Michi71/PicoVintageSynthCollection/tools/jv_extract/README.md

# jv_extract - JV-880 ROM extraction and parameter analysis

Host-side toolchain for a planned PicoFaceJV. Nothing here is part of a firmware
image, and no ROM data is in this repository.

The goal is **not** a cycle-exact emulation of the JV-880's CPUs. It is a native
engine that plays the converted PCM data and sounds like the original. That
requires two things from the ROMs: the sample data, and the meaning of the patch
parameters. This directory produces both.

## ROM images

You need your own JV-880 ROM set. Point the tools at a directory containing:

| File | Size | Purpose |
|---|---|---|
| `jv880_rom1.bin` | 32 KB | boot ROM, needed only by the reference emulator |
| `jv880_rom2.bin` | 256 KB | firmware; holds the multisample, sample and patch tables |
| `jv880_waverom1.bin` | 2 MB | wave data, scrambled |
| `jv880_waverom2.bin` | 2 MB | wave data, scrambled |
| `jv880_nvram.bin` | 32 KB | needed only by the reference emulator |

The SR-JV80 expansion boards are deliberately out of scope.

## Wave data format

Each 1 MB ROM page is self-contained:

```
  page + 0x00000 .. 0x07FFF   exponent nibbles, one per 16 samples
  page + 0x08000 .. 0xFFFFF   8-bit signed DPCM deltas
```

A sample is reconstructed by accumulating `delta << exponent`; the nibble for
address `a` sits at `(a & 0xFFFFF) >> 5` with bit 4 selecting high or low nibble.
Both wave ROMs are additionally scrambled by a fixed 20-bit address and 8-bit
data permutation (`descramble()` in `jv_rom.py`).

Verification: all 577 samples decode without a single clipped accumulator,
median peak 7.7 % of 20-bit full scale. Sample 0 (lowest split of "Ac Piano 1",
root key 40) has a loop period of 382 samples, implying 31.5 kHz -- the JV-880's
native rate.

## Tables in rom2

| Table | Offset | Layout |
|---|---|---|
| Multisamples | `0x0004` | 129 x 60 B: 12 B name, 15 split keys, 16 x uint16be sample index |
| Samples | `0x1E41` | 577 x 18 B: start/loop/end (24 bit), root key, tune, level |
| Patches | `0x008CE0` / `0x010CE0` / `0x018CE0` | 3 banks x 64 x 362 B |

A patch is 12 B name + 14 B common + 4 x 84 B tone. See `jv_tone_map.h`.

## Tools

| File | What it does |
|---|---|
| `jv_rom.py` | descrambling, table parsing, DPCM decoding, WAV dump. Importable; run directly for a ROM-set summary. |
| `jv_probe.cpp` | differential probe harness. Reads probe specs on stdin, renders each on the reference emulator, writes one CSV feature row per probe. |
| `jv_analyze.py` | `effects` / `curves` / `shape` views over that CSV. |
| `jv_tone_map.h` | the patch/tone layout, with each field marked VERIFIED or UNVERIFIED. |
| `jv_fx_taps.cpp` | address trace of the effect chip's delay memory. Run it through `build_fx_taps.sh`; see "The reverb, and where it stops". |
| `build_fx_taps.sh` | generates a hooked copy of the emulator's `pcm.cpp` into a scratch directory, builds the trace against it, runs it. |

### Building the probe

`jv_probe.cpp` links against the reference emulator, which is **not** vendored
here (see "Credit" below). Point it at your own checkout of
`giulioz/jv880_juce`; it needs only the emulator core, not the JUCE-coupled ROM
loader, because it brings its own:

```bash
JV=/path/to/jv880_juce/Source/emulator
c++ -O2 -std=c++17 -I"$JV" -I"$JV/resample" -o jv_probe tools/jv_extract/jv_probe.cpp \
    "$JV"/mcu.cpp "$JV"/mcu_opcodes.cpp "$JV"/mcu_interrupt.cpp "$JV"/mcu_timer.cpp \
    "$JV"/pcm.cpp "$JV"/submcu.cpp "$JV"/lcd.cpp "$JV"/resample/*.c
```

The emulator chatters on stderr while it boots; redirect it (`2>/dev/null`) or
the noise lands between the CSV rows.

### Running a sweep

Probe specs are `<label> <tone> <offset> <value>`. Lines labelled `#base` are
applied to the patch before every probe. Offset `-1` means "no modification".
A negative tone index addresses the patch bytes directly instead of a tone.

```bash
{ printf '#base 1 0 0\n#base 2 0 0\n#base 3 0 0\n'
  for o in $(seq 52 66); do for v in 0 16 32 48 64 80 96 112 127; do
    echo "P_${o}_${v} 0 $o $v"      # byte set on the live tone
    echo "C_${o}_${v} 3 $o $v"      # same byte on a switched-off tone
  done; done
} | ./jv_probe /path/to/roms 52 48 100 > sweep.csv

python3 tools/jv_extract/jv_analyze.py curves sweep.csv
```

## Two traps

Both of these produced confident, completely wrong results before they were
found. Anyone extending this work needs to know them.

**1. `SC55_Reset()` does not reset the emulator.** PCM, timer and resampler
state survive it, and so does `samplesError`. Results became order-dependent.
The harness therefore constructs a **fresh `MCU` per probe**. With that, four
repetitions of the same probe render bit-identically -- the noise floor is
exactly zero, so any difference at all is real.

**2. The firmware's patch-parse path takes different amounts of time depending
on which byte was touched**, which shifts the whole render by a few samples.
Summary features (level, pitch, release) cannot tell that apart from a genuine
parameter change: 27 unrelated offsets showed one identical phantom signature.
It surfaced only through a control experiment -- setting the same byte on a
*switched-off* tone produced a byte-identical render, and a silent tone cannot
change the sound.

Hence every measurement is **paired**: the byte is set both on the live tone and
on a switched-off one. The parse-timing shift is identical in both, so a
byte-identical render means the parameter is inert, and any difference is a real
effect. This is what `jv_analyze.py` compares -- never a probe against a global
baseline.

A consequence worth planning for: a parameter can only be measured on a base
patch that actually uses its section. A pipe-organ patch leaves 49 of the 84
tone bytes inert. Pick base patches by section usage, not by name.

## Calibration

Knowing *which* byte is the release time is not enough to build an engine; it
has to know that value 80 means 3.2 seconds. `JV_DUMP=<dir>` makes `jv_probe`
write the raw stereo render of every probe (float32 interleaved, note-off at
frame `JV_HOLD * 32000`), and `JV_HOLD` / `JV_REL` set the render length in
seconds. `jv_calibrate.py` turns those dumps into `jv_calibration.h`.

Results are in [`jv_calibration.h`](jv_calibration.h). The headline findings:

| Quantity | Law | Valid range |
|---|---|---|
| Envelope segment, falling | `t = 56.7 ms * 2^(v/13.98)` to −40 dB, R²=0.996 | v=16…112 |
| Envelope segment, rising | `t = 67.6 ms * 2^(v/14.06)` to 98 %, R²=0.997 | v=16…112 |
| TVF cutoff | `fc = 431 Hz * 2^(v/17.93)`, 67 cents/step, R²=0.984 | v=8…84 |
| LFO rate | `f = 0.122 Hz * 2^(v/18.20)` | whole range |
| LFO delay / fade | `32.3 ms * 2^(v/12.0)` / `17.5 ms * 2^(v/10.5)` | v≳40 |
| TVA level, pan | tables (not a clean power law) | full |

**Envelope shape is direction-dependent** and this matters more than the times:
rising segments ramp *linearly in amplitude*, falling segments decay *linearly
in dB*. Both were measured at ten equal time points across several rates; the
rising shape is identical at every rate.

**The time is the segment's DURATION, not a rate.** At T1 = 80 the attack takes
about 3.4 s whether its target level is 64, 96 or 127 — a constant rate would
have given 1.7 / 2.6 / 3.5 s. This matters far beyond the timing: a stage whose
target equals the current level is a *hold*, and reading the time as a rate
collapses it to nothing. Several factory pads (B19 "Beauty Vox", B21 "Pvox
Oooze") have L1 = L2 = 127 and stuttered because of it.

### The measurement setup is the hard part

Two things silently ruined earlier runs, both worth repeating:

* **The base patch's own LFO.** Pipe Organ (A24) carries `lfo1TvaDepth = 255`.
  Its tremolo swamped the amplitude envelope, so attack curves came out
  oscillating instead of rising. Every calibration base must zero the six LFO
  depth bytes (+31…+36).
* **Reverb and chorus sends.** Left at patch defaults they add a tail that gets
  measured as release time. Set +82 and +83 to 0, +81 to 127.

The base used for all of it is a sine wave (multisample 72), single tone, LFOs
off, sends dry, filter open, envelope levels at maximum — so that the one byte
under test is the only thing moving.

### Envelope target levels

The TVA envelope's target levels (+75/+77/+79) do **not** follow the tvaLevel
curve, which the engine assumed at first. Measured by setting every segment time
to 0 and every target to the same value -- the envelope then holds there -- the
two curves differ by up to **9.4 dB** at low levels. Above roughly L=32 the
envelope curve is linear at 0.30 dB per unit.

The TVF envelope's levels are a different quantity again: they scale the cutoff
excursion and are **near-linear in the parameter**, not logarithmic. Normalised
to L=127 they run 0 / 0.09 / 0.20 / 0.28 / 0.46 / 0.56 / 0.72 / 0.83 / 1.0 at
L=0…127, where the dB curve would give 0.09 at L=32 instead of 0.20.

**Four** level-shaped quantities, and no two share a curve:
`JV_TVA_LEVEL_DB` for tone levels, `JV_PATCH_LEVEL_DB` for the patch-common
level, `JV_TVA_ENV_LEVEL_DB` for TVA envelope targets, `JV_TVF_ENV_LEVEL` for
TVF envelope targets. Assuming one curve for all of them was wrong four times
over; each was settled by patching the byte and reading the sustained level.

And a fifth candidate that turned out not to be one: **byte +17 of a sample
record is not a level**. Patched across its whole range, including 0, it moved
the output by 0.00 dB. The engine had been multiplying by it, which wrongly
attenuated the 233 of 577 samples carrying anything other than 127 -- by up to
6.4 dB, and one of them to silence.

### Pan does not stop at 127

`tvaPan` (+68) has three regimes, found by sweeping the whole byte rather than
the 0..127 the field looks like:

| value | behaviour |
|---|---|
| 0…127 | the continuous law: 0 left, 64 centre, 127 right |
| **128** | **alternating** -- the balance jumps between 0.119 and 0.768 from one note to the next |
| 129…255 | centre |

**139 of the 539 active factory tones carry 128.** Clamping it to 127, as the
engine did, threw all of them hard right with the left channel 39 dB down.
"Whistle" has 128 on all four of its tones, which is why it measured 14 dB quiet
-- the mono sum had lost a whole channel.

### Tone summing

Not a factor. Enabling the four tones of "Pipe Organ 1" one at a time, the
machine gains +2.3 / +0.3 / +1.2 dB and the engine +2.8 / +0.5 / +0.4 dB, so
there is no hidden per-tone attenuation; only a constant offset separated them.

### Filter chain, measured against the reference

The low-pass slope is **−10 to −12 dB/octave**, so the two-pole assumption is
right, and the transfer function tracks the reference to 1–4 dB across four
cutoff settings. The filter is not where the remaining timbre error lives.

Worth recording as a method note: an earlier comparison normalised each spectrum
to its own maximum and read single FFT bins, which suggested a 26 dB error at
1 kHz. Measured absolutely and in third-octave bands, the same patch is within
1.8 dB up to 4 kHz and only +3.5/+7.4 dB at 8/12 kHz -- consistent with the
chip's three-coefficient interpolation over the deltas against the engine's
linear interpolation, which is a real but much smaller difference.

### Where it is incomplete

* **Cutoff above v≈84** cannot be measured this way: the corner moves past the
  bandwidth of the white-noise sample used as excitation. A wider excitation
  (or a swept sine) would extend it.
* **Flags bit 5** of either LFO (see "Key sync and offset" above).
* **tvfEnvDepth (+58)** moves the cutoff by 2.4 parameter units per depth unit
  (measured 19.1 / 37.5 / 60.5 at depth 8 / 16 / 24, with the envelope held
  open); above 24 the measurement saturates, not the synth. The field is signed.
* **tvaVelocity (+72) only ATTENUATES.** Measured against sensitivity 0 at the
  *same* velocity -- a comparison the first calibration never made -- every
  setting gives an identical level at velocity 127, and softer notes get quieter
  in proportion: -1.56 / -3.10 / -4.91 dB at velocity 100 for sensitivities
  8 / 16 / 25, and -3.59 / -7.52 / -11.62 dB at velocity 64. The attenuation
  tracks the product `sensitivity * (127 - velocity)`.

  RE-MEASURED on a full grid -- nine sensitivities against eight velocities,
  63 usable points -- after a listening report that middle velocities came out
  too quiet. The product model itself holds: three independent settings near
  product 1500 give 9.82 / 10.33 / 10.51 dB and near 2000 give 13.01 / 13.01 /
  13.51. What was wrong was the curve through them. The old table was built
  from just two velocities, 100 and 64, and ran 1 to 3 dB too steep through the
  middle of the range -- exactly where MIDI files live -- and badly steep at the
  top: 45.25 dB against the machine's 37.78 at product 3969.

  With the new table the engine reproduces the grid to a mean absolute error of
  **0.33 dB** over all 63 points, against roughly 1 dB before.

  Worth being clear about what this did NOT fix. Measured per patch, the drop
  from velocity 127 to 64 is now right on ten patches and slightly too shallow
  on eleven; before it was uniformly a little too steep. The isolated law being
  accurate to 0.33 dB while whole patches still scatter by about a decibel says
  a second mechanism is involved -- most likely the TVF velocity sensitivity,
  which darkens the tone at lower velocity and takes level with it. That is the
  next thing to measure.

  The first model boosted above velocity 64 instead. Because factory patches
  carry sensitivities of 13..42, that spurious boost had been standing in for a
  10.5 dB base offset in the output normalisation, and the two together looked
  acceptable in aggregate while scattering wildly per patch. Fixing the law and
  moving the normalisation cut the spread across 24 patches from 5.1 dB to
  2.7 dB. The lesson is in the comparison that was missing: every velocity
  measurement had been relative to velocity 64 at the same sensitivity, so a
  term that shifts the whole curve was invisible.
* **LFO depths are signed over the whole byte.** 64..127 really is inert, but
  128..255 is -128..-1 and modulates the *other way*: pitch depth -20 gives
  133 cents of swing around a mean above the carrier, +20 gives 136 cents around
  a mean below it. An earlier sweep only covered 0..127 and wrongly concluded
  that everything from 64 up was off. On the TVA the negative side is inaudible
  at full level, because there is no headroom to modulate upward into.
* **Resonance** is calibrated (see the matrix section); the LFO's TVF depth
  is not.

## Pitch: the sample table, resolved

The `tune` word had resisted a structural reading, so it was settled the same
way the patch bytes were — by **patching rom2 itself** and measuring. `jv_probe`
takes `#rom <offset> <value>` lines for exactly this; they are applied before
the MCU starts, so any ROM table can be probed the way patch bytes are.

| Field | Law | Evidence |
|---|---|---|
| root key (+12) | exact semitones | −199.9 / −200.2 cents per +2, five values |
| `tune` (+13/+14, 16-bit BE) | **0.1 cent per unit, neutral at 1024** | low byte 0.098–0.100 cents/unit over six values; high byte 0.1005 |
| `pitchFine` (tone +38) | 1 cent per unit, signed | 0.989–1.001 cents/unit over eight values |
| machine tuning | 9.4 cents flat | constant to 1 cent across 2.5 octaves |

**`end` is inclusive**: a loop spans `end − loop + 1` samples. This was the
thing that made everything else look inconsistent. Treating `end` as exclusive
detunes a sample by 1731/looplen cents — 9 cents on a 193-sample loop but 54 on
a 32-sample one — so the error masqueraded as a per-sample `tune` effect that no
single law could fit.

The two readings are cleanly separable. Solving each sine-multisample zone for
the `tune` reference point gives:

| `end` treated as | reference point per zone | scatter |
|---|---|---|
| exclusive | 1207, 1246, 1303, 1371, 1484, 1671 | 157.7 |
| **inclusive** | 1118, 1119, 1119, 1111, 1120, 1121 | **3.3** |

and 1118 − 1024 = 94 units = 9.4 cents, which is exactly the machine's measured
offset from equal temperament. The neutral value really is 0x400 after all;
what was missing was the off-by-one and the global detune sitting on top of it.

Engine error against the reference afterwards: **0.2 to 0.7 cents** across all
nine zones of the sine multisample, down from +22…+105 cents. On real
multi-tone patches the residual is 5 cents mean / 9 cents worst, which is
dominated by f0 estimation over detuned layers rather than by the model.

### LFO

Waveform comes from bits 0-2 of the flags byte, classified by correlating the
measured dB envelope against ideal shapes: **0/6/7 triangle** (0.990),
**1 sine** (0.990), **2 sawtooth** (0.986), **3 square** (0.984). Values **4 and
5 are not periodic** — only 21 % of their samples sit on a smooth slope against
99-100 % for the rest — so both are treated as sample-and-hold.

Depth is effective for **0..63 only**; every value from 64 up reproduced the
unmodulated signal exactly, so it disables the modulation rather than inverting
it. An earlier note calling these fields "bipolar, split at 64" was wrong.

Both destinations modulate **one-sided downward** from the set value: with
rising TVA depth the peak stayed at −15.0…−15.9 dBFS while the trough fell to
−62.5 dBFS, and the mean pitch dropped from 261 to 194 Hz.

An earlier claim here — that no modulation exists below rate ≈48 — was also
wrong. Re-measured with a 46 dB tremolo over 24 s and counting cycles directly,
the LFO runs at every rate value and matches the fitted law to ~1 % from v=40 up;
below that the cycle count is the limit, not the law. The original measurement
had an autocorrelation locking onto its search bound.

#### Key sync and offset

**Bit 6 is key sync.** Told apart by shifting the note-on in time (`JV_WARM`)
and timing the first square-wave edge. With the bit clear, the edge moves so
that edge+shift stays constant modulo the period — a free-running LFO. With it
set, the edge sits at 227.7–237.7 ms regardless of the shift, scatter 3.4 ms
against ~56 ms for free-running.

Phase 0 is the **unmodulated** end. The 227 ms is a useful cross-check on two
earlier results at once: half a period (194.7 ms at rate 80) plus the 32.3 ms
floor of the delay law.

**Bits 3-4 are an offset that shrinks the swing from the bottom.** The peak does
not move (−15.1…−15.2 dBFS across all four settings) and neither does the phase
(first edge 237.6–239.0 ms, duty 49–50 %); only the trough rises. At TVA depth
63 the swing goes 48.7 / 30.6 / 19.4 / 9.9 dB, and the triangle agrees
(48.1 / 29.5 / 18.5 / 9.0). Stored as a scale factor on the depth.

**Bit 5 is not resolved.** Alone it silences the modulation; combined with
either of bits 3-4 the swing collapses to a fixed 19.4 dB regardless of which,
which no plain offset field explains. The engine ignores it.

#### LFO 2 is the same device

Probed separately rather than assumed. Rate follows the same law (within 1 %
from v=56 up; the 12 % at v=32 is cycle-count quantisation, not a difference),
the four periodic waveforms have the same shapes at the same codes, value 4 is
equally aperiodic, depth follows the same table and is equally disabled from 64
up, key sync behaves the same (scatter 45.4 ms free-running against 3.2 ms
synced), and the four offset settings give **bit-identical** swings to LFO 1
(48.7 / 30.6 / 19.4 / 9.9 dB, difference −0.0 dB throughout).

The two also free-run in lockstep: at equal rates their first square edges land
on the same milliseconds.

### Modulation matrix

Its three sources — mod wheel (CC 1), aftertouch, expression (CC 11) — need
controller traffic, which a bare note-on does not provide, so `jv_probe` gained
`#midi <seconds after note-on> <status> <d1> [d2]`. Messages are queued, sorted
and injected by splitting the hold render at their timestamps.

**Sensitivity is signed with an effective range of ±63, and 64…127 disables it
outright** — the same convention as the LFO depths. This was the whole reason an
early sweep found nothing: it used sensitivity 127. The pitch destination scales
linearly at **19.05 cents per unit**, reaching exactly ±1 octave at ±63
(measured 18.3 / 37.3 / 94.4 / 188.3 / 377.3 / 765.3 / 1200.2 cents for
1 / 2 / 5 / 10 / 20 / 40 / 63).

Destination A is the **low** nibble of the DestAB byte, B the high one — which
is what the factory patches imply too (Dig Rhodes 1 has expression DestAB = 0x20
with SensA = 0 and SensB = 20, so the active destination sits in the high
nibble alongside the active sensitivity).

| Code | Effect | How it was told apart |
|---|---|---|
| 0 | off | — |
| 1 | **pitch** | +376 cents; the ×1.55 brightness is exactly the side effect of the shift on a sine |
| 2 | **cutoff** | corner ×2.50 with the filter enabled |
| 3 | **resonance** | spectral peak +4.4/+8.4/+12.6 dB at sensitivity 20/40/63, against +3.5/+9.0/+12.5 dB for resonance set directly to 30/90/127 |
| 4 | **level** | +4.3 dB, nothing else moves |
| 5, 6 | **LFO 1 / 2 pitch depth** | the pitch wobbles rather than steps; source identified by rate |
| 11-15 | nothing measurable | — |
| 7, 8 | **LFO depth → filter** | oscillation index ×45 / ×34 at the LFO rate |
| 9, 10 | **LFO depth → level** | oscillation index ×73 / ×57 |

The LFO destinations were separated from the static ones by running the LFO at a
known rate with all depths at zero and testing whether the controller introduces
a periodic component at that rate. It is an unambiguous split: the four LFO
codes jump 34–73×, everything else stays at or below 1.1×.

Which LFO each of 7-10 drives was settled by giving the two LFOs different rates
and seeing which one the induced oscillation follows: **7 = LFO 1 filter,
8 = LFO 2 filter, 9 = LFO 1 level, 10 = LFO 2 level**. Adding sensitivity 63 at
full travel reproduces full depth (47.7 dB against the depth table's 46.6), so
the matrix adds straight onto the depth parameter.

Scalings, all with the wheel swept 0 -> 127: pitch **19.05 cents/unit** (exactly
±1 octave at ±63), cutoff **~128 cents/unit**, level non-linear and saturating
near **+6.3 dB** (1.29 / 2.37 / 4.31 / 6.28 dB at sensitivity 5 / 10 / 20 / 40).

Destinations 5 and 6 took two attempts and are worth a warning. Averaged over a
long window their pitch looks like a small static shift, which is what the first
sweep concluded; tracked in 0.12 s windows it plainly wobbles instead of
stepping. At sensitivity 40 the swing reaches 4000 cents, enough to make an
autocorrelation tracker jump octaves and smear the rate across both LFOs — only
at sensitivity 4-8 does the source come out unambiguous. Destination 6 had been
written off as "nothing measurable" for the same reason.

The matrix's pitch-depth contribution is linear **in cents** (55 and 122 cents
at sensitivity 4 and 8), not in depth-parameter units as the level and filter
depths are.

Resonance needed the engine's filter damping calibrated as well: peak gain
against the passband is +1.0 / +3.5 / +6.2 / +9.0 / +12.5 dB at resonance
0 / 30 / 60 / 90 / 127, which fixes k = 1/Q. The first mapping was a guess and
overshot by 7 dB at the top.

Still not established: whether the B/C/D slots behave like A, destinations
11-15, and behaviour on real multi-tone patches — see below.

#### What the engine does and does not reproduce

Against the controlled synthetic base the engine matches: pitch to 0.6-3.8
cents across the whole sensitivity range including the disable above 63, level
exactly, cutoff to 83-173 cents, LFO-depth destinations to 0.1-3.0 dB.

On **real factory patches it is not verified**. The patches that use the matrix
are decaying Rhodes and piano sounds whose own envelope contaminates a
before/after window comparison — the oscillation detector reads a decay ramp as
modulation, so it cannot separate the two. A10 "SA Rhodes" (destination 10,
sensitivity 20, on three tones) is the concrete case: the reference's level
rises 2.4 dB with the wheel, the engine's falls 2.9 dB, and the measurement is
not good enough to say which is right.

### Zone selection, verified

`splits[k]` is the **inclusive upper bound** of zone k: zone 0 covers notes up
to `splits[0]`, zone k covers `splits[k-1]+1 .. splits[k]`, and the last zone
runs to 127. Verified by repointing one zone's entry in the multisample index
table at the white-noise sample (516) and sweeping notes: 34 boundary tests
across all nine zones of the sine multisample, all correct.

Pitch is the wrong observable for this. A first attempt shifted a zone's sample
root by an octave and looked for the jump; it produced a self-contradictory map
(note 87 apparently in a different zone than 86 and 88) because the f0 estimator
was locking onto harmonics. The noise marker has no such ambiguity — the
separation is absolute:

| | measurements | spectral flatness |
|---|---|---|
| note outside the patched zone | 16 | 0.000000, every one |
| note inside it | 18 | 0.000477 … 1.000000 |

The low readings are not weak detections: the noise sample transposed down two
octaves is no longer spectrally flat, but it is still unambiguously not the sine.

### Velocity curves, and a trap worth naming

The seven velocity curves (+55 bits 0-2 for the TVF, +71 bits 0-2 for the TVA)
were first implemented from the icons the manual prints, which put an `x^2` law
on stored curve 0. That quietly took 3 dB off half the factory patches. The
sweep that replaced it -- a tone forced to a flat sustain at velocity
sensitivity 32, read at nine velocities for each of the seven settings -- gives
`JV_VELO_CURVE` in jv_calibration.h and settles three things:

* All seven curves produce **exactly the same level at velocity 127**. That is
  the anchor, the same one the sensitivity law itself uses.
* **Stored curve 0 is the straight line.** Expressing each curve as "the
  velocity curve 0 would need to reach the same level" makes curve 0 an exact
  identity, which is the right footing because `JV_TVA_VELO_ATTEN_DB` was itself
  measured on curve 0.
* The reparameterisation holds across sensitivities. Repeating the sweep at
  sensitivity 16 reproduced curve 1's effective velocities to within 1.5 units
  wherever both are well conditioned, so the curve warps velocity *before* the
  sensitivity law rather than acting on the result.

Checked against the reference on real patches, the drop from velocity 127 to
100 is 8.76 / 8.22 / 13.71 dB on A37, B06 and B50 against 8.98 / 8.18 / 14.14
predicted with the curve and 4.28 / 3.87 / 7.03 without it. A11 lands between
the two, which is right: it is the one of those patches that mixes curve 0 and
curve 1 across its tones.

**The trap.** Fixing this made the aggregate level error look *worse* -- and it
was the third time in this work that a wrong law and the output normalisation
had silently absorbed each other. A velocity-law error is indistinguishable
from a level offset unless the comparison is made at more than one velocity.
Two habits catch it:

* Always compare at both velocity 127 and something well below it. Before the
  curves the engine was flat at one velocity and 4-5 dB out at the other; the
  single-velocity summary showed neither.
* Match the measurement windows. `jv_probe` reports rms over the HELD portion
  only (`N = nHold`), while `jv_engine_test` reports it over hold plus release.
  Comparing the two directly puts a patch-dependent 3 dB bias on every reading,
  which is enough to hide or invent an error of exactly the size being chased.

With the curves in and the normalisation re-trimmed by 1.0 dB (99000 ->
88234), the level error over all 128 factory patches at velocities 127 and 100
is mean +0.15 dB, spread 3.0 dB, mean absolute 2.32 dB -- and the velocity
TRACKING error, which is what the curves actually fix, falls from a mean of
1.22 dB to 0.72 dB with the worst case down from 6.7 to 5.0 dB.

### The machine is at equal temperament, and the 9.4 cents were counted twice

The engine carried a global `kMasterTuneCents = -9.4`, documented here as a
measured property of the machine. It is not one. The reference playing the
ROM's own sine (multisample 72) sits at **+0.11 / +0.18 / +0.08 cents** against
equal temperament at C3, C4 and C5 -- dead in tune. The engine was 9.65 cents
flat, and removing the constant lands it at +0.12 / +0.19 / +0.13.

9.4 cents is real, but it belongs to the tune-word model: it is the residual
left over when the sample tune words are referenced to a neutral of 1024.
Applying it again as a global detune counted it a second time. The whole
instrument played ten cents flat, which is inaudible on its own and obvious
against anything else.

That is the same shape as the two velocity traps below, and the third instance
in this work: a constant belonging to one part of the chain quietly standing in
for an error elsewhere, invisible until something *outside* the chain is
measured. Here the outside reference was equal temperament itself.

### The loop throb: alternating loops, and a test that lied

**Resolved.** Bit 0 of a sample record's flag byte (+11) marks an **alternating
loop**: playback turns around at the end and retraces the loop backwards rather
than jumping to the start. 85 of the 577 samples set it, and they are the long
sustained ones -- median loop length 8998 against 152 for the rest. Playing
those as forward loops makes the sound repeat exactly once per loop, which is
audible as a throb at the loop rate: 2.43 Hz for the sample under B16.

**The return pass is NEGATED.** The chip does not undo the differential steps
on the way back. It keeps integrating in the same direction while the address
walks backwards, so what comes out is `2*v(end) - v(mirrored)`. The loop
endpoints sit on zero crossings -- `v(end)` is exactly 0 for every sample
checked -- so that is the negated mirror of the forward pass.

Retracing the arithmetically "correct" way, `v(a-1) = v(a) - delta(a)`, gives
the un-negated mirror. Against the reference that reads **r = -0.995** through
the whole return pass: perfectly shaped, exactly the wrong sign. It is audible
as a tick at each turn-around, since the waveform jumps to its own negative
there. Adding the delta instead of subtracting it takes the same comparison to
**+0.99**.

With that, the engine tracks the reference sample for sample: aligning on a
window at 200 ms and then measuring 50 ms windows out to 1.8 s gives r = 0.92
to 1.00 throughout, across four turn-arounds, with the alignment drifting only
from +86 to +90 samples (about a cent of rate difference).

The measured signature, engine against reference, envelope correlation at one
loop period across the seven notes of one multisample zone:

| note | reference | forward loop | alternating |
|---|---|---|---|
| 55 | -0.369 | +0.434 | -0.302 |
| 57 | -0.388 | +0.544 | -0.342 |
| 59 | -0.333 | +0.692 | -0.453 |
| 60 | -0.441 | +0.705 | -0.382 |
| 62 | -0.512 | +0.595 | -0.466 |
| 64 | -0.591 | +0.627 | -0.537 |
| 66 | -0.572 | +0.753 | -0.519 |

And directly: comparing one loop pass against the next, the reference matches
its own **reverse** at +0.899 while matching forward at -0.046. The engine gave
+0.871 forward before this and now shows the reference's signature instead.

**The test that lied.** Alternating looping was the second hypothesis tried and
was wrongly discarded, because the first version of the test correlated one
half-period against the reversed next half-period from an *arbitrary* window
start. The turn-around point sits at the loop boundary, so an unaligned window
straddles a reversal and the correlation collapses -- it read +0.076 and sent
the search off for six other explanations. Scanning the window offset instead
of assuming one makes the peak obvious. When a structural hypothesis is
rejected, check whether the test could see it at all before believing the
result.

Bit 1 of the same byte marks a one-shot: all 42 samples carrying it have
`loop == end`, so the forward path already holds on the last value. Bit 2 is
still unidentified, on 15 samples.

### What it was not

B16 was the clean test case: one tone, every LFO depth zero, no random pitch,
no analog feel, no FXM, pan centre -- a single unmodulated sample, so anything
periodic had to come from the playback. These were eliminated on the way, and
each elimination is still worth having:

* **The chorus.** These patches are built around a deep slow chorus that the
  engine does not have, which was the obvious suspect. But switching the chorus
  off on the reference leaves it just as non-periodic (r at the loop period goes
  from -0.34 to -0.30).
* **The DPCM accumulator, and the decode rule.** The loops are authored exactly
  balanced: the drift over one pass is precisely zero for all three samples
  involved, under every plausible variant of the decode step (`s>>1`, `s`,
  truncate-toward-zero, round-half-up). The `refAtLoop` snapshot the engine
  restores on each wrap is therefore a no-op for these samples, and removing it
  would change nothing.
* **A loop-length parity effect.** An odd loop length would flip the alignment
  of the DPCM exponent nibbles every pass, which would explain a two-pass cycle.
  Patching sample 287's `end` in rom2 to make the length even (12779 -> 12778)
  moves the reference's r only from -0.44 to -0.28. Not it.
* **A discontinuity in the engine.** There is none. Replaying the engine's own
  decode and loop logic step by step across the wrap gives
  `... -872, 0, +888, +1768 ...` -- perfectly smooth -- and the rendered
  waveform either side of the boundary is continuous sample for sample. What
  looked like a step in a 10 ms envelope is a fast but continuous swell that
  sits at the boundary because the sample's own amplitude pattern restarts
  there. That is the whole point: it restarts EXACTLY.
* **The loop being twice as long as read.** The reference's best repeat is at
  831 ms, twice the period, which would fit `end` being misread. It is not:
  the next sample record starts 5 bytes after sample 287 ends, so there is no
  data for a longer loop.
* **A fractional-phase effect.** The engine advances only 0.1 to 0.8 output
  samples per pass depending on note, and its correlation shows no relation to
  that fraction; neither does the reference's.

Each of these was a real elimination, and the sample data being provably
periodic while the address returns to exactly the same place is what finally
pointed at the traversal itself rather than the data.

### Still open

* **Cutoff above v≈84** and the **LFO below v≈48** (see Calibration above).
* **tvfEnvDepth (+58)** moves the cutoff by 2.4 parameter units per depth unit
  (measured 19.1 / 37.5 / 60.5 at depth 8 / 16 / 24, with the envelope held
  open); above 24 the measurement saturates, not the synth. The field is signed.
* **tvaVelocity (+72) only ATTENUATES.** Measured against sensitivity 0 at the
  *same* velocity -- a comparison the first calibration never made -- every
  setting gives an identical level at velocity 127, and softer notes get quieter
  in proportion: -1.56 / -3.10 / -4.91 dB at velocity 100 for sensitivities
  8 / 16 / 25, and -3.59 / -7.52 / -11.62 dB at velocity 64. The attenuation
  tracks the product `sensitivity * (127 - velocity)`.

  RE-MEASURED on a full grid -- nine sensitivities against eight velocities,
  63 usable points -- after a listening report that middle velocities came out
  too quiet. The product model itself holds: three independent settings near
  product 1500 give 9.82 / 10.33 / 10.51 dB and near 2000 give 13.01 / 13.01 /
  13.51. What was wrong was the curve through them. The old table was built
  from just two velocities, 100 and 64, and ran 1 to 3 dB too steep through the
  middle of the range -- exactly where MIDI files live -- and badly steep at the
  top: 45.25 dB against the machine's 37.78 at product 3969.

  With the new table the engine reproduces the grid to a mean absolute error of
  **0.33 dB** over all 63 points, against roughly 1 dB before.

  Worth being clear about what this did NOT fix. Measured per patch, the drop
  from velocity 127 to 64 is now right on ten patches and slightly too shallow
  on eleven; before it was uniformly a little too steep. The isolated law being
  accurate to 0.33 dB while whole patches still scatter by about a decibel says
  a second mechanism is involved -- most likely the TVF velocity sensitivity,
  which darkens the tone at lower velocity and takes level with it. That is the
  next thing to measure.

  The first model boosted above velocity 64 instead. Because factory patches
  carry sensitivities of 13..42, that spurious boost had been standing in for a
  10.5 dB base offset in the output normalisation, and the two together looked
  acceptable in aggregate while scattering wildly per patch. Fixing the law and
  moving the normalisation cut the spread across 24 patches from 5.1 dB to
  2.7 dB. The lesson is in the comparison that was missing: every velocity
  measurement had been relative to velocity 64 at the same sensitivity, so a
  term that shifts the whole curve was invisible.
* **LFO depths are signed over the whole byte.** 64..127 really is inert, but
  128..255 is -128..-1 and modulates the *other way*: pitch depth -20 gives
  133 cents of swing around a mean above the carrier, +20 gives 136 cents around
  a mean below it. An earlier sweep only covered 0..127 and wrongly concluded
  that everything from 64 up was off. On the TVA the negative side is inaudible
  at full level, because there is no headroom to modulate upward into.
* **Resonance** is calibrated (see the matrix section); the LFO's TVF depth
  is not.
* **tvfVelocity (+56)** is calibrated. Measured with the TVF envelope held wide
  open over a base cutoff of 8, reading brightness back as an effective depth:

      positive sensitivity   f = 1 - (s/32) * (127 - v)/127
      negative sensitivity   f = 1 - (|s|/32) *  v /127

  clamped to 0..1, fitted over 96 points to a mean error of 0.010. The constant
  is **32, not 63** -- sensitivity 32 already takes the depth to zero at
  velocity 0, so the upper half of the field saturates inside the velocity span.
  Assuming 63 by analogy with the other bipolar fields made the effect half as
  strong as the machine everywhere. Positive sensitivity pivots at velocity 127
  like the TVA law; negative pivots at velocity 0.

  Note the measurement trap: brightness stops resolving above envelope depth 32,
  so the first sweep -- run at depth 40 -- read a flat 0.0187 across the whole
  useful range and looked like no effect at all. Depth 28 keeps every reading on
  the curve.

## What the owner's manual adds

The JV-880 owner's manual (Roland, 244 pages, scanned -- no text layer, so it
has to be read as images) turned out to carry two things the probe could not
produce on its own. Section 10's **parameter address map** (printed 10-38 f.)
lists the SysEx view of a tone: 116 addresses, `0x00`..`0x73`, five of them
nibble pairs, which is the same parameter set as the 84 packed bytes here. That
names every field and gives its range. Section 6 then explains what each one
actually does.

The manual is documentation, not measurement: where the two collide the
measurement wins. Its value here was in saying where to point the probe next,
and most of the list below has since been implemented and checked against the
reference. What that pass achieved, over all 128 factory patches:

| metric (vs reference) | before | after |
|---|---|---|
| level, mean absolute error | 2.45 dB | 2.33 dB |
| velocity tracking error, 127 -> 100 | 1.22 dB | 0.72 dB |
| brightness at velocity 64, mean abs err | 10.19 dB | 4.93 dB |

**Resolved outright.**

* **The modulation matrix destination table is complete at 13 entries**, 0..12:
  OFF, PITCH, CUTOFF, RESONANCE, LEVEL, PITCH LFO1, PITCH LFO2, TVF LFO1,
  TVF LFO2, TVA LFO1, TVA LFO2, LFO1 RATE, LFO2 RATE. Codes 13..15 do not
  exist, so the sweep that found nothing there was right. Dest 6 and 11/12 read
  as dead for a duller reason: the base patch had LFO2 pitch depth at zero and
  no LFO running, so there was nothing for them to scale.
* **LFO offset has five settings, not four** (-100/-50/0/+50/+100), so it needs
  three bits and **bit 5 of the LFO flags byte is its top bit** -- which is
  exactly why sweeping bit 5 on its own looked inert. That also means the
  remaining flag is fade polarity IN/OUT.
* **Offset is a shift, not a scale.** `JV_LFO_OFFSET_SCALE` shrinks the swing;
  the manual shows the waveform being pushed until it sits wholly above (+100)
  or wholly below (-100) the centre, at full amplitude. Applied to pitch with a
  square wave that is a one-sided trill, not a weaker vibrato.
* **Fade OUT** runs the LFO at full depth from note-on and fades it away over
  the fade time -- the engine only implements fade IN.
* **LFO delay and tone delay both have a KEY-OFF setting past 127**, holding the
  LFO (or the whole tone) until the key is released.
* **+54 and +40 are keyfollow pairs.** +54 packs cutoff keyfollow (0..15,
  -100..+200 about C4) with the TVF envelope's time keyfollow; +40 packs pitch
  keyfollow (0..15, +100 = the normal octave per twelve keys) with a TVA time
  keyfollow. Cutoff keyfollow is the consequential one: without it every tone
  filters at the same absolute frequency across the whole keyboard.
* **+71 is tone delay mode plus the TVA velocity curve.** NORMAL delays the tone
  and still lets it sound after release, HOLD drops it if the key goes up first,
  PLAY-MATE uses the gap between the last two note-ons as the delay time.
* **+72's upper half is probably the negative side.** The manual gives TVA
  velocity sensitivity as -63..+63, where negative makes *harder* playing
  quieter. The measurement covered only the positive half and called the rest
  inert -- the same shape the LFO depths had before the signed sweep found
  128..255 modulating the other way. Worth the same sweep.

**Since implemented.** How many of the 539 active factory tones each one
actually reaches is what decided the order:

1. **TVF envelope velocity (+56)** -- 336 tones. Measured; see "Still open"
   above for the law. This is what moved the brightness error.
2. **Velocity curves** (+55 and +71, bits 0-2) -- 204 tones on the TVF, 168 on
   the TVA. Measured; see the section above.
3. **Cutoff keyfollow** (+54 low nibble) -- 185 tones. At +100 % the corner
   tracks the keyboard one for one about C4, which falls straight out of the
   already-measured cutoff law: 17.93 parameter units per octave.
4. **TVF envelope release level (+66)** -- 95 tones. The TVF envelope releases
   to its own fourth level, not to zero; releasing to zero shut the filter on
   note-off while the TVA tail was still sounding.
5. **Level and panning keyfollow** (+70 low, +39 high) -- roughly 95 tones
   each. Per-semitone amounts are NOT measured, only the table indices.
6. **The pitch envelope (+40..+51)** -- 68 tones, 33 of them at full depth.
   Depth is signed semitones clamped to ±12; the four levels are bipolar where
   the TVA and TVF levels are unsigned. Runs at control rate.
7. **Pitch keyfollow** (+40 low) -- 32 tones. 507 sit at +100 %, the normal
   octave per twelve keys.
8. **Output dry level (+81)** -- 31 tones, six at or near zero. Those are heard
   only through the effects on the hardware, so with no effects yet they drop
   out; no patch loses all four tones that way.
9. **Random pitch (+39 low)** -- 18 tones -- and **analog feel** (patch common,
   119 of 192 patches). Both exist to stop tones phase-locking; the analog-feel
   magnitude is a guess, flagged in jv_calibration.h.
10. **Per-patch bend range** -- 24 patches bend down further than they bend up.
11. **LFO offset as a three-bit field** and **fade polarity** -- five tones and
    two tones respectively, but see the offset note in jv_calibration.h: the
    neutral index is 2, not 0, which is why the depth tables and the offset
    scale had been cancelling each other unnoticed.

12. **FXM (+02)** -- 24 tones. Measured; see jv_calibration.h. The engine's
    sidebands now sit within 0.3 dB of the reference across the depth range
    (-30.8 / -16.8 / -11.5 / -5.9 dB at depth 0 / 4 / 8 / 15 against
    -30.8 / -16.8 / -11.5 / -6.2).

**Still not implemented.**

* **POLY/SOLO and portamento** (11 and 6 patches). Needs a note stack and a
  glide; the engine is poly-only.
* **Resonance mode SOFT/HARD** (+53 bit 7, 58 tones).
* **Tone delay** (+69/+71) including the HOLD and PLAY-MATE modes.
* **Envelope time keyfollow and the T1/T4 velocity fields** (+42, +57, +73,
  plus the high nibbles of +40/+54/+70). Almost all neutral in the factory
  banks: +42 is (7,7) on 537 of 539 tones.

**Confirmed, no change needed.** The TVA envelope's shape (T1→L1, T2→L2,
T3→L3, hold, then T4→0 with no L4, while the TVF envelope does carry L4);
velocity range lower/upper as a per-tone window; pan L64..63R with 128 as the
setting the panel calls RND; patch level, tone level and the sends all being
independent 0..127 controls.

## The chorus

Measured by isolating it: the tone's dry level at 0 and its chorus send at 127
makes the output nothing BUT the chorus, and cross-correlating that against a
dry render of the same note recovers the delay as a function of time. The ROM's
own white noise (multisample 74) is the source; the sine (72) is better for
anything to do with pitch.

It is a **stereo modulated delay**, base delay 578 samples (18.06 ms), the two
channels sweeping in **antiphase** with a common minimum -- the modulation only
ever lengthens. Depth sets the delay SLOPE, rate sets the LFO period, and the
excursion follows:

    slope     = 1.738 * (depth + 18) samples/s   (252 at full depth)
    f         = 126 / (183 - 1.344 * rate) Hz    (0.69 Hz at 0, 10.2 at 127)
    excursion = slope / (2f)

That reproduces all sixteen measured rate points and four depth points to about
2 %, and correctly predicts that the period does not depend on depth (760 ms at
rate 64 for every depth, measured). Level is exactly linear in the parameter
with a full scale of 1.30; feedback is a comb with `g = 0.72 * fb/127`; bit 7 of
the level byte routes the chorus into the reverb instead of the mix, which
measured as exact silence with the reverb turned down.

Verified against the reference on a sine carrier: peak-to-peak pitch deviation
13.6 / 20.7 / 32.3 cents at depth 32 / 64 / 127 against 13.5 / 20.9 / 32.5, and
level within 0.07 dB.

Three traps, all of which cost time here:

* **The reference's effects DSP needs about 1.5 s from reset.** With the usual
  1 s warm-up the chorus appears to start 454 ms after note-on; with
  `JV_WARM=4` it starts after 20. Every effect measurement needs the longer
  warm-up.
* **Counting zero crossings is a bad period estimator.** It gave alternating
  values that read as a depth-independent constant slope, which is wrong.
  Autocorrelation with proper peak finding -- first local maximum after the
  correlation goes negative -- gives a clean answer.
* **Correlating white noise needs a lag step of 1 and a NORMALISED score.**
  Stepping the lag by 4 misses the peak entirely, and maximising the
  unnormalised correlation tracks the local energy of the dry signal instead of
  the delay. Both produced "no peak anywhere" against a chorus that was in fact
  correct.

**CHORUS2 is the same delay, deeper and faster.** It was written off earlier as
"not a plain modulated delay" because cross-correlation against the dry signal
found no peak at any lag from 0.3 to 125 ms. That was the measurement, not the
effect: at these slopes the delay moves 24 samples inside a 16 ms analysis
window, which smears the peak away entirely. A sine carrier settles it, because
it does not care how fast the delay sweeps -- only where the pitch ends up.
Measured at depth 127: 195.6 cents of peak-to-peak deviation against CHORUS1's
32.5 at every rate, and a period of 576 / 416 / 224 ms against 1120 / 768 / 448
at rate 32 / 64 / 96 -- half, to within 4 %.

Two notes on getting the engine to match it. The slope multiplier that works is
8, not the 6 the cents ratio implies, judged by energy-weighted spectral spread:
10.14 and 15.80 Hz against the reference's 9.27 and 14.79 at depth 64 and 127.
Spread is the measure to trust here -- it needs no peak tracking and reproduces
CHORUS1 to within 8 %, where the pitch tracker gave answers that changed with
the analysis window. And the delay buffer had to grow from 768 to 1280 samples:
CHORUS2 sweeps three times as far as CHORUS1, so the excursion clamp was biting
silently and costing it a third of its deviation.

And one real bug it exposed: reading the delay line at `pos - delay` truncates
toward zero when that goes negative, which yields a NEGATIVE interpolation
fraction and makes the interpolator extrapolate backwards. With the write
pointer cycling 0..767 and the delay at 578..761 it happened three quarters of
the time. Biasing the read position up by a whole buffer length fixes it.

## The reverb, and the two delays hiding in it

Same isolation as the chorus -- dry level 0, reverb send 127, chorus off -- but
with a 50 ms burst and a five second tail, so the render is essentially an
impulse response. All six reverb algorithms come out with the two channels
DECORRELATED: |L/R correlation| < 0.04 over the tail, every type.

**The two delay types are exact.** Measured, not modelled:

    delay time = 2.0 + 3.843 * time ms    (2 / 63 / 124 / 185 / 250 / 311 /
                                           372 / 433 / 490 at time 0..127)
    feedback   = fb/128 - 1/64            (per-repeat ratios 0.234 / 0.484 /
                                           0.734 / 0.984 at fb 32/64/96/127)

PAN-DLY is **two taps on one line, not one tap that alternates sides**. At
feedback 0 the reference already produces two echoes -- 62 ms left and 124 ms
right at time 32 -- so the half-period tap feeds the left channel and the
full-period tap the right, with the feedback going round the full period. That
is why the levels arrive in equal pairs. The engine now reproduces the whole
train: 64 / 126 / 188 / 250 / 316 / 378 ms alternating sides against the
reference's 62 / 124 / 184 / 246 / 306 / 368, decay ratio 0.484 against 0.485,
and peak level 0.1660 against 0.1659.

**The six reverbs are matched, not reproduced.** RT60 is measured per type at
five time settings (`JV_REVERB_TIME_MS`) and the engine runs a Schroeder
comb/allpass network sized to hit it, landing within 1 % everywhere:

| type | t=0 | t=64 | t=127 |
|---|-----|---|---|
| ROOM1 | 281 [276] | 618 [614] | 1130 [1124] |
| STAGE2 | 322 [318] | 1362 [1354] | 5460 [5420] |
| HALL1 | 527 [524] | 1203 [1196] | 3603 [3583] |
| HALL2 | 407 [404] | 1303 [1296] | 6625 [6572] |

The topology is not the chip's, and it shows in the residual: tail level is
2.4 dB out on average (3.4 dB absolute), worst on the room types at very short
decay, where the reference's level falls away faster than a Schroeder network's
does. Reverb time in the factory banks has a median of 80 and only 12 of 125
patches sit below 32, so the fit is good where it is used.

**The reverb type is bits 0-2, not the low nibble.** The manual gives the range
as 0-7 and bit 3 of patch-common +12 is something else, set on 40 of the 192
factory patches. Masking with `0x0F` handed 67 of them a type of 6 or 7 -- DELAY
or PAN-DLY -- so a third of the bank played a hard echo where it should have had
a room or a hall. It sounded exactly like that, and it survived every level and
decay measurement because those were all made by setting the type byte
explicitly to 0..5.

**The tail level is right in isolation and low on real patches.** With the level
table fitted, the isolated reverb matches the reference to 0.0 dB across every
type and time. On A04, whose piano samples decay through the note, the engine's
tail sits about 13 dB low. The reverb is linear, so this is not a gain error: a
comb bank driven by a decaying input accumulates less than the chip's network
does. Same root cause as the burst measurement being 12-41 dB quiet while a
flat-sustain note was 5.7 dB loud -- the build-up differs, and no single gain
fixes both. Open.

Two things worth carrying forward:

* **The two channels need genuinely different comb sets, not a stereo spread.**
  Nudging the right channel's combs by a dozen samples (809/823, 877/887, ...)
  left the engine at +0.85 correlation, because both sides see the same input
  and nearly the same delays. Separate sets -- 809..1049 against 1123..1381 --
  bring it to +0.01.
* **`jv_engine_test` renders whatever hold you ask for now** (`--hold`,
  `--tail`). It used to be fixed at 2 s + 2 s, and comparing that against a
  50 ms burst on the reference smeared every echo into one blob. It looked
  exactly like PAN-DLY putting both taps on both channels, which sent the
  implementation off after a bug that was not there.

## Playing material that was not written for the JV

The machine's velocity response is steep -- across 25 factory patches the median
drop from velocity 127 to 64 is 11.7 dB, and A43 Syn Strat drops 19.6. That is
faithful, and it is also awkward: a sequencer file whose velocities sit between
60 and 100 comes out thin.

The firmware therefore has a VELO page. It scales the incoming velocity toward
127 before the engine sees anything, so 100 % passes it through untouched, 50 %
halves the distance to 127 and 0 % makes every note full strength:

| setting | v=48 | v=64 | v=80 | v=100 | level at v=64 |
|---|---|---|---|---|---|
| Orig | 48 | 64 | 80 | 100 | -- |
| 75 % | 68 | 80 | 92 | 107 | +3 to +4 dB |
| 50 % | 87 | 95 | 103 | 113 | +6 to +8 dB |
| 25 % | 107 | 111 | 115 | 120 | +11 dB |
| 0 % | 127 | 127 | 127 | 127 | +15 to +17 dB |

The mapping happens before the engine, so the velocity curves, both velocity
sensitivities and the per-tone velocity windows all act on the same value.
That last one is the side effect to know about: compressing upward will also
bring in tone layers a patch reserves for hard playing.

## MIDI: what the machine receives

The manual's MIDI implementation (printed 10-32 f.) lists exactly what the
JV-880 accepts, and the firmware now covers that list rather than the handful
of controllers it started with:

| CC | what it does | note |
|----|---|---|
| 0 | bank select, MSB only | 80 user, 81 preset; latched until a program change |
| 1 | modulation | matrix source |
| 5 | portamento time | overrides the patch |
| 6 / 38 | data entry | for RPN |
| 7 | volume | on the machine's own tone-level curve |
| 10 | pan | constant power, 0 left / 64 centre / 127 right |
| 11 | expression | matrix source |
| 64 | hold-1 | |
| 65 | portamento switch | overrides the patch |
| 91 | Effect1 depth | reverb send, scales the whole bus |
| 93 | Effect3 depth | chorus send |
| 100 / 101 | RPN | 0 bend sensitivity, 1 fine tune, 2 coarse tune |
| 120 / 123 | all sound / notes off | |
| 121 | reset all controllers | returns every override to the patch |
| 124-127 | omni / mono / poly | mono forces SOLO, poly forces it off |

Program change reaches all 192 patches: bank 80 gives the 64 user patches, bank
81 splits into A for programs 0-63 and B for 64-127. Before this it could only
move within whichever bank was already selected.

The overrides are deliberately three-state -- CC5, CC65 and mono/poly hold -1
for "use the patch", so a reset-all-controllers hands the decision back rather
than freezing whatever the last CC said.

## Resonance mode and tone delay

**Resonance mode** is bit 7 of +53: clear SOFT, set HARD. 58 of the 539 active
tones set it, though 44 of those sit at resonance 9 or below where it barely
matters. Measured with white noise through the low-pass at cutoff 48, peak
against the 300-600 Hz passband: HARD sits above SOFT by 0.0 / 2.8 / 5.1 / 8.3 /
12.1 dB at resonance 0 / 30 / 60 / 90 / 127. That is what doubling the exponent
of the damping law gives -- `exp(-0.0104 * res * (R-1))` reproduces all five
points at R = 2.05.

Measuring it also showed the damping law's leading constant was 1.2 to 2.4 dB
loose, engine against reference by the same method. Re-fitting 0.893 to 1.125
brings the mean absolute error over both modes and five resonance settings from
2.4 dB to **0.44 dB**, and the brightness error over 128 factory patches from
4.95 to **4.68 dB**.

**Tone delay** (+69) is exactly linear at 16.0 ms per unit: 0 / 130 / 260 / 380
/ 510 / 770 / 1020 / 1280 / 1540 / 1790 / 2030 ms at value 0 / 8 / 16 / 24 / 32
/ 48 / 64 / 80 / 96 / 112 / 127. The engine reproduces it to within one 10 ms
analysis frame. 34 tones use it.

The mode lives in bits 3-4 of +71 and the factory banks use NORMAL on 535 tones
and PLAY-MATE on 4; HOLD does not occur at all. PLAY-MATE takes the gap between
the last two note-ons instead of the parameter, scaled so that a parameter of 64
reproduces the gap and 127 roughly doubles it. Past 127 the panel shows KEY-OFF,
which starts the tone when the key is released; one tone carries it and the
engine clamps to the longest delay rather than modelling it, since a voice that
starts on note-off has no note-off left to end it.

## Key assign and portamento

Patch common +24 holds the voice-assignment flags -- key assign SOLO in bit 7
(11 of 192 patches), portamento switch in bit 6 (6 patches), solo legato in bit
5 (16 patches), portamento mode in bit 4 -- and +25 the portamento time with its
type in the top bit.

Measured by playing a sine in SOLO and sending a second note-on an octave up one
second in, then tracking the pitch through the glide. **The glide is linear in
cents**: at time 50 it covers 193 / 251 / 248 / 254 / 230 cents in successive
50 ms windows, constant to the resolution of the tracker. Duration for one
octave:

    t = 13.6 ms * 2^(value / 12.3)

**TIME and RATE differ exactly as the names say.** At time 56 a glide of 5, 12
and 19 semitones took 300 / 300 / 290 ms in TIME mode -- the same duration
whatever the interval -- and 120 / 300 / 490 ms in RATE mode, the same 25 ms per
semitone throughout. One law serves both: the fit above is the duration of an
octave, and RATE scales it by the interval.

The engine reproduces both within 4 %: 30 / 110 / 290 / 750 / 1200 ms against
30 / 110 / 300 / 740 / 1150 at time 24 / 40 / 56 / 72 / 80, and the interval
behaviour of each mode exactly.

SOLO keeps a stack of held keys and plays the last of them, falling back to the
one before when a key is released -- which is what makes a trill under one
finger work. Solo legato retunes the sounding voices in place instead of
retriggering; the multisample zone is deliberately not re-selected, since
re-picking it would restart the sample, and not restarting is the whole point.

One harness note: `jv_engine_test` grew `--note2` and `--note2at`, because
nothing about portamento or legato is visible with a single note. The first
version placed the second note-on with `at > ctlAt`, and the obvious test value
of 1.0 s is exactly `ctlAt` -- so the note never sounded and the engine appeared
to have no portamento at all.

## Two more sources, and what they were each good for

**Roland's "JV Master Class" supplemental notes** (SN08, 1996, a Keyboard
Magazine article, 7 pages with a text layer) is a tutorial, not a
specification, but it contains two facts nothing else stated:

* **FXM "uses a square wave to modulate the selected waveform".** That one
  sentence turned FXM from unmeasurable into a targeted experiment -- knowing
  the modulator is a square wave says to go looking for evenly spaced sidebands,
  and they are there at a fixed 125 Hz.
* **Analog feel "produces irregular variations in pitch and level"**, not pitch
  alone.

It also independently confirms the matrix destination count ("level ... and 11
other parameters"), pan RND as a per-note random position, and that release
velocity drives the T4 time of all three envelopes.

**[charlesvestal/schwung-jv880](https://github.com/charlesvestal/schwung-jv880)**
wraps the same Nuked-derived emulator for the Ableton Move, so its DSP is the
reference this harness already drives. Its value is a hand-built table in
`src/dsp/jv880_plugin.cpp` giving a byte offset, bit shift and mask for 89 tone
parameters. As an independent check it confirms exactly the inferences that had
been least certain here:

* `lfo1offset` at +23 **shift 3, mask 0x07** -- the three-bit offset field
* `lfo1fadepolarity` at +23 **bit 7**
* `levelkeyfollow` at +70 **low** nibble, `tvaenvtimekeyfollow` **high**
* `panningkeyfollow` at +39 high, `randompitchdepth` low
* `tvfenvvelocitycurve` at +55 **bits 0-2**, `tvfenvvelocitylevelsense` at +56
* `tvfenvlevel4` at +66, and the pitch envelope's four levels as signed

It disagrees on three nibble assignments, and in all three the factory data or
a measurement decides against it:

| byte | that table | here | what decides it |
|---|---|---|---|
| +40 | pitch keyfollow = high nibble | low nibble | The low nibble is 12 on 507 of 539 tones, and index 12 is +100 %, the normal octave per twelve keys. The high nibble is 7 on 534 tones, which in the same table is +20 % -- nothing would play in tune. |
| +71 | TVA velocity curve = high nibble | bits 0-2 | The high nibble is 12 or 13 on every one of the 539 tones, outside the valid 0-6 range. Sweeping bits 0-2 produces a clean seven-member family of velocity responses. |
| +54 | cutoff KF and TVF-env time KF both listed as the whole byte | low / high nibble | They cannot both be the whole byte. The low nibble reaches 15, which only the 16-entry cutoff table allows, and is 0 % at its mode; the high nibble stops at 14 and is 0 % at its mode in the 15-entry table. |

Neither source changed a measured number. Both were worth reading anyway: one
supplied the missing premise for an experiment, the other independently
corroborated six inferences that had rested on argument alone.

## Fitting a 4 MB board, without touching a sample

The full instrument is 4.33 MB of flash, so it needs a 16 MB board. Most people
who would like to try it own a base Pico 2 with 4 MB. The question was whether
something could be selected away, and the honest answer had to come from the
data rather than from a guess about what "sounds unimportant".

Reachability, measured rather than assumed: a tone names a multisample, a
multisample names up to 16 samples across its zones, and a tone with bit 7 of
its flag byte clear is off. Walking that from all 192 patches reaches **538 of
577 samples** and **93 of 129 multisamples**. So 39 samples are addressed by
nothing at all — the ROM also serves the JV-880's rhythm sets, which this
instrument does not implement. Their bytes are 0.36 MB that no build needs.

That alone does not get there. The banks split as follows, after relocation and
packing:

| kept | samples | wave data | blob | firmware | free on a 4 MB board |
|---|---|---|---|---|---|
| A | 331 | 1.60 MB | 1.67 MB | 2.00 MB | 2040 KB |
| A + B | 516 | 3.29 MB | 3.43 MB | 3.76 MB | 234 KB |
| A + B + User | 538 | 3.52 MB | 3.65 MB | 3.99 MB | 7 KB |

Keeping everything and dropping only the dead bytes misses by a hair — 7 KB is
not a margin, it is a build that breaks on the next commit. Dropping the user
bank costs 64 patches and 22 samples and buys 234 KB, so that is where the line
is.

Three constraints shape the relocation, all of them consequences of how the
chip finds the exponent nibble for a byte at address `a`:

```text
nibble_byte = wave[(a & 0xF00000) | ((a & 0xFFFFF) >> 5)]
nibble      = high half if a & 0x10 else low half
```

A sample must keep its address **modulo 32**, or it reads its neighbours'
exponents. It must stay inside **one 1 MB page**, because that is what supplies
its nibbles. And the first 32 KB of every page *are* nibbles, so a page holds
992 KB of sample data, not 1 MB.

Two things were easy to get wrong here and both were caught by measurement
rather than by reasoning:

* **Samples share bodies.** The 577 samples span 4.34 MB of ranges inside a
  4 MB ROM — several differ only in loop points over the same data. Relocating
  them individually duplicates about half a megabyte, which is more than the
  whole exercise saves. Overlapping ranges have to be merged and moved as one
  block, and those blocks then cannot be split to fill a page, because the
  samples inside them are tied to each other's offsets.
* **Packing order matters more than it looks.** Filling pages in address order
  strands ~130 KB at the page ends — over half the final margin. First-fit
  decreasing gets it back.

The check is the strong one, and it is worth stating in the form it takes: the
claim is not "close enough", it is that banks A and B are **bit-identical** to
the full build. Nothing is resampled, requantised or shortened; only moved.
`tools/host_tests/jv_blob_test` renders all 128 patches out of both blobs and
compares sample by sample. It reports `0/128 patches differ`.

One engine change fell out of this. `Engine::init()` refused any wave blob
under 4 MB, and `selectPatch()` then walked off a null `rom2` — the compacted
blob crashed before it played a note. The size floor was never the right check:
every address is bounds-checked in `sampleFor()` anyway, which is also what
makes a dropped sample safe. Zeroing its table entry fails `start < loop` there,
so a tone naming it falls silent instead of playing whatever now sits at that
address.

## The reverb, and where it stops

The reverb is the one part of the engine that is matched rather than
reproduced: the type, time and level laws are measured, but the network behind
them is a Schroeder bank of my own, and its tails run about 13 dB low on
material that decays. This is what came of trying to settle it.

The effects sit inside the PCM chip, whose delay memory the reference emulator
models as `eram`, 0x4000 words -- 512 ms at 32 kHz. Every effect slot addresses
it as `eram[(base + tv_counter) & 0x3fff]`, with `tv_counter` a free-running
pointer, so logging each access and taking `(addr - tv_counter) & 0x3fff`
recovers the base the firmware programmed. That is the tap position, and it
does not have to be guessed. `jv_fx_taps.cpp` does exactly that.

The same route was the one munt took for the MT-32's reverb, where the buffer
sizes came from tracing the reverb RAM address lines of the real chip. Its
constants are of no use here -- a different chip in an older machine, four modes
against the JV's six plus two delays -- but the method carries over, and in an
emulator the address lines are function arguments.

The chips are named in the same survey that identifies the JV's, cited below:
the MT-32's reverb is a Hitachi HG61H20R36F, the JV's effect section a Toshiba
TC24SC201AF-002 dated 1990. The survey gives no year for the Hitachi part, and
the MT-32 shipped in 1987, so how far apart their designs are is not something
this repository can state -- an earlier draft claimed five years and had no
source for it.

**What came out.** One fixed delay network, shared by all six reverb types:

```
reverb        917 1295 1406 1424 1483 2149 4063 4877 5462 6772
              7217 7960 8438 9510 10097 10879 11441 12700 13128
DELAY/PAN     0 1 2 3 4 5 6 7 | 8192 8193 8194 8195
chorus        4 to 6 taps just below the wrap, 82-189 samples back
```

Three things are settled by that. The six reverb types do **not** each get their
own network -- they share one and differ only in coefficients. The time setting
moves no tap at all, so it too is a coefficient, which means the measured RT60
law is the right level of description. And a handful of taps sit in every
configuration, reverb or delay alike, a short distance behind the write pointer:
that is the chorus, which runs on the same chip. The reverb proper has 19 taps
and the delays 12.

Checked across seven patches of bank A (0, 7, 19, 31, 44, 55, 63) at three time
settings each: the reverb's 19 and the delays' 12 are **identical every time**,
so the geometry belongs to the chip and not to the patch. The chorus taps are
the exception and vary from patch to patch -- four of them for some, six for
others, anywhere from 82 to 189 samples back -- which is what a modulated delay
looks like when it is sampled at one instant. Reading a single patch would have
suggested a fixed 153-188, and that would have been wrong.

**Where it stops.** The coefficients are not reachable this way: the chip walks
32 slots in rotation and reuses `ram2[28..30]` per slot, so a register snapshot
catches one arbitrary moment of the cycle and reports identical values for every
reverb type. It looks like an answer and is not one, and the first version of
this tool was thrown away for it. The address trace above is immune to that
because it records every access rather than one instant.

Neither is the decay, and for a blunter reason: **there is no decay**. The
effect section moves signal through the delay memory -- the addressing is real,
which is why the tap trace works -- but it does not recirculate. What comes out
is a delayed copy of what went in, and it stops when the input stops.

Isolate the effect by rendering a note twice, once with the per-tone reverb send
at 127 and once at 0 (`+82` in `jv_tone_map.h`), and subtract. The difference is
exactly zero, then present, then exactly zero again. Vary how long the key is
held and the window moves with it:

```
key down  60 ms   difference present from 375 ms to  625 ms   (275 ms)
key down 500 ms   difference present from 375 ms to 1150 ms   (800 ms)
```

The onset stays at 375 ms -- the propagation time to the output taps -- while
the length follows the note. A reverb tail would outlast its input and decay;
this ends with it. Nothing changes with the reverb type or the time setting,
because there is no loop for them to act on.

**Consequences for the engine.** `jv_reverb_rt60_ms` and `jv_reverb_level` were
fitted here, and there is no reverb tail here to fit to. The note in
`Engine::Reverb` records the measurement as taken "in context on A04", with the
dry note still sounding, and describes a decay that steepens from 7 to
15.6 dB/100 ms where a comb bank falls at a constant 8.9. That shape is what a
dry release plus a delayed copy looks like when the two are measured together --
first the note dominating, then dropping away. So the ~13 dB deficit is not a
tuning error in the Schroeder bank: the curve it is tuned to does not describe a
reverb.

**This emulator cannot settle it, and the reason is in the silicon.**
[giulioz/roland-dsps](https://github.com/giulioz/roland-dsps), a survey of
Roland's custom effect chips, names the one in this machine:

> **GP** (Toshiba TC24SC201AF-002, 1990). Integrated 28-voices sample player
> with TVF and **ROM-based DSP (chorus/reverb)**. Used in: SC-55, JV-80, many
> many more.

The JV-880 is the rack JV-80, so that is the chip, and the effects are not a
wired-up network but a **program in a ROM inside it**. Of every chip in that
survey the GP is the only one with no emulator of its own; it points at
Nuked-SC55, which is where this project's reference emulator comes from.
Nuked-SC55 models the hardware -- registers, addressing, the delay memory --
but not the program running in it, because that ROM has not been read out.

Which accounts for every observation above. The addressing works, so the taps
are real and their geometry is worth having. There is no recirculation, because
the feedback lives in the program. Type and time do nothing, because they are
parameters to a program that is not running. The measurements were right; what
was missing was the reason.

So this is not "not reachable yet". Nothing done to the emulator will produce
the reverb until that ROM is dumped -- optically, as has been done for some of
the others in that survey, though not for this one. Until then the honest
position is that the reverb is matched to a curve of unknown provenance, and the
geometry above is the only measured thing about it. Recordings from hardware
would be the way round it.

Three lessons, each of which cost a wrong conclusion here. A differential
measurement is only as good as its control: patch common 13, the reverb return,
does nothing in this emulator, so toggling it gives exactly the same silence as
a missing feature -- prove the setup on a control known to work before its
silence means anything. The check meant to validate the harness, the same
measurement aimed at the chorus, used the same wrong kind of byte and so
confirmed the setup instead of testing it. And a difference that is merely
non-zero proves nothing either: seeing one through the send, this section was
briefly rewritten to say the reverb worked after all, when what had been found
was a delay line. Ask what the difference *is*, not whether there is one.

What is left, then, is not a measurement but a decision. The tap geometry above
is real and the gains are not obtainable here, so a rebuild of `Engine::Reverb`
on the measured geometry would still be guessing its gains -- against a decay
law that, as it stands, describes a dry release rather than a reverb. Better
than today, but not by as much as the geometry alone suggests, and worth doing
only alongside a decay from hardware.

Until such a recording exists, leaving the reverb as it is and saying so
plainly, as `README.md` and `Engine::Reverb` both do, beats rebuilding it around
numbers of unknown provenance.

## The velocity window, and the switch that turns it on

Each tone carries a velocity window at +03/+04. The window is real, but it is
*conditional*: it only gates while bit 7 of the patch common byte at +12 — the
patch velocity switch — is set. Miss that condition and the bytes look wrong in
both directions, which is exactly what happened here, twice.

Gating on them unconditionally silenced six bank-A basses below velocity 61.
St Fretless, House Bass, Thumpin Bass, Pick Bass, Wonder Bass and Yowza Bass
all carry +03 = 61 on every tone, so under an unconditional reading they have
nothing at all to play below that velocity, while the reference plays them.
Across bank A that was 70 of 1600 cells sounding on the reference and silent
here. So the gate came out.

Not gating at all sounds tones the machine keeps silent. A20 Marimba SW is the
audible case: its third tone is wave 78 "Anklungs", windowed to 126..127, and
playing it at every velocity lays a rattle under the marimba — about 12 Hz,
26 % of the modulation energy in the 8–16 Hz band against 1.3 % for the
reference. It is loud, too: above 1 kHz the engine carried 50–60 dB more
energy than the machine.

The switch settles it. Measured on the reference at note 60, A20 has no
high-frequency content at velocity 100 (−35.2 dB against its own fundamental)
and +25.9 dB of it at velocity 127 — the windowed layer coming in exactly where
+03 says it should. And bank A splits without a single exception: of the 27
patches carrying a window at all, the 10 whose window must be ignored have the
switch clear, and the 17 whose window must bite have it set. The second group
is precisely the velocity-layered material — the Rhodes family, SwitchOnMute,
Velo Harmnix, Slap Bass, Marimba SW.

With the condition in place, at note 60 and velocities 20/40/100/127 there is
no patch in banks A and B that the machine sounds and this engine does not.
Of the 21 patches whose window can bite, none got further from the reference
and two moved a long way toward it: SwitchOnMute 0.325 → 0.785 and Marimba SW
−0.008 → 0.444 in third-octave band similarity.

One caveat worth keeping: the manual's own wording for bit 7 is that it
*disables* velocity response, which is the opposite of what bank A shows. The
reading here is the measured one.

## The reverse samples, and the roar they were making

Bit 2 of the sample record's flag byte at +11 makes the chip walk the address
DOWN instead of up. Fifteen samples set it -- 562 to 576 -- and they are exactly
the fifteen belonging to the fourteen multisamples named `REV ...`: REV Steel DR,
REV Tin Wave, REV SN 1..4, REV Kick 1, REV Cup, REV Tom, REV Cow Bell, REV TAMB,
REV Conga, REV Maracas, REV Crash 1.

Two waves settle what the bit does between them. Wave 96 `Crash 1` names sample
543 at 163489..227837; wave 128 `REV Crash 1` names sample 576 at
163488..227837. **The same ROM region**, one byte apart, same end address. The
records differ in the flag alone: 0x01 against 0x05. And the stored audio decays
like any cymbal -- decoded, it runs from -2 dB at 0.2 s to -19 dB at 1.8 s -- so
nothing but reading it backwards can produce the swell the machine plays. The
emulator's own address counter has the matching control bit: `if (b7)
address_cnt2 -= ...; else += ...`, from `ram2[7] & 0x80`.

Reading the flag costs one line; not reading it cost rather more than a missing
swell. B63 RevCymBend puts all four of its tones on wave 128, and playing that
sample forward runs off the end of the body into its alternating loop, where the
differential integrator does not come back to where it started. Rendered for
fifteen seconds against the reference, the machine falls to digital silence at
second 3 and this engine went on roaring at -35 to -47 dBFS through second 13 --
a ten-second noise burst on every note of the patch. Played backwards the body
is traversed once and the voice ends at `start`, which is the forward attack,
and the reference does the same: both go silent at second 3.

Third-octave band similarity over six seconds: 0.539 -> 0.867. The four affected
patches are B63 RevCymBend and User64 REVERSE MAD, which use the REV waves, and
B13 Orch Stab 1 and User11 Orch Stab 2, which use the forward Crash 1 and are
unchanged to the sample -- the runaway needed the reverse record's loop, not the
alternating bit as such.

**What is still wrong.** The swell is now the right shape and ends at the right
moment, but its level is not right in the middle: at the peak this engine sits
6.5 dB under the reference and around 0.9 s it is 27 dB under, while the two
ends agree to about 5 dB. The sample side is exonerated -- decoded backwards it
carries no DC (mean 7 of a 3865 RMS), never touches the clamp, and mirrors the
forward envelope exactly (18.4 dB of swell). Windowed band similarity stays
between 0.71 and 0.93 throughout, so the content is right and only its amplitude
over time is not. The patch bends: coarse -8, pitch envelope depth 12 with a
full negative deflection over T2, which changes how fast the reversed body is
traversed and so where its swell lands. That makes the pitch envelope the first
thing to check, and it is not checked yet -- so this is a lead, not a finding.

## The pitch envelope, and a lead that did not survive

B63 RevCymBend was left with a residual: the right swell, ending at the right
moment, but 6.5 dB under the reference at its peak and 27 dB under in the
middle. The patch bends -- coarse -8, depth 12, a full negative deflection over
T2 -- so the pitch envelope was named as the first thing to check, on the
reasoning that a wrong pitch traverses a reversed sample at the wrong speed.
It was checked. It is not the cause.

**The sweep.** Every one of the 84 tone bytes was written into the reference's
temporary patch area at 0 and 127, on a synthetic single-tone patch held
forever, with a pitch envelope armed at maximum depth and a T2 long enough to
glide audibly within the measured second. Four bytes move the sounding pitch:
+37 and +38, the two tunings; +39, whose low nibble is the random pitch and at
15 draws over +-1200 cents; and +01, which is simply a different wave. Nothing
in +40..+51 moves it at all. The harness is sound -- +67 sweeps the level
cleanly from silence to 0.086 RMS across the same range, and +37 tracks the
keyboard in exact semitones (value 8 gives +8, 16 gives +16, 24 gives +24).

A factory patch says the same. B23 GlassVoices gives its third tone depth 250
with a 400 ms segment, and the reference holds a flat 262.5 Hz through the
note -- as does this engine.

**Why it is not acted on.** One measurement pulls the other way. This engine's
pitch envelope puts an octave on B63 at note-on and glides it down, and with
that in place the note ends at 2.8 s, which is exactly when the reference ends;
switched off, the ending moves out to 3.6 s and third-octave band similarity
falls from 0.867 to 0.841. Coarse -8 alone predicts 3.19 s, so the machine is
running that note about two semitones sharp of what the tuning bytes account
for, and where that comes from is unknown. Deleting the block on the strength
of the sweep would trade a modelled sweep for a wrong duration.

**Stakes.** 68 of 539 tones set a depth and 66 of those move their levels, but
only 13 have a segment slow enough to hear as a sweep rather than a blip of a
few milliseconds -- and four of the thirteen are the four tones of B63. The
others are User29 Glasswaves, User49 UTAKATA, User56 Glass Pad, User62 Arctic
Winds, User63 DistanceCall, B23 GlassVoices and B59 JP-8 Pad. Switching the
envelope off changed none of them by more than 0.02 in similarity.

So: the residual on B63 is still unexplained, and the pitch envelope is no
longer a candidate.

## The pitch offset: five cents, and a retraction

The pitch-envelope note above ended by saying the machine "runs that note about
two semitones sharp of what the tuning bytes account for". **That is withdrawn.**
It was inferred from how long B63 RevCymBend takes to traverse its reversed
sample, which depends on when the note ends as much as on how fast it is played,
and it does not survive a direct measurement of the pitch.

Measured properly, both engines are given the SAME synthetic patch -- one tone,
one wave, held at full level with every modulator neutral and both tunings at
zero -- ours through `setPatch`, the reference by writing it into its temporary
patch area at `nvram[0x0d70]` and resetting. The sounding pitch is then read off
a zero-padded spectrum, searched only within a couple of semitones of the
expected fundamental so the measurement cannot jump an octave, which is what
made an earlier autocorrelation pass produce nonsense.

| note | expected | reference | this engine |
|---|---|---|---|
| 48 | 130.81 | -6.0 ct | -1.3 ct |
| 55 | 196.00 | -5.7 ct | -0.9 ct |
| 60 | 261.63 | -6.0 ct | +1.1 ct |
| 67 | 392.00 | -4.9 ct | +0.7 ct |
| 72 | 523.25 | -5.4 ct | -0.1 ct |

**This engine plays equal temperament to about a cent. The reference plays about
five cents flat of it**, and the median difference is +5.0 cents with this
engine on the sharp side. It is a constant frequency ratio, not a per-note or
per-wave effect: waves 0, 12, 30 and 60 give +4.7, +5.3, +3.9 and +5.9 cents
(wave 96 is a cymbal and measures nothing meaningful). It is not the pitch
envelope -- that block moves no pitch at all, see above -- and it is not the
reference's audio path, which runs natively at 64 kHz and divides by exactly two.

**Where it comes from is not established.** The most likely reading is that it
is the dumped unit's own stored master tune: the reference boots from
`jv880_nvram.bin`, a 32 KB image of one real machine's battery-backed RAM with
that machine's system settings in it. Sweeping the plausible bytes at the head
of that image did not isolate it -- a 16-bit word at `nvram[1..2]` looked like a
candidate at 1012 against a neutral 1024 and turned out to change nothing across
976..1072 -- so this is a reading, not a finding.

**Nothing is changed on the strength of it.** Tuning this engine five cents flat
would match one dumped unit's saved setting rather than the instrument, and the
nominal figure -- A = 440, equal temperament -- is what this engine already
produces. Anyone who wants to sit with that unit can dial it: the TUNE page
offers +-50 cents in one-cent steps.

Worth knowing for every A/B measurement in this file: they all carry this five
cents. Third-octave band similarity is insensitive to it, so none of the
conclusions drawn from those numbers turn on it.

## The fall to silence was 40 dB and should be 32.6

A57 Slap Bass sat 1.8 dB over the reference and would not come closer. Tracked
across the keyboard, the error turned out not to be a level at all: the attack
matched to within a decibel at every note, and everything after it drifted. At
note 40 -- the root of the zone, so no pitch shift at all -- the two agreed at
the transient and were 2.5 dB apart by 1.3 s. That is a decay rate.

The samples in that patch loop, so once the body has run out the level is
whatever the envelope says, and the envelope is all this patch has: T1 = 0 to
full, then T2 = 82 down to zero. Measured there, the reference decays at
-11.3 dB/s and this engine at -13.8.

Put on a synthetic patch -- one tone, one looping wave, held at full level with
every modulator neutral -- and timed by a 12 dB drop taken after the body runs
out, the error is a clean constant. Across stage-2 times 70 to 110 the engine
reached that point in **0.81 to 0.85** of the reference's time, and its release
in 0.74 to 0.79. Both stages fall to silence, and both ride on the same figure:
the engine spent one fall time travelling 40 dB.

The shape was never wrong. Both sides are dB-linear -- at stage-2 time 90 the
reference measures -6.6 dB/s early and -7.1 dB/s late, this engine a flat -8.2 --
so only the depth needed moving. Sweeping it crosses unity between 32 and 34
(34 gives 0.96, 32 gives 1.02), and **32.6** lands the decay at 0.99..1.03 and
the release at 0.95..0.97 across the whole range. The remaining release gap is
the 0.1 s the measurement window starts after note-off.

The rise side is untouched and stays exact: at stage-1 time 70 the engine tracks
the reference within 1 % at every point of a 2.4 s ramp, and reaches 90 % at
2.0 s against 2.1 s.

On A57 the mean envelope error over the first 1.4 s falls from 1.37 dB to
**0.52 dB** at note 40, from 3.87 to 2.22 dB at note 48 and from 5.28 to 3.61 dB
at note 43. Bank-wide at note 60 the change is a wash on third-octave band
similarity (median 0.911 to 0.910) -- that measure is level-blind and most
patches carry larger errors elsewhere -- while the mean absolute level error
moves 4.01 to 3.97 dB.

**Still wrong on A57:** notes 43 and 48 keep 2 to 4 dB after the fix, and both
sit in zone 1 of the multisample (sample 160) while note 40 sits in zone 0 and
is now exact. Whatever is left is zone-related, not envelope-related.
## Why a reverse sample starts at `end`, and what still ends B63 early

B63 RevCymBend's reference render falls away at about 2.7 s. Walking the whole
body backwards at that patch's coarse -8 takes 3.19 s, and walking only
`loop`..`start` takes 2.83 s -- so starting the reverse at the loop point rather
than at `end` looked like the answer, and on two metrics it looked like a good
one: the RMS ratio against the reference went from 0.37 to 1.11 and the
per-window level error collapsed from -20..-26 dB to within a few dB.

It is wrong, and the way it is wrong is worth keeping.

The decoder is a differential integrator started at zero. Output from a
backward walk beginning at address A is therefore `v(A) - v(n)`, so it carries a
DC offset of exactly `v(A)`. For this sample `v(end)` is **0** -- not
approximately, exactly -- while `v(loop)` is 1584 against a sample RMS of 3865.
Starting at the loop point injects that as DC, and it shows: measured at the
output, the reference carries 8-11 % DC against its own RMS and the loop-start
build carries **88-99 %**. Most of the apparent level improvement was not signal.

So `end` is the only start point that decodes without a DC step, and the ROM is
authored for it -- the sample's deltas sum to precisely zero over the body,
which is not an accident. The engine keeps `end`.

What ends the reference early is still unknown. It is not the tuning: pitch
measures correct to a few cents. It is not the pitch envelope, which moves no
pitch at all. A centroid fingerprint of the sample was tried as a way to read
the playback position straight out of the reference and does not discriminate --
the crash's brightness barely changes across its length (5600 Hz to 5273 Hz), so
position cannot be recovered that way. The field is narrower than it was, and
the answer is not here yet.

## A57 Slap Bass: what is left is one multisample zone, and it is not any of these

After the fall-to-silence calibration above, A57 is exact where its note sits on
a zone root and wrong where it does not. Swept across the keyboard against the
reference, the level ratio steps at the zone boundaries and nowhere else:

| notes | zone | sample | ratio |
|---|---|---|---|
| 38..42 | 0 | 159 | 0.90 .. 1.15 |
| 43..49 | 1 | 160 | 0.69 .. 0.78 |
| 50..51 | 2 | 161 | 0.91 .. 1.00 |

So the zone *selection* is right -- the step lands exactly at 42/43 and 49/50,
which is where the split points say it should. Zone 1 is simply rendered about
3 dB quiet, and not as a gain: the transient matches within half a decibel and
the deficit appears within 75 ms, long before the loop is reached at 0.63 s.

Spectrally the two engines play the same sample at the same pitch -- the peaks
line up at 58.3, 87.8 and 116.7 Hz to a tenth of a hertz -- but the balance is
redistributed. The reference peaks at 116.7 Hz with everything above 145 Hz
sitting 22 to 26 dB down; this engine peaks at 58.3 Hz, puts 116.7 at -8.3, and
carries 800..1700 Hz content that the reference has 25 dB below its peak. In
octave bands over the first 300 ms: -8.7 dB at 100..200 Hz, -9.8 at 200..400,
+3.7 at 800..1600 and +9.3 at 1600..3200.

**Ruled out, each by measurement:**

* *Zone selection* -- boundaries verified as above.
* *The sample's level byte* -- +17 is 127 on every zone of both waves.
* *The exponent decoder* -- the shift is `(10 - nib) & 15`, which wraps for
  nibbles above 10, but a sweep of the whole ROM finds none: the distribution
  runs 0..10 and stops.
* *The filter* -- probed directly on the reference and genuinely off. Sweeping
  +55 with a low cutoff leaves the output identical at every cutoff when
  bits 3-4 are 0, while 8 closes the sound down to 0.2 % of its RMS at cutoff 0
  and 16 cuts it progressively as the cutoff rises. So 0 = OFF, 8 = LPF,
  16 = HPF is now measured rather than inferred, and A57's +55 = 0 means what
  it says. A57's resonance byte of 128, which is out of the normal range and
  looked like it might enable something, changes nothing either.
* *Loop imbalance* -- the integrator drifts 5.3 % of RMS over zone 0's loop and
  5.9 % over zone 1's, so the two are alike and neither is special.

What remains is that this engine renders sample 160 with too little fundamental
and too much midrange, at the right pitch, with the filter off on both sides.
That is where it stands.

## The sample path: the chip interpolates with a cubic B-spline

Chasing A57 Slap Bass into the sample path turned up the largest single
correction measured here, and it is not what A57 needed.

The reference's PCM core reads **four** consecutive DPCM bytes per output sample,
not two, and it does not join them with a straight line. It carries a
three-entry weight table indexed by the fractional position and applies those
weights to the deltas, adding them to the running reference. Turned back into a
kernel over the decoded samples, the weights at fractional position zero are

    0.174   0.653   0.173   0.000

where a linear interpolator would use 0, 1, 0, 0. The chip is smoothing even
where there is no fraction to interpolate.

Those numbers are a **cubic B-spline**. Fitted across all 128 steps of the
reference's table the largest coefficient error is 0.014 and the mean is 0.008,
so the formula

    a = (1-t)^3 / 6
    b = (3t^3 - 6t^2 + 4) / 6
    c = (-3t^3 + 3t^2 + 3t + 1) / 6
    d = t^3 / 6

stands in for the table exactly, and nothing has to be lifted out of the
reference's source.

The difference is a filter, and that is why it was audible. At fractional
position zero the spline runs -2.3 dB at 6.4 kHz, -5.0 at 9.6 and -9.5 at
16 kHz where linear interpolation is flat. This engine was missing that lowpass
entirely, which showed up as imaging near Nyquist: on A57 at note 40, where the
zone root makes the rate exactly 1.0 and the phase never moves, the octave from
12.8 kHz was **29.3 dB** above the reference. With the spline it is -1.3.

Bank-wide at note 60 and velocity 100, against the reference:

| | third-octave similarity | patches below 0.90 |
|---|---|---|
| linear | median 0.910 | 57 |
| **cubic B-spline** | **median 0.929** | **46** |

87 patches improve, 16 lose more than 0.005. The largest gains are B48 Air Lead
0.824 to 0.977, B47 OverblownPan 0.646 to 0.852, A28 and A29 E.Organ 1 and 2
about +0.12 each, and A61 Yowza Bass 0.823 to 0.922. The largest loss is A84
Beauty Vox 0.972 to 0.948. Levels barely move -- the spline has unity gain at DC
and only takes off top end -- so this is a change of spectral shape, not of
loudness.

The table is built at init with 128 steps, the chip's own resolution, so the
cost per sample is four multiply-adds and an index.

**It is not what A57 needed.** Zone 1 there keeps its 3 dB and its missing
fundamental: -9.8 dB at 200..400 Hz before the change and -9.8 after. The
interpolator was a real fault sitting on top of it.

## The TVF: the chip's filter is a naive SVF, and swapping topology is not enough

`pcm.cpp` spells the filter out. Reading its registers:

    lp_new = lp + f * bp
    hp     = in - lp_new - q * bp
    bp_new = bp + f * hp
    out    = (ram2[6] & 2) ? hp : lp_new

That is a Chamberlin state-variable filter -- the naive one, with a sample of
delay in the loop -- and the mode bit picks the low-pass state or the high-pass
term. The coefficient is two fields of `ram2[11]`, `f = (filter>>8)/64 +
((filter>>1)&127)/8192`, so it spans 0..2 the way `2 sin(pi fc / fs)` does; the
damping is `q = ((ram2[6]>>8)&127)/64`, spanning 0..2. `ram2[11]` is written by
the same envelope generator that makes the volume, so the TVF envelope moves the
*coefficient*, not a frequency.

This engine carries a zero-delay (TPT) filter instead, with `g = tan(pi fc/fs)`.
The two are the same family and agree at low corners, but a zero-delay filter
holds its Q constant as the corner moves while the naive one sharpens. **The
reference sharpens with it**, and the gap is measurable: white noise through the
low-pass, resonant peak taken over the low passband,

| resonance | cutoff 40 | cutoff 60 | cutoff 80 |
|---|---|---|---|
| 60  | -0.6 dB | -2.7 dB | -3.1 dB |
| 100 | -1.0 dB | -3.8 dB | -4.7 dB |
| 127 | -1.2 dB | -3.9 dB | -4.8 dB |

(this engine minus the reference). At cutoff 40 it agrees, and above that it
falls behind -- the shape of a Q that should be climbing and is not. It also
explains why the damping law in `jv_calibration.h`, fitted at a single cutoff of
48, held only near there.

**Swapping the topology was tried and does not work on its own.** Rebuilt as the
naive form with `f = 2 sin(pi fc/fs)`, the isolated peak error halves -- mean
2.22 dB to 1.37, and cutoff 80 goes from -4.8 to -0.9 -- but the bank gets worse,
because the naive form runs away where the zero-delay one cannot and the
coefficients feeding it were fitted for a filter that could not. Holding the
corner under the stability line `f < 2 - q` caps every low-resonance tone at
about 4.5 kHz and darkens the bright half of the bank: median third-octave
similarity 0.929 to 0.919, 46 patches below 0.90 becoming 53. Clamping the
states instead, the way the chip clips at twenty bits, lets the corner stay open
and lets the filter self-oscillate: median 0.929 to **0.671**, with Alto Sax,
Sax Section, Flute mod and both Jazz Organs going to *negative* correlation.

So the topology is right but it cannot be dropped in. What it needs is the
mapping the firmware actually uses -- `f` and `q` as the firmware computes them
from cutoff, resonance and the TVF envelope, read out of the reference the way
the velocity curves were -- rather than this engine's Hz-and-damping fit carried
across. That is the next step, and it is a bigger one than a topology swap.

## The filter registers, read out

The TVF note above ends by saying the topology cannot be swapped in without the
mapping the firmware actually uses. That mapping has now been read, the same way
the velocity curves were: a copy of the reference with a line added after its
three `calc_tv` calls, logging `ram2[5]`, `ram2[6]` and `ram2[11]` for the
sounding slot while a synthetic single-tone patch plays.

**The coefficient, against the cutoff byte** (resonance 0, `f = ram2[11]/16384`):

| cutoff | 0 | 8 | 16 | 24 | 32 | 40 | 48 | 56 | 64 | 72 | 80 | 88+ |
|---|---|---|---|---|---|---|---|---|---|---|---|---|
| f | 0.008 | 0.070 | 0.133 | 0.195 | 0.258 | 0.328 | 0.406 | 0.508 | 0.617 | 0.750 | 0.891 | 1.000 |

`ram2[11]` climbs by exactly 128 per cutoff unit to about cutoff 32 -- it is
`128 * (cutoff + 1)` there, hit exactly at 8, 16, 24 and 32 -- then accelerates,
and **saturates at 16384 from cutoff 88 upward**. Beyond that the byte does
nothing.

**The damping, against the resonance byte** (`q = (ram2[6] >> 8)/64`):

| resonance | 0 | 4 | 8 | 12 | 16 | 24 | 32 | 40 | 48 | 56 | 64 | 72 | 80 | 88 | 96 | 104 | 112 | 120 | 127 |
|---|---|---|---|---|---|---|---|---|---|---|---|---|---|---|---|---|---|---|---|
| `ram2[6]>>8` | 64 | 61 | 58 | 56 | 53 | 49 | 45 | 41 | 38 | 34 | 32 | 29 | 26 | 24 | 22 | 20 | 19 | 17 | 16 |

A clean halving every 63.5 units: `floor(64 * 2^(-res/63.5))` reproduces 18 of
those 19 exactly (resonance 112 comes out 18 against the chip's 19). It is
independent of the cutoff at every resonance except **0**, where the register
also slides from 74 at cutoff 0 down to 64 at cutoff 64 and is flat above.

**What that says about this engine's damping law.** `JV_TVF_DAMPING`, fitted
through audio at a single cutoff, runs 15 to 21 % high: 0.806 against the chip's
0.703 at resonance 32, 0.578 against 0.500 at 64, 0.415 against 0.344 at 96,
0.300 against 0.250 at 127. Too much damping is too little resonance, which is
the direction of the peak deficit measured above.

**And why it was not simply substituted.** Putting the chip's q into this
engine's zero-delay filter is a wash -- median third-octave similarity 0.929 to
0.928, no patch better and seven marginally worse -- because q is a parameter of
the chip's topology, not a property of the sound. Substituting one model's
constant into another model is mixing, not correcting. The tables are recorded
here as the input for doing both together.

**One reading that did NOT hold up.** `f` saturating at 1.0 would put the corner
at `fs/6` = 5.3 kHz if `f = 2 sin(pi fc/fs)` with the filter running at the
output rate. Measured, the reference's -6 dB corner at cutoff 100 is 13.0 kHz,
not 5.3, so it does not run at the output rate and that identity is wrong. Taken
as a straight comparison instead, the corners agree tolerably: reference 1289,
2609, 4898, 10758, 13008 Hz at cutoffs 20, 40, 60, 80, 100 against this engine's
1461, 2586, 4609, 8992, 10797 -- within 17 %. The corner is not what is wrong
with this filter; the resonance is.

## Building the filter stage completely: four attempts, and what blocks it

With `f` and `q` read out of the chip's registers, the filter stage was rebuilt
from them. It does not work yet, and the reason is now precise enough to be
worth writing down.

**What was built.** The chip's topology -- naive state-variable, `lp += f*bp;
hp = in - lp - q*bp; bp += f*hp` -- fed by the measured `f` table indexed
straight off the cutoff parameter (envelope and modulation already in it) and
the measured `q = floor(64 * 2^(-res/63.5))/64`, with the resonance-0 cutoff
slide included. No instability: the chip's `f` saturates at 1.0, so `f + q`
touches 2.0 only at the single corner of resonance 0 with the cutoff wide open,
and never crosses. That was what killed the earlier attempt, which had carried
the old `f = 2 sin(pi fc/fs)` up to 1.98.

**Measured against the reference**, transfer function taken as filtered over
unfiltered so the source's own spectrum divides out:

| cutoff | reference -3 dB | this build |
|---|---|---|
| 20 | 1016 Hz | **1008 Hz** |
| 40 | 2156 Hz | 1492 Hz |
| 60 | 4227 Hz | 2258 Hz |
| 80 | 9984 Hz | 3812 Hz |
| 100 | open past 14 kHz | 2773 Hz |

At low coefficients it is **exact**. At high ones the reference is far more open
than the coefficient can put it: `f = 1.0` in a naive filter running at the
output rate is a corner at `fs/6` = 5.3 kHz, and the reference at that setting
is flat to 14 kHz. Fitted the other way, the implied update rate is about 32 kHz
at cutoff 20 and about 54 kHz at cutoff 80 -- so it is not a fixed-rate naive
filter at the output rate at all.

**Four variants, none better than what is in the engine:**

| | median | below 0.90 |
|---|---|---|
| current: zero-delay filter, fitted Hz law | **0.929** | **46** |
| naive, old coefficient, corner capped for stability | 0.919 | 53 |
| naive, old coefficient, states clamped | 0.671 | 101 |
| naive, measured f and q | 0.930 | 49 |
| naive, measured f and q, saturation treated as open | 0.930 | 48 |

The measured-coefficient builds are a wash: real winners -- RevCymBend 0.807 to
0.858, Log Drum 0.737 to 0.788, Space Ahh 0.808 to 0.849, Rubber Bs 1 0.909 to
0.944 -- against real losers, and the losers are the bright patches, because the
corner sits too low wherever the cutoff is high. Treating saturation as open
recovers some of those and costs others outright (EP+Exp Pad 0.824 to 0.607,
Harp 0.895 to 0.786). Shipping any of them would trade one audible error for
another.

**So the engine keeps its zero-delay filter**, which places the corner correctly
across the range -- within 17 % of the reference at every cutoff from 20 to 100
-- and gets the resonance wrong, rather than the reverse.

**The single blocker, stated precisely.** The chip's filter coefficient does not
map to a corner the way a naive filter at the output rate would. At `f` = 0.16 it
matches to eight hertz; at `f` = 0.89 the reference is 2.6 times more open than
the coefficient allows. Either that filter runs faster than the output rate --
oversampling this engine by four was tried and needs a stability rule the naive
form does not have at those coefficients -- or there is structure in the chip's
filter stage not yet found in `pcm.cpp`. That is the question to answer before
this is worth another attempt.

## The filter stage, finished -- and the harness fault that hid it

The note above named a blocker: the chip's coefficient seemed not to map to a
corner the way a naive filter at the output rate would. **It does. The blocker
was the measuring harness.**

Two measurements settled it. First, the filter's update rate, counted rather
than inferred: instrumented, the reference runs its filter **31938 times in
32000 output samples** -- once per sample, exactly. So it is not running faster.

Second, the filter measured as a black box. Logging its own input and output
sample by sample and taking the transfer function from those two signals, with
no assumption about what the coefficient means, the chip agrees with

    lp += f * bp;   hp = in - lp - q * bp;   bp += f * hp

at `f = ram2[11]/16384` and `q = (ram2[6]>>8)/64` **to 0.0 dB at every frequency**,
at cutoff 20 and cutoff 80 alike. The model was right all along; at cutoff 80 its
-3 dB point is 10156 Hz against the reference's 9984, not the 4.7 kHz that
`f = 2 sin(pi fc/fs)` would have put it at. That identity is simply not how the
naive filter's corner behaves at large coefficients.

**What was wrong** was the engine-side harness: it reused one `jv::Engine` across
the whole cutoff sweep, so the voice from the previous cutoff was still sounding
into the next one's spectrum and darkening it, while the reference side got a
fresh instance every time. Caught by a diagnostic that printed the cutoff
parameter and saw it alternating between 20 and 40 within one run.

With a fresh engine per point, the rebuilt stage tracks:

| cutoff | reference -3 dB | rebuilt |
|---|---|---|
| 20 | 1016 Hz | 1000 Hz |
| 40 | 2156 Hz | 2109 Hz |
| 60 | 4227 Hz | 3930 Hz |
| 80 | 9984 Hz | 10805 Hz |
| 100 | open past 14 kHz | open past 14 kHz |

Two to eight per cent, against the old filter's seventeen -- and with the
resonance now behaving, where the old one ran 2.7 to 4.8 dB short at cutoffs 60
and 80.

**Bank-wide it is a wash**, and that is the honest headline: median third-octave
similarity 0.929 to 0.930, patches below 0.90 46 to 49, 42 better and 24 worse.
Winners RevCymBend 0.807 to 0.858, Log Drum 0.737 to 0.788, Space Ahh 0.808 to
0.849, Nylon+Steel 0.754 to 0.790, Thumpin Bass 0.836 to 0.869, Rubber Bs 1
0.909 to 0.941; losers Soft Lead 0.843 to 0.789, Pop Piano 3 0.910 to 0.863,
NightShade 0.935 to 0.890, Ocarina 0.933 to 0.901. No NaN and no runaway at
velocity 20, 40 or 127.

The losers are all bright patches, and since the *static* cutoff now matches
across the range, what is left points at the envelope's path into the cutoff --
`JV_TVF_ENV_DEPTH_PER_UNIT`, fitted against the old filter and not yet re-fitted
against this one. That is the next thing to look at, and it is bounded.

## The TVF envelope's pull on the cutoff, measured -- and a contradiction

With the filter stage now matching, the remaining error pointed at the envelope's
path into the cutoff. That path was measured the same way as `f` and `q`, off the
chip's register, and the measurement is clean. Putting it into the engine makes
things worse, and that contradiction is the result.

**What the chip does.** Sweeping the depth byte at a fixed envelope level, and
the level at a fixed depth, gives the *same sequence of coefficients* -- depth 32
at level 32 lands exactly where depth 16 at level 64 does, point for point. So
what matters is the product, with the level taken **linearly**, not through a
curve. And the pull is superlinear in that product: for
`P = depth * level / 127` of 1, 2, 4, 6, 8, 12 and 16 the cutoff shifts by 1, 4,
8, 14, 20, 33 and 47.5 parameter units, which `1.50 * P^1.248` reproduces across
the whole range.

Two things the engine already had right: depth bytes 64..127 are inert, and
negative depths mirror the pull downward (depth -16 at full level moves cutoff 60
down to about 16, and further negatives floor the coefficient).

A third thing falls out: `JV_TVF_ENV_LEVEL`, measured separately through audio,
is within a few hundredths of `(level/127)^1.248` -- the same exponent. So the
level curve already carries its share, and the exponent belongs on the depth
alone: `pull = 1.50 * depth^1.248 * tvf.level`. That reproduces the chip at full
level exactly (47.4 against 47) and at half level closely (21.8 against 20.4).

**And it makes the bank worse.** Median third-octave similarity 0.930 to 0.927,
one patch better and 46 worse -- Stiky Rhodes 0.707 to 0.670, French Horn 0.628
to 0.584, Clav 1 0.815 to 0.742. The law pulls harder than the old
`2.4 * depth * level` did (276 parameter units against 151 at depth 63), and
harder is worse.

The contradiction is sharper than that. A version with a units bug, which made
the pull *almost vanish* (0.62 units where the chip gives 276), scored the best
of all three: median 0.934, 44 patches below 0.90 against 49, with French Horn
0.628 to **0.955**, TeaJay Brass 0.613 to 0.910, Stiky Rhodes 0.707 to 0.961 and
Dig Rhodes 2 0.700 to 0.914 -- while wrecking others outright, Vibrobell 0.926 to
-0.046 and Beauty Vox 0.974 to 0.509.

So a set of patches sounds closest to the reference with *almost no* TVF envelope
at all, another set needs a strong one, and the measured law sits between and
suits neither. That is not a calibration problem. Something else on this path is
wrong -- the envelope's timing or its shape rather than its depth is the obvious
suspect, since the depth is now measured and the level curve independently
confirmed. The engine keeps the old constant until that is found.

## The TVF envelope multiplies, it does not add

The note above ended on a contradiction: one set of patches wanted almost no TVF
envelope, another a strong one, and the measured depth law suited neither. The
contradiction was in the model, not the measurement.

**The envelope multiplies the chip's filter coefficient.** Sweeping the depth at
cutoff base 0 instead of 20 gave it away: depth 16 at full level moves the cutoff
47 parameter units at base 20 and only 3 units at base 0 -- but in the
coefficient it is the same factor both times, 4.05 and 4.00. An additive model
cannot do that.

Taken as a factor, the law is clean:

| P = depth * level/127 | 1 | 2 | 4 | 6 | 8 | 12 | 16 |
|---|---|---|---|---|---|---|---|
| measured log2(factor) | 0.067 | 0.251 | 0.466 | 0.736 | 1.000 | 1.514 | 2.034 |
| P/8 | 0.125 | 0.250 | 0.500 | 0.750 | 1.000 | 1.500 | 2.000 |

So `f = f_base * 2^(depth * level / (127 * 8))` -- an octave of coefficient per
eight units of the product, the level entering linearly.

That also explains `JV_TVF_ENV_LEVEL`. Measured through audio it looked like a
convex curve, within a few hundredths of `(level/127)^1.248`; it was this
exponential seen through an additive model. Off the register the level is plainly
linear, and the curve is gone.

**Bank-wide** at note 60 and velocity 100, against the state before any of the
filter work: median third-octave similarity **0.929 to 0.935**, patches below 0.90
**46 to 42**, 53 better and 26 worse. Against the filter stage alone: 0.930 to
0.935, 49 below 0.90 to 42, 35 better and 18 worse.

The brass moves as a family -- TeaJay Brass 0.613 to 0.871, Trumpet 0.781 to
0.918, Trombone 0.805 to 0.928, Harmon Mute2 0.783 to 0.906, French Horn 0.628 to
0.806 -- and so do the Rhodes: Stiky Rhodes 0.707 to 0.939, Dig Rhodes 2 0.700 to
0.903. B47 OverblownPan reaches 0.988. The worst loss is Big n Beefy 0.892 to
0.755; the rest give up three or four hundredths at most. No NaN, nothing driven
past full scale and nothing silenced at velocity 20, 40 or 127.

## The level offset: the chip's gain path is flat across the keyboard

The long-standing ~2.4 dB level offset is a tilt across the keyboard, and the
exclusion list for it is long. One more item can be struck off, this time by
reading the registers rather than measuring the sound.

The chip applies its volume in **two** stages, with the same two-field
coefficient structure as the filter: `ram2[9]` and `ram2[10]`, driven by
`calc_tv` from targets `ram2[3]` and `ram2[4]`, each contributing a gain of
`volmul/16384`. Read out for a fixed tone across the keyboard:

| note | 36 | 48 | 60 | 72 | 84 | 96 |
|---|---|---|---|---|---|---|
| total gain | 11.55 dB | 11.55 | 11.55 | 11.55 | 11.55 | 11.55 |

**Flat, to the last digit.** So whatever tilts the level with the key, it is not
the chip's gain path.

Measured again on the current engine, over eight tonal bank-A patches, the tilt
is now **-2.72 dB at note 36, -2.82 at 48, -0.86 at 60, -0.75 at 72 and +1.97 at
84** -- a 4.7 dB span, wider than the 1.5 dB recorded in August, so the
interpolator and filter work has moved it. It has not moved it the way either of
those would on its own: the B-spline attenuates more at higher playback rates and
would tilt the other way.

**A warning about the probe used above.** The synthetic single-tone patch that
served for pitch, filter and envelope work is NOT usable for level questions at
low notes. Written into the reference's temporary area it produces **no sound at
all** below about note 48 -- for white noise, Ac Piano 1, Alto Sax 1 and Mute GTR
1 alike -- while this engine sounds normally. Neutralising the pitch and TVA
keyfollows at +40 and +70 changes nothing. It is not the machine: unmodified
factory patches play perfectly at note 24 on the reference (A01 at 0.043 RMS,
A52 at 0.046, B13 at 0.022). Some byte the synthetic patch forces is responsible
and it has not been found, so any low-note measurement made with that patch
should be discarded.

## The probe repaired: +39's pan keyfollow is neutral at 7, not 0

The warning in the note above -- that the synthetic single-tone patch produces no
sound on the reference below about note 48 -- has a cause, and it was mine.

Bisecting the patch's overrides one group at a time against an unmodified A01
found it at once. The tone byte `+39` packs the pan keyfollow in its HIGH nibble
and the random pitch in its low one, and the pan keyfollow is a fifteen-step
field running -100 % to +100 % about C4. **Its neutral is step 7. Setting the
byte to zero asks for -100 %**, which walks a tone three octaves below C4 hard to
one side -- and the probe measures the left channel only. Setting `T[39] = 0x70`
instead, the reference sounds at every note: 0.0472, 0.0468, 0.0463 and 0.0454
RMS at notes 24, 36, 48 and 60.

That invalidates every low-note measurement made with that patch, including the
one in the note above. The engine reads `+39` correctly; only the probe did not.

**With it fixed**, the isolated sample path -- one tone, white noise, filter off,
envelope flat -- reads:

| note | 24 | 36 | 48 | 60 | 72 | 84 | 96 |
|---|---|---|---|---|---|---|---|
| reference | 0.04724 | 0.04681 | 0.04629 | 0.04536 | 0.04368 | 0.04140 | 0.04002 |
| this engine | 0.04916 | 0.04927 | 0.04917 | 0.04920 | 0.04933 | 0.04955 | 0.04934 |
| difference | +0.34 dB | +0.45 | +0.53 | +0.71 | +1.06 | +1.56 | +1.82 |

**The reference loses 1.4 dB as the note rises and this engine loses nothing.**
That is the tilt, isolated: not in the chip's gain path, which the register
readout showed is flat, but in what reaches it.

**One caveat, stated rather than buried.** The reference generates at 64 kHz and
resamples to 32, so it carries an anti-alias filter this engine does not. White
noise played faster puts more of its energy where that filter works, which on
this particular test signal could produce the whole fall on its own. The tilt
measured here may therefore belong to the reference's implementation rather than
to the machine, and a real instrument tone would show less of it. Before this is
chased further it should be repeated on a harmonic wave, where the aliasing story
does not apply.

**Repeated, and it splits.** Measured full-band and again with everything above
8 kHz removed, where the anti-alias filter cannot reach:

| wave | tilt, full band | tilt, below 8 kHz |
|---|---|---|
| 74 White Noise | +1.14 dB | **-0.04 dB** |
| 30 Alto Sax 1 | +4.08 dB | +4.10 dB |
| 12 Mute GTR 1 | +1.88 dB | +1.89 dB |

On noise the tilt vanishes under band-limiting and what remains is a flat +0.2 dB
across the keyboard -- so that one was the reference's resampling, exactly as
suspected. On the harmonic waves it survives untouched, so there it is real.

**But it is not a level offset.** Compared band by band rather than as one
number, the harmonic tones do not differ by a gain: on Alto Sax the third-octave
correlation runs 0.745 to 0.945 and the residual scatter about the median is
**7 to 14 dB**, with the median itself swinging from +5.96 dB at note 36 to
-8.29 dB at note 84. Mute GTR 1 is tighter (0.927 to 0.992, scatter 2.3 to
10.8 dB) but the same in kind. The two engines produce different spectra on these
isolated tones, and the broadband RMS difference is only what that summarises to.

So the "~2.4 dB level offset" is probably the wrong framing. There is no single
gain that would close it, and the per-note numbers depend on which wave is used.
What is worth measuring instead is the spectral difference itself, wave by wave,
and whether it tracks transposition -- both waves agree best near their zone
roots (Alto Sax 0.945 at note 60, four semitones from its root) and worst far
from them.

A caution for repeating this: per-harmonic comparison does not work on these
samples. Alto Sax 1's strongest partial is not its fundamental once transposed,
and a detector centred on the expected pitch reads 51, 369 and 234 cents of error
on the REFERENCE at notes 36, 48 and 72 -- it is finding a different partial, not
a detuning.

## Not transposition -- the zone, and the loop inside it

The note above guessed that the spectral difference on isolated tones tracks how
far a note sits from its zone root. **It does not, and that guess is withdrawn** --
it rested on two points. Measured across seventeen notes of Alto Sax 1 and
grouped by distance from the root, the third-octave correlation is flat: 0.827
at 0-2 semitones, 0.864 at 3-5, 0.862 at 6-8, 0.803 at 9-20.

**What it tracks is the zone.** The level offset is constant *within* a zone and
grows with the zone index. Notes 82, 86 and 90 all sit in zone 10 at +2, +6 and
+10 semitones from its root, and all three read **+6.7 dB**; zone 0 reads +1.3,
zone 6 +4.4, zone 8 +5.7.

**Aliasing is not the cause**, and that is now measured rather than assumed:
rendering this engine at 128 kHz and band-limiting it properly back to 32 changes
nothing at all -- correlation 0.744 against 0.745, scatter identical to a tenth of
a decibel, RMS identical to a tenth. Whatever it is, it survives four times the
headroom.

**It correlates with the loop.** Against the logarithm of the loop length across
Alto Sax's zones the offset gives **r = -0.81**: 258 frames of loop at +1.3 dB,
182 at +2.4, 129 at +2.7, 53 at +5.5, 37 at +6.7. Short loops are exactly where
a differential decoder's loop handling shows, since the wrap comes round tens of
times a second and any per-pass difference compounds. That is the next thing to
look at.

**One gap found on the way.** The sample record's level byte at +17 is read into
`Sample::level` and **never used**. It is not constant: across the 577 samples it
runs 0 to 127 with 40 % of them away from the median 127, which read linearly
would be 42 dB of range. It does not explain Alto Sax, whose zones all carry 120,
but it will matter elsewhere. Applied as a straight linear gain it moves the mean
absolute level error over the bank from 4.09 dB to 3.85 -- and silences a patch,
because bytes of 0 exist and this ROM gives every other level byte its own dB
curve. It needs that curve measured before it can be used.

## Not the loop either -- the waveforms simply differ

The loop was the next suspect, since the offset tracks loop length at r = -0.81.
It is not the mechanism.

**Both engines are stable at the shortest loop there is.** On Alto Sax 1's zone
10, whose loop is 37 frames and comes round some 900 times a second, neither side
drifts and neither accumulates DC: across 0.8 seconds the reference holds 0.0637
to 0.0652 RMS and this engine 0.1380 to 0.1457, with DC under 0.008 on both. The
repetition period is 95 samples on both, at a self-correlation of 0.99.

That matters because the ROM's loops are **not** balanced. Over the eleven zone
samples of this wave the per-pass delta sum runs from 0.2 % of RMS on sample 203
to 38 % on sample 211. A pure integrator would reach the clamp in a tenth of a
second on the latter. This engine snapshots the accumulator at the loop point and
restores it; the reference is stable too, so it restores as well or corrects it
some other way. A comment in `jv_engine.cpp` claiming the factory loops are
"authored exactly balanced -- the drift is precisely zero for every sample
checked" was simply wrong, and is corrected.

**What is actually happening is more basic.** Cross-correlated at their best
alignment, the two engines' waveforms agree at only **0.49** on note 82 and
**0.39** on note 62 -- with the same pitch, the same period, and amplitude
ratios of +6.8 and +1.5 dB. They are not the same signal at different levels.
They are different signals synthesised from the same sample.

So the level difference on isolated sustained tones is a symptom, not the fault,
and no gain constant will close it. What is left to find is why two decoders
reading the same DPCM data at the same rate produce waveforms that correlate at
0.4. That is a bigger question than the calibration it was mistaken for, and it
is where this stops for now.

## The waveform difference is two things, and one of them is only tuning

The note above concluded that the two engines "are different signals synthesised
from the same sample". **Half of that is withdrawn.**

The comparison is now made against the chip's own interpolated value -- the
`test` word it hands to its filter, logged sample by sample -- rather than
against its finished output, and with a positive control that passes: the chip's
filter input against its own output, with the filter wide open, correlates
**1.0000** at a lag of one sample.

**On a long loop the waveforms match.** At note 62, zone 3 of Alto Sax 1 with a
152-frame loop, the correlation is **0.988 over 25 ms** and 0.92 over 50 -- and
then it falls away: 0.62 at 100 ms, 0.38 at 300. That shape is not two different
signals. It is one signal at two slightly different rates, drifting apart. Tracked
by the best alignment of successive 20 ms windows, the drift is **+161 samples per
second, which is +8.70 cents**. The earlier long-window correlation of 0.39 was
measuring that and nothing else.

**On the shortest loop they really do differ.** At note 82, zone 10 with a
37-frame loop, the rate difference is only -3.37 cents -- far too little to
decorrelate anything over 25 ms -- and yet the short-window correlation is
**0.573**. There the waveforms are genuinely unlike, and that is the zone whose
level offset is +6.7 dB.

So the two symptoms separate cleanly:

| | note 62, loop 152 | note 82, loop 37 |
|---|---|---|
| correlation over 25 ms | 0.94 – 0.99 | 0.573 |
| rate difference | +8.70 ct | -3.37 ct |
| level offset | +1.5 dB | +6.7 dB |

Long loops: a few cents of tuning, which the zone `tune` words could account for
and which is the same order as the five-cent global difference measured earlier.
Short loops: a real difference in what comes out of the decoder, with the level
offset riding on it. Those want separate investigations, and only the second is
about the sample path.

## Short loops: the wrap is not where the error is

The obvious suspect on the short-loop zone was the loop wrap itself. This engine
snapshots the DPCM accumulator at the loop point and restores it there, which puts
a step in the middle of the four-sample window the B-spline is reading -- and on
a 37-frame loop that boundary is an eighth of the waveform and comes round some
900 times a second. It is a good story and it is wrong.

Aligned against the chip's own interpolated value at note 82 and folded onto the
95-sample period, the residual does not sit at any one phase. It is spread across
the whole cycle and **tracks the signal**: the largest error, 2.49, falls at
phase 9 where the signal itself is largest at 3.05, and the smallest error at
phase 65 where the signal is quiet. A glitch at the wrap would show as a spike at
one phase and does not.

What it looks like instead is distortion rather than displacement. Fitting the
best scale factor between the two gives 0.58 with a residual of **0.82 against a
unity signal** -- so barely a third of the energy is common. The two waveforms
share their gross shape and differ everywhere within it.

That is where this stops. The wrap is excluded, the loop drift is excluded, the
rate difference is excluded (-3.37 cents at this note, far too small), aliasing
is excluded, and the chip's gain path is flat. What remains is the decoder itself
on short loops, and finding it needs a fresh look rather than another lap of the
same probe.

## An observation about zone selection, NOT yet a finding

Tracing the chip's decoder address sample by sample -- the full address, page
included, taken from `ram1[4]` after it is written -- turns up something that
would matter a great deal if it holds up. **It is recorded here as an
observation, not a finding, because the harness that produced it has been wrong
four times in this session already and this claim deserves better evidence than
that.**

On the synthetic single-tone patch with wave 30 Alto Sax 1, the addresses the
chip reads sit inside these samples:

| note | chip's sample | its root | our sample | its root |
|---|---|---|---|---|
| 50 | 203 | 53 | 201 | 47 |
| 62 | 204 | 56 | **204** | **56** |
| 74 | 204 | 56 | 209 | 71 |
| 78 | 205 | 59 | 210 | 74 |
| 82 | 205 | 59 | 211 | 80 |
| 86 | 205 | 59 | 211 | 80 |

At note 82 the chip's addresses span 3923716..3923845, which is exactly sample
205's loop, while this engine is in sample 211's. Same pitch, different sample --
which would account for the whole short-loop divergence at a stroke: correlation
0.57, +6.7 dB, and a spectrum that differs everywhere.

**Three things argue against taking it at face value.** This engine's selection
follows the split table exactly -- zone 9 covers to note 79 and zone 10 to 93, so
note 82 is zone 10 -- and on A57 Slap Bass the level ratio was measured stepping
at the split boundaries and nowhere else, which says the rule is right there. The
chip barely moves across the keyboard here, staying in roots 53 to 59 over three
octaves, which is not what a multisample is for. And at note 86 from root 59 the
rate would be 4.76 while the chip's decoder advances at most four steps per
output sample, so it could not reach that pitch from that sample at all.

Either the trace is reading the wrong slot, or `ram1[4]` is not what it appears
to be at the moment it is sampled, or the zone selection genuinely differs and
the pitch is arrived at some other way. Resolving that needs a second, independent
handle on which sample is sounding -- the obvious one being to zero a candidate
sample's bytes in the wave blob and hear which notes go silent.

## The zone-selection observation was the probe again -- and what fell out of it

The observation in the note above -- that the chip appears to play sample 205
where this engine plays 211 -- is **withdrawn. It was the probe, for the fifth
time this session.** What it left behind is worth more than the false lead.

**How it was settled.** The wave ROM cannot be patched on disk, but it can be
zeroed in the emulator's memory after the SHA1 check, which only guards the
files. Zeroing one sample's bytes and hearing which notes go silent is a handle
on zone selection that owes nothing to the address trace. With the synthetic
patch as it stood, zeroing sample 205 silenced notes 78, 82 and 86 outright while
zeroing 211 changed nothing at all -- so the trace was reporting truly, and the
machine really was playing 205.

**Why.** The synthetic patch set tone byte +40 to 119. That byte packs the pitch
keyfollow, and 119 is nibbles 7 and 7. Measured, a tone with +40 = 119 moves from
208 Hz at note 40 to 360 Hz at note 92 -- **9.5 semitones over 52 keys, about
18 % tracking**. It was never near note 82 in pitch, so the firmware picked a low
zone, correctly. Set to A01's own 124 the map becomes sample 203 at note 57, 204
at 60, 205 at 63 and **211 at notes 81, 84, 88 and 92** -- exactly what the split
table says. **This engine's zone selection is right.**

**What fell out.** The pitch keyfollow is the **low** nibble of +40, and its
"one octave per twelve keys" value is **12**, not the 7 that reads as neutral
everywhere else in this ROM. Nibble 7 is about +18 %; nibble 0 runs the pitch
*down* as the key rises, so it is around -100 %.

**And the engine already had it right.** The claim written here first -- that
this engine reads none of +40 and assumes +100 % for every tone -- was taken from
a stale comment in `jv_tone_map.h` and is wrong: `startVoice` has read
`jv_kf16(t[40] & 15)` all along. Swept across all sixteen values and timed at
notes 57 and 63, the keyfollow measures -98.7, -70.7, -49.6, -30.6, -9.5, 0,
+9.5, +21.2, +30.6, +40.1, +49.6, +70.7, +98.7, +121.8, +151.7 and +198.3 per
cent, against a table already holding -100, -70, -50, -30, -10, 0, 10, 20, 30,
40, 50, 70, 100, 120, 150, 200. **Every entry within about 1.5 %**, with index 12
landing on +98.7 where the standard tone must be.

So the 32 tones that carry something other than 12 are handled correctly, and
there was nothing to fix. What the round bought is that `JV_KF16` is now measured
rather than read off the manual, and that the stale comment which caused the
false alarm is gone. The high nibble is 7 on 534 of 539 tones and is not read.

## The sample record: +17 does nothing, and +15/+16 is not simply a tune

Three questions about the sample record, answered by patching bytes into the
emulator's in-memory `rom2` before the reset -- which reaches the firmware, since
patching `+12` there visibly changes the sound while the SHA1 check only guards
the files on disk.

**+17 does nothing.** Swept across 0, 1, 2, 4, 8, 16, 24, 32, 48, 64, 80, 96,
107, 112, 117, 120 and 127, the reference's output RMS is **0.045467 at every
single value** -- one distinct number over the whole range. It carries 21
different values across the 577 samples and none of them matters. This engine
reads it into `Sample::level` and never uses it, and that is correct. The note
above, which called that a gap worth closing, is withdrawn.

**+09 and +10 are dead** -- zero on all 577 samples.

**+15/+16 is a second sixteen-bit field that acts.** Patched, it moves the pitch
on exactly the same law as the tune word at +13/+14: over the range 800 to 1312
both shift the pitch about 49.5 cents, so roughly 0.097 cents per unit, neutral
at 1024. 554 of the 577 samples sit at neutral; the other 23 run from -9.7 to
+10.6 cents and are concentrated -- eleven of them belong to wave 28 Trombone 1,
three to Harp 1, two to Alto Sax 1.

**And adding it makes the pitch worse.** Measured as the rate drift against the
reference, which is the method that survives these samples where a partial
detector does not, Trombone 1 sits at 1.4 to 4.5 cents from the reference without
the field -- mean 2.89 -- and at 5.3 to 11.6 cents with it, mean **8.25**. The
field moves the pitch by about its nominal amount, in the wrong direction to
help. So the reference does not apply it to these samples as a plain addition,
even though patching it changes the reference's pitch.

Something conditions it, and what that is has not been found. The engine keeps
reading only +13/+14, which is measurably the closer of the two behaviours.

## Credit

The patch and tone field layout comes from
[giulioz/jv880_juce](https://github.com/giulioz/jv880_juce)
(`Source/dataStructures.h`, by Giulio Zausa), which also carries the reference
emulator this harness drives -- itself derived from
[NukeYKT's Nuked-SC55](https://github.com/nukeykt/Nuked-SC55).

The identification of the effect chip, and with it the explanation of why its
reverb cannot be measured here, comes from the same author's
[giulioz/roland-dsps](https://github.com/giulioz/roland-dsps). It carries no
licence file, so nothing is taken from it but the reading; it is cited above as
a source, which is all it is used for.

That emulator is under a licence forbidding sale and commercial use, which is
compatible with neither MIT nor GPL-3.0. It is therefore **not vendored into
this repository**, and no emulator code will enter a PicoFaceJV firmware image.
The reference emulator is a host-side measuring instrument only; the decoder,
the extractor and the eventual engine are written from scratch, with the ROM
formats documented above serving as the specification.
