Michi71/PicoVintageSynthCollection/instruments/PicoFaceD5/doc/PROJEKTSTAND.md

# PicoFaceD5 — Projektstand

> Forschungs- und Arbeitsprotokoll der D-50-Emulation, deutsch, chronologisch
> gewachsen. Bis zum 11.09.2026 lag es als `CLAUDE.md` in der Wurzel des Repos
> und wurde in jede Arbeitssitzung geladen; seitdem steht es hier bei seinem
> Instrument, und `CLAUDE.md` trägt nur noch die Arbeitsregeln der Sammlung.
> **Vor jeder Änderung am D5-Klang hier lesen** — insbesondere §1 (Rangordnung
> Firmware > Plugin/VST > Ohr), §5 (zurückgezogene Annahmen) und §6 (offene
> Punkte). Die Release-Chronik im „Stand“ endet mit v1.20.1; ab dann führt sie
> `CLAUDE.md`.

**Stand:** Release **v1.20.1** (11.09.2026, Tag auf `6c1a452`; kein D5-Inhalt — #161: ein PC ohne offenes MIDI-Programm liest den USB-MIDI-Endpoint nie, das Active Sensing der reface-Ports füllte TinyUSBs FIFO nach 3,2 s, und der Display-Flush wartete auf die leere Sendewarteschlange → DX/YC/CP-Oberfläche stand; Kern erkennt die gestaute Warteschlange jetzt (PR #165); davor v1.20.0 auf `7aa6efe`: PicoFaceCP passt auf einen 4-MB-Flash (PR #164: die fünf gebauten Sample-Sätze loopen 40–100 ms früher, jeder Loop-Zyklus per Referenz-Fingerabdruck innerhalb 1 dB / 10 % des alten, Abbild 4,43 → 3,99 MB, kein anderes Instrument berührt); davor v1.19.2 auf `2ef91ca` mit der Patch-Seite in einer Schriftgröße mit Laufschrift für lange Namen (PR #163) und einem **Teil-Flush** der Anzeige: `picoface_ui_flush_mask` statt des Zählers, `Display::flush(y0,y1)` schiebt nur berührte Kachelzeilen; Hardware-Befund Michael: keine Underruns, D5 max. 60 % bei Legato mit laufender Schrift; davor v1.19.1 auf `6c865a4` mit der lesbaren GUI (#162) und der Entscheidung, dass die Encoder-Belegung aus v1.19.0 bleibt (Platine unter `hardware/` ist die Referenz, keine Bauvariante); davor v1.19.0 auf `4e610cf` mit der gemeinsamen GUI (#160) und der J6-Kalibrierung (#157–#159), v1.18.0 auf `6c12ba9` mit D5 #156: Tick 97,66 Hz aus der Firmware-Timer-Init, LFO-Formen, Lower-Ton 4 ms, Ringprodukt, Low-Shelf, P-ENV-Timing; v1.17.0 auf `df1abae` mit #155, v1.16.0 auf `9f22d9f` mit #153/#154, v1.15.0 mit #150–#152, v1.14.1 mit #149, v1.14.0 mit #146–#148; D5 wie immer nicht in den Binaries, sondern nur aus dem lokalen Baum — **nach einem neuen Tag `cmake -S . -B build` laufen lassen**, sonst trägt das Abbild die Version des vorigen Releases im Splash). Nichts Ungereleastes auf `main`. Weitere Arbeit von `main` aus in einem neuen Branch. · **Letzter Arbeits-Commit:** `867fdb3` (SysEx Stufe 3)

**GUI-Umbau (08.09.2026, #160) — was sich für D5 ändert:** `D5_Display.cpp/.h` **gibt es nicht mehr**. Gezeichnet wird über das gemeinsame Kit `core/include/picoface/ui_kit.h`; `D5_Instrument::draw()` ruft `kit::header` / `kit::panelDuo` / `kit::panelName` / `kit::footer` direkt. Der Controller liefert dafür `valueA()` / `valueB()` (Name, fertig formatierter Wert, Position auf der Skala oder negativ) statt der alten `lineA()` / `lineB()`. **Die Patch-Seite (seit v1.19.2):** `D5_Controller::patchNumber()`/`patchName()` liefern Nummer und Name getrennt; `kit::panelName(d, number, name, sub, b, nowMs)` zeigt die Nummer fest in helvB14 und den Namen in helvB12 — läuft er nicht in die Breite, scrollt er (1,2 s Halten, 48 px/s, Lücke 24 px), das Instrument tickt dafür `kit::marqueeTick()` alle 40 ms, solange `panelName` true liefert. **Die sechs Diagnosefelder (`P… B… U… A…/… N…`) stehen seit v1.19.1 nicht mehr in einer Fußzeile, sondern auf der Seite `Diag`** (`kPageDiag`, letzte Seite, `kit::diagnostics`, vier Zeilen: CPU/Bench, Underruns, Voices, Notes/shed) — die Fußzeile ist im ganzen Kit abgeschafft (#161: sie kostete dem Körper neun Zeilen auf einem Bildschirm, der keine übrig hat). Wer den D5 unter Last beobachtet, blättert auf diese Seite. Panels lassen sich ohne Hardware ansehen: `tools/host_tests/ui/build_ui_kit.sh`, rendert in etwa einer Sekunde nach PNG.

**Scratchpad:** der Pfad der Session, in der die D5-Arbeit lief, **existiert nicht mehr** (`…/6bac39c9-…/scratchpad`, gelöscht). Damit sind alle unten genannten Scratchpad-Werkzeuge weg — `probe_*.py`, `render_bytes.cpp`, `note_st.cpp`, `sweep*.csv`, die `142/`-Analysen und die Verifikations-Suite aus §7. **Sie sind nach den Beschreibungen in diesem Dokument neu zu bauen**, wenn sie wieder gebraucht werden; die Beschreibungen sind genau deshalb so ausführlich. Dauerhaft im Repo liegen nur `tools/d5_vst/`, `tools/host_tests/d5/` und `tools/host_tests/ui/`.
---

**QUELLENLAGE (03.09.2026):** Niemand im Umfeld besitzt ein echtes D-50: Michael nicht, luginf (#142) nicht — die Aufnahmen aus #142 stammen aus Rolands D-50-Plugin (ältere Version), Michaels Kalibriersätze aus Rolands neuem D-50-VST. Alle Aussagen der Form „das Gerät zeigt …“ in diesem Dokument, die auf luginf-Material beruhen, meinen das Plugin. Hardware-Anker bleiben nur Michaels alte Captures (WaveSQU/WaveSAW, Herkunft: Netzfunde) und die Firmware selbst. Rangordnung unverändert: **Firmware > Plugin/VST (für Chip-Gesetze, wo die Firmware schweigt) > Ohr.**

## 1. Grundsatzentscheidung dieser Session

**Die Original-Firmware ist die Master-Schablone.** Michaels explizite Ansage (13.08.2026) nach dem ersten Disassembly-Ergebnis: „deutlich besser als unsere gemessenen Werte." Rangordnung ab sofort: **Firmware > Ohr-/Referenzmessung**. Die alte Regel „Aufnahmen schlagen Analogie" gilt nur noch dort, wo die Firmware schweigt. Bei Konflikt gilt die Annahme, dass die Messung etwas anderes gemessen hat — was sich zweimal bestätigt hat (siehe §5).

---

## 2. Werkzeugkette (neu etabliert)

- **MAME 0.289** ist lokal installiert und kennt den `d50`-Treiber samt 78K/III-Debugger. ROM-Set aus `~/develop/Roland_D50` im Scratchpad zusammengebaut (PCM aus A+B kombiniert, CRC exakt).
- Disassembly headless: `mame d50 -rompath … -video none -sound none -debug -debugscript <scr>` mit `dasm out.asm,0xSTART,0xLEN,0`.
- **Fallstrick:** Das Listing des IC25 zeigt unterhalb `0x07C0` die **EPROM-Kopie**, nicht das echte interne ROM → Hybrid-ROM nötig (liegt im Scratchpad als `roms2/`, Listing `ic25_true_low.asm`).
- **Fallstrick:** MAMEs `BP`/`BN`-Mnemonics sind **invertiert** zu lesen.
- Bank-Fenster: Port-P0-Oberbits; `0xA0` blendet EPROM-Datei `0xC000–0xFFFF` auf CPU `0x8000–0xBFFF` (+0x4000).

---

## 3. Aus der Firmware bewiesen und eingebaut

### Parametertabellen (IC25)
| Tabelle | Bedeutung | Status |
|---|---|---|
| `0x008C` | Zeitgesetz `law[0]=1`, sonst `floor(8·log2(103/d))` | byte-exakt in `kEnvLaw` |
| `0x01F1` | Keyfollow 17×u16, echte D-50-Stretchwerte s1/s2 | eingebaut |
| `0x0213` | LFO-Raten-Inkremente `16·2^(k/10)` (**kein** Tiefengesetz) | Form übernommen |
| `0x02EC` | 0..100 → 0..255-Skalierer (nicht Identität) | Lesung war schon korrekt |
| `0x08EC` | TVF-Bias-Steigung, symmetrisch um 7 | eingebaut |
| `0x0AB2` | TVA-Bias-Kurve 13 Einträge | eingebaut |
| `0x14A2` | P-ENV-Segmentdauern in Ticks (×4-Faltung ab Idx 32) | `kPEnvTicks` |
| `0x14D5` | P-ENV-Level-Kurve (≈x^1,7) | `kPEnvLevel` |
| `0x17F4` | P-Mod-Tiefenkurve für c22/c23/c24 | `kPModCurve` |
| `0x1859` | LFO-Fade-Schrittweite | `kLfoFadeStep` |
| `0x18E3` | Portamento-Slew (101 Werte, T[0]=255 … T[100]=1) | `kPortaRate`, eingebaut |
| ic22 `0xFF00/0xFF80` | PCM-Attribute: Längenklasse+Loop-Flag / Startseite | eingebaut |

### Pitch-Gesetz (IC25 0x0357–0x03E3, byte-exakt bewiesen)
- Partial-Pitchkonstante: `(coarse·256 + scaler(fine)) − 0x2480 + (scaler(TonFine C598/C599) − 128)`, Einheit **1/256 Halbton**; `0x2480 = 36·256 + 128` ⇒ **Neutral Coarse 36, Fine 50**, Fine/Skala über Tabelle 0x02EC. Ergebnis → CD6C..6F/CD70..73, im Komponierer (0x0D99) ×0x5555 (= 4096/12/256, Umrechnung in Chip-Einheiten 341,33/Halbton), dann ± Keyfollow·CB20, P-ENV, LFO, Clamp 0x6800.
- **Der Pitch-Pfad ist wellenform-blind** — kein [DE+06]-Read irgendwo im Pitch. Die Sägezahn-Oktav-Beziehung ist reine Chip-Sache (siehe Sägezahn-Abschnitt unten).

### Hüllkurven (`d5_env.h`)
- Chip-Rampe pro Segment, Rate-Index `idx`, **+8 = doppelte Geschwindigkeit**.
- `T1`: `clamp(Tbyte + law[Ziel] − velOff − keyOff)`, **ohne** ×1,25. **Byte 0 ist die schnellste Rampe (idx klemmt ≥ 1, Vollausschlag ≈ 3 ms), NIE ein Ein-Sample-Sprung** — Korrektur unserer unbewiesenen Modellierung aus `0497b70`, die jede perkussive Attacke zum Stufensprung machte (Michaels „Staubkorn auf der Schallplatte" bei Sequenzen, 14.08.). Nur `l[0]==0` (distanzlos) bleibt bei Dauer 0. Ein-Sample-Sofortsprung ist firmware-bewiesen NUR beim P-ENV (`kPEnvTicks[0]`), andere Struktur.
- **Stimmen-Raub / Retrigger:** `Env5::start` setzt den Pegel NICHT auf 0 — die Rampe läuft vom gehaltenen Wert weiter (munt LA32Ramp: „the starting point of the ramp is whatever internal value the LA-32 had when the registers were set"; Reset nur bei Synth-Reset). Nullen schnitt eine klingende Note beim Stehlen in einem Sample ab.
- `T2..T4`: `clamp(law[|ΔL|] + u125)` mit `u125 = u + (u>>2)` (×1,25) → **zeitkonstant**, Distanz kürzt sich.
- **Release: ohne law → ratenkonstant.** Der Distanz-Lookup wird im ROM berechnet und überschrieben (toter Code, in beiden Hüllkurven).
- TVF-Distanzen in Chip-Einheiten (`·D>>8`), TVA in rohen Panel-Einheiten = **Chip-Log-Einheiten, 16/Oktave = 0,376 dB**.
- TVA-Levels exponentiell `2^((L−100)/16)`; Sustain 0 = absolute Stille (ROM-Sonderfall).
- Velocity wirkt **nur** auf T1; Key-Keyfollow auf alle Phasen (arithmetischer Shift, unter C4 negativ = länger).
- **Kalibrierte Konstante: `kRampClock = 64000` (17.08., korrigiert von 90509.7).** Das ×√2 stammte aus vier Messungen an *gespielten Phrasen mit Hall*, von denen zwei später als Fehlmessung zurückgezogen wurden (Horn = Typ-8-Fahne, Polysynth = schließendes Filter). Eine **trockene Einzelnote** (Rolands eigenes D-50-Plugin, Reverb+Chorus auf 0) entscheidet es: der Release ist bauartbedingt ratenkonstant und damit die einzige Phase, die diesen Takt direkt messbar macht — **Soundtrack C5: −18,25 dB/s, und der Fit bewegt sich um 0,1 %, egal ob 10-, 20- oder 50-ms-Fenster.** Unsere Engine bei 64000: −18,16 (0,6 % daneben), bei 90509.7: −25,65 (**40 % daneben**). Zweite trockene Note Choir C5: gemessen −206 dB/s, bei 64000 −240 (16 %, innerhalb ihrer eigenen ±18-%-Streuung — 0,2 s gestufter Absturz mit Vibrato ist eine 200× unsicherere Messung), bei 90509.7 −337 (64 %). **Der herausgefallene Faktor ist genau der, den wir hineingerechnet hatten**, und 64000 ist munts unabhängige Ableitung für denselben Chip aus dem MT-32. **HERKUNFT DER REFERENZ (17.08., nachgetragen): die fünf trockenen Noten stammen aus einer Kopie des Roland-D-50-Plugins, deren Lizenzlage ungeklärt ist. Zwei Folgen: (1) sie taugt NICHT als Autorität -- das Argument 'Rolands eigenes Modell sagt es' steht nicht zur Verfügung, und die DLL wurde nicht zerlegt, es ist nichts daraus entnommen (die Suche nach den ROM-Daten war ohnehin negativ: 0/5 Proben je Image, die Samples liegen woanders oder komprimiert); (2) das Ergebnis hängt nicht an ihr -- es tragen munts unabhängige Ableitung von 64000 für denselben Chip, die Messung am inneren Segment über einen ANDEREN Codepfad, und der Umstand, dass das ersetzte √2 auf vier hallverseuchten Phrasen ruhte, von denen zwei längst zurückgezogen waren. Belastbar wäre eine Lizenzkopie oder besser drei trockene Noten von echter Hardware -- letzteres ist auch die einzige Instanz, die die 15-17 %% Restabweichung auf Nylon Atmosphere und Intruder FX entscheiden kann.** **Fünf trockene Einzelnoten (Reverb+Chorus 0, alle C5), einheitlich schwellenbasiert gemessen (20 dB Abfall ab Loslassen -- ein FESTES Zeitfenster misst Unsinn, sobald der Release kürzer ist als das Fenster; genau das liess mich einmal einen 4x-Fehler halluzinieren):** Choir Byte 46 -206,4 (+-18 %) gegen unsere -233,8 (13 %, verträglich); **Ethnic Session Byte 49 -122,7 (+-4 %) gegen -121,6 => 0,9 %**; Nylon Atmosphere Byte 56 -60,0 (+-5 %) gegen -50,9 => 15 %; **Soundtrack Byte 67 -18,25 (+-0,1 %) gegen -18,1 => 0,6 %**; Intruder FX Byte 71 -12,70 (+-3,5 %) gegen -10,5 => 17 %. **Zusätzlich der beste Messpunkt überhaupt: Ethnics innerer Abfall im Halten** (-2,283 dB/s, 0,4 % Streuung, 0,03 dB Restfehler) laeuft ueber den **Zeitgesetz-Pfad**, also anderen Code als der Release -- dort 2,1 % bei 60000, 3,5 % bei 64000, **15,6 % bei 90509.7**. Der Takt ist damit auf zwei unabhaengigen Pfaden bestaetigt. **ZURUECKGEZOGEN: der behauptete Trend 'impliziter Takt steigt mit dem Release-Byte'** -- es gibt keine Ordnung nach Byte (49 ok, 56 nicht, 67 ok, 71 nicht) und keine nach Partialtyp (die zwei Treffer sind einmal PCM, einmal Synth). **Ebenfalls zurueckgezogen: zwei Fehldiagnosen** -- die TVF schliesse im Release in einem Sample (nein: `build_tvf_env` setzt die Levels gar nicht, die kommen aus dem Mapping, und Ethnics TVF-Sustain-Byte ist 0), und der `r[4] *= 3.0f` im PCM-Zweig sei schuld (nein: `Voice::note_on` ueberschreibt `pcm_env` bei jedem Anschlag mit der firmware-gebauten Huellkurve; der Faktor gilt nur fuer die acht Fallback-Presets, und **seine Begruendung im Kommentar zitiert den zurueckgezogenen Polysynth-Anker** -- bei Gelegenheit aufraeumen). **OFFEN: 15-17 % Restabweichung auf Nylon Atmosphere und Intruder FX**, ausserhalb ihrer Messunsicherheit, ohne Erklaerung -- keine weitere Vermutung ohne neue Evidenz. **Quelle ist Rolands Software-Modell, nicht das Gerät** — für die Richtung (40 %) belanglos, für die letzte Ziffer nicht. `kRampClock` ist über `-DD5_RAMP_CLOCK` beim Kompilieren überschreibbar, damit solche Sweeps ohne Quelländerung laufen. **Folgen:** jede Hüllkurvenphase 41 % langsamer, Fahnen bis +30 % (Spacious Sweep 5,15 → 6,70 s) ⇒ mehr Stimmendruck und häufigeres Trimmen; tune2 **331/384** (vorher 329), click2 unverändert 2, **seqclick 10 → 16** — die sechs neuen sind Note-On-Sprünge bei ~3× Basislinie auf Sägezahn-Patches, dieselbe Klasse wie die dokumentierten (die Reset-Flanke landet bei mehr Überlappung auf lauterem Untergrund); **kein einziges neues Note-Off-Flag**.

### TVA-Levelbasis (`tva_chip_level`)
```
base = max(0, p35 + 31 − floor(1,5·|p36−50|) − (PCM ? 0 : p14>>1))
velT = d≥0 ? (4·d·vel)>>8 : (4·|d|·(128−vel))>>8      // d = p36−50
bias = (kTvaBiasCurve[p38]·dist)>>5, harte Stummklemme bei prod ≥ 0x1000
chip = max(0, base + velT − bias)   → Normierung 155 = 1,0
```
Velocity läuft **ausschließlich** hierüber (`gain_=1` im Byte-Pfad); das alte multiplikative `velo_sens` ist auf dem Bank-Pfad tot.

### Mischer (aus dem Bank-Code, Richtungen PROVEN)
- Partial-Balance c47: laute Seite **steigt** auf 1,25× (nicht nur leise absenken); `c47=0` = Partial 1 voll.
- Tone-Balance pb33: `min(4b,255)/200` je Seite, `pb33>50` = Upper lauter; Whole-Modus neutral (beide 200, Upper auf allen vier Slots).
- `p.upper.level = p.lower.level = 0.58f` (Ausgleich der −8,4 dB Median-Verschiebung durch die neue Levelbasis).

### PCM
- **PCM-Partials bekommen KEINEN TVF** — vier unabhängige Gates auf dem Typ-Bit. Frühere Notiz „Chip filtert auch PCM" war falsch, ist zurückgezogen.
- **Kombiwellen 77–100 gelöst:** `start = (T80[n]−0x40)·2048` Worte, `len = 2048 << (T00[n]&7)`. Alle 24 in `d5_sample_table.json` eingetragen; 100/100 Samples aufgelöst. Vorher stumme Partials in **DigitalNativeDance, Breathy Chiffer, Tine Wave, Intruder FX** spielen jetzt.
- Loop-RAM nimmt nur noch Längen ≤2048 Worte (`loop_in_ram`), Kombiregionen bleiben im Flash.

### PCM-Tonhöhe (02.09.2026, Issue #142, aus IC25 + munt bewiesen)
- **Es gibt keine per-Sample-Wurzel, weder in der Firmware noch im Chip.** Der PCM-Pfad des Note-On-Setups (IC25 0x04AA–0x04D3) liest die PCM-Nummer `[DE+07H]` genau zweimal: Tabelle 0xBF00 (Längenklasse, `<<4 | 0x08` → Chip-Register CD5D) und 0xBF80 (Startseite → CD64/65). Der Komponierer 0x0D99 endet mit `ADD FE7B,FE7B` (Typ-Byte, Bit 7 = PCM-Flag aus der Struktur-Tabelle 0x02E5) und **`SUBW AX,#4000H` bei gesetztem Carry** (0x0F44–0x0F4E, Zwilling 0x0F9A im Negativ-Keyfollow-Zweig) — **exakt −4 Oktaven** (4096/Oktave) für jedes PCM-Partial, sonst dasselbe Wort wie ein Rechteck.
- **Chip-Gesetz (munt LA32WaveGenerator):** Synth-Schritt `2^(p/4096+4)` über eine 2^20-Periode, PCM-Schritt `2^(p/4096+3)` in 1/256 Wort ⇒ bei gleichem Wort läuft ein PCM mit `f·2048/32000` Worten je Sample (2048-Wort-Periode ≡ Rechteck-Tonhöhe). Mit den −4 Oktaven: **Schritt = f/250 Hz für jedes Sample** (`kPcmPitchRefHz = 32000/128`). Coarse 36 auf C4 ⇒ 1,046 = gespeicherte Geschwindigkeit; die 2^k-Wort-Loops (32000/2^k Hz) landen so per Konstruktion auf C-Oktaven (128 Worte → C4, 512 → C2, 2048 → C0; die Spect-Zyklen tragen ihren Inhalt bei Harmonischen 130–800, also 2–13 kHz bei Schritt 1).
- **Der alte Engine-Fehler:** `rate = f/root_hz` transponierte jedes Sample auf seine *gemessene* Eigentonhöhe. Das stimmte nur zufällig für Periode 128 (root 250). FluteH/Breath/IndFlt/Bells/Harp/Trumpt/Bones/Violns (Periode 32) lagen **2 Oktaven zu tief** (luginfs „2 octaves lower attack" auf Pipe Solo), Periode 64 eine Oktave zu tief, Periode 256 eine Oktave zu hoch, die Bass-/Piano-Loops (512) zwei, Marmba/Contra/Ooh (1024) drei, **Spect1–7 (2048) vier Oktaven zu hoch** (Inhalt weit über Nyquist → Aliasing). Noise folgte gar nicht der Taste.
- **Bank-Beweis unabhängig vom ROM:** unter munts Gesetz *ohne* die −4 Oktaven säßen die 288 Attack-PCM-Partials der 384 Patches 3–5 Oktaven über der Taste (Modus +3/+4), mit ihnen bei −1/0. Die Klavier-Familie ist der Kontrolltest: Hpiano (Periode 64) bei Coarse 12 und Lpiano (512) bei Coarse 48 ergeben unter der neuen Regel **dasselbe Register** (C3 auf C4), unter der alten lagen sie drei Oktaven auseinander.
- **Messung an der Pipe-Solo-Aufnahme aus #142 (NACHTRAG 03.09.: die Aufnahmen stammen aus Rolands D-50-Plugin — also Modell, nicht Hardware):** 80–300-Hz-Band im ersten 100-ms-Fenster relativ zum 700–1100-Hz-Flötenrank: Original −36/−42/−49 dB, Engine vorher **−3 dB**, nachher **−37 dB**. Stationär −54 gegen alt −5.
- **Zweite Folge derselben Analyse (offen):** die Restfrage, warum unsere PCM-Chiffs *lauter* schienen, war die Oktave — bei 220 Hz sticht ein Flöten-Chiff heraus, bei 880 Hz verschmilzt er mit dem Rank. Die Level-Kette (0x040C/0x09C4/0x09E8/0x0A0B) war byte-exakt geprüft und bleibt es.
- Regressionstest im Repo: `tools/host_tests/d5/build_d5.sh` (synthetische 128/2048/32-Wort-Zyklen → C4/C0/C6). Struktur-Tabelle `kStructures` ist gegen das Owner's Manual S. 22 bestätigt (6 = P+P Mischung, 7 = P+P Ring). `root_hz` bleibt als Materialbeschreibung in `d5_sample_table.json`/`d5_pcm_table.h`, die Engine liest es nicht mehr.

### Arco Strings (1-04), Nachtrag zu #142 (02.09.2026, nicht abgeschlossen)
- **Referenz:** `~/Downloads/14 Arco Strings.mp3` (Michael, gespielte Demo-Phrase mit Hall, Akkorde, unbekannte Velocity; dieselbe Serie wie `36_PipeSolo.mp3`). Als Einzelnoten-Referenz **nur bedingt** brauchbar: die erste „Note" ist ein Akkord G2/G3/G4/D5/G5 (Linien 99/198/389/587/783 gleich stark), die zwei isolierten Stellen (12,25–15,1 s, 15,1–16,6 s) ebenfalls mehrstimmig. **WaveSAW.mp3 erneut geprüft: keine 262-Hz-Linie neben 525** — die Sägezahn-Oktave bleibt.
- **Was daraus belastbar ist:** (1) LFO-1-Rate Byte 68 = **3,1 Hz** in der Aufnahme, unser Gesetz gibt 3,05 — Treffer. (2) Vibrato-Seitenbänder an G2-h3 (294 Hz, ungeteilt): Referenz −7/−8 dB (≈ ±15 ct), wir −19/−24 dB (≈ ±4,7 ct = P-Mod-Tiefe 2 durch `kPModCurve`). Die Referenz vibriert also **tiefer**, nicht flacher — vermutlich Aftertouch des Spielers (c24 = 9 → bis +24 ct); luginfs „unsere vibriert mehr" ist damit nicht belegt. Der Gegensinn der beiden Sägezähne (LFO-Modus + und −) ist byte-exakt. (3) **Onset:** Referenz aus digitaler Stille in ~10 ms auf ein Plateau ~10 dB unter dem späteren Maximum (Swell bis ~1,2 s); wir brauchen für dasselbe Plateau (L1 = 64) **30 ms bei Vel 127, 150 ms bei Vel 64** (TVA-Zeit-Velocity 4 = Maximum). Ob das Spieler-Velocity oder unser T1-Gesetz ist, entscheidet nur eine Einzelnote mit bekannter Velocity.
- **Chorus:** Typ 1, Rate 48 → 1,26 Hz, Tiefe 68 → ±0,44 ms ⇒ ≈ 6 ct Spitzen-Tonhöhenhub, gemessen am Einzel-Sägezahn +1 ct Streuung — der Chorus ist **nicht** die Quelle eines „Vibrierens".
- **„Leise" (Michael):** auf dem Host nicht — Rang 49/64 nach RMS in Bank 1 (−28 dB, lauter als String Ensemble/Legato Strings). TVA-Velocity 60 (d = +10) macht ~7 dB zwischen Vel 40 und 127, dazu der 1-s-Swell; mit MidiKeys-Festvelocity wirkt der Patch leise. Der Lower-Ton (Violns/Cello-PCM) liegt bei −46 dB und hat mit #142 nichts zu tun.
- **Klangfarbe/TVF:** aus dieser Aufnahme **nicht** beurteilbar (Akkorde teilen sich alle geraden Teiltöne). Die einzigen ungeteilten Linien (G2-h3/h5) liegen bei uns auf −20/−26 dB gegen −20/<−40 — kein Hinweis auf ein zu geschlossenes Filter. Der TVF-Pfad bleibt der am schwächsten bewiesene (§3 Sägezahn-Oktave, „bewusst unberührt").
- **Plugin-Einzelnoten (Michael, 02.09., `~/Downloads/Arco_C3/C4/C5.wav`, Rolands D-50-Plugin, Chorus+Reverb AN, Velocity unbekannt; Quelle mit dem bekannten Herkunfts-Vorbehalt, kein Beweis):** (1) **eine Linie je Teilton** — das Plugin verstimmt die zwei Sägezähne (Fine 45/55) nicht gegeneinander und hat **kein** Vibrato (< 1 ct); wir haben ±5 ct Verstimmung (Firmware-Tabelle 0x02EC, byte-exakt) ⇒ Schwebung 1,5 Hz bei C4 mit 9-dB-Einbrüchen, plus ±4,7 ct Vibrato aus `kPModCurve[2]·600 ct`. Beides zusammen ist vermutlich luginfs „vibrating"; die Fine-Lesung ist Firmware, die 600-ct-Vollskala der P-Mod-Tiefe ist PLAUSIBLE — dort ansetzen, nicht beim Fine. (2) **Onset:** Plugin in 10–50 ms auf −5 dB des Maximums, wir bei Vel 1,0 auf −12/−14 (= L1 64 → −13,5 dB nach 0,376 dB/Einheit); Plugin-Verhältnis ist aber durch Hall/Chorus verfälscht (Maximum kommt mit dem Hallaufbau). (3) **Helligkeit:** Plugin im Sustain 6–20 dB heller in h2–h10 (C4 am stärksten). **Kein Widerspruch zur PCM-Oktave:** das Cello-PCM des Lower-Tons liegt im Plugin bei 125/250 Hz für C3/C4 — dieselbe Oktave wie unsere f/250-Regel (die alte Regel hätte eine Oktave höher gelegen), nur 79 ct tiefer (Plugin-Referenz offenbar C4 = Schritt 1,0 statt 250 Hz).
- **NUMMERIERUNG (03.09., Falle):** Rolands Patchnummer **I-BN** = Bank B (1–8) × Nummer N (1–8) ⇒ Index (B−1)·8+N−1; unser Display zählt **1-NN** fortlaufend 1..64. Also I-14 Arco Strings = 1-04, I-36 Pipe Solo = 1-22, **I-37 Soundtrack = 1-23**, **I-55 Stereo Polysynth = 1-37**; unser 1-55 ist **O K Chorale**. Die zwei Absätze darunter über „Soundtrack (1-37)" und „Stereo Polysynth (1-55)" hatten die Bytes der falschen Patches (1-37 = Polysynth, 1-55 = O K Chorale) — die PW-15-Rechtecke mit Spect-PCMs gehören zu **O K Chorale**, das VST-Pulsweitengesetz gilt unabhängig davon. **Mit richtiger Paarung (03.09., neue Engine):** Soundtrack 1-23 (Rechtecke PW 82, TVA L1 = 25 → Swell über T2) gegen die alte Plugin-Note: Hüllkurve Plugin −33 → 0 dB in 0,85 s, wir −24 → 0 in 0,6 s (gleiche Form, der „Swell-Widerspruch" war die Verwechslung); Teiltonprofile decken sich inklusive der Nullstellen h3/h6/h9 (Flankenklemme bei Cutoff 49 — also auch im Roland-Plugin vorhanden). Stereo Polysynth 1-37 (Sägezähne PW 0, TVF 56 + Env 94 mit Sustain 64, TVF-Velocity 94): wir im Sustain 5–20 dB heller als das alte Plugin (h8 −24 gegen −40), dessen Velocity unbekannt ist — mit Velocity 94 auf der Hüllkurve entscheidet die; **offen, mit dem neuen VST bei bekannter Velocity nachmessen** (Hüllkurvenanteil mit ×2 läuft dort in den 240er-Deckel).
- **TVF-Hüllkurvenrichtung aus IC25 bestätigt (02.09.):** Note-On 0x0938–0x094F: `CC80 = Tiefe·velTerm` (Clamp 0xFF), Ziel `= L1·Tiefe`; Release 0x0AC2–0x0AE6: Ziel 0 bei End-Level 0, volle Tiefe bei End-Level 1, Distanz `(100−SusL)·Tiefe` bzw. `SusL·Tiefe`. **Level × Tiefe, positiv, keine Komplementierung** — unsere Richtung ist die der Firmware. Das erklärt NICHT, warum Rolands Plugin bei **Soundtrack (1-37)** trocken in 0,85 s von −33 dB anschwillt, wo wir bei Note-On auf Maximum stehen (TVA T1 = 0, L1 = 100; TVF 100 → 41 → 0 → 64, Tiefe 94, **TVF-Velocity 94 und TVA-Velocity 95 auf P2** ⇒ bei leiser Velocity dumpf und leise). Velocity der alten Plugin-Aufnahmen unbekannt — vor weiterer Deutung erfragen. **Stereo Polysynth (1-55)** trocken: bei uns dominiert Inhalt bei ~900 Hz (+50 dB über h1), im Plugin eine saubere Sägezahnreihe — die Spect-PCMs (Upper P1 Spect1 Coarse 9 kf 1/8, P2 Spect3 Coarse 37 kf 1/4) sind der Verdächtige, nicht untersucht.
- **Die eine Linie im Plugin ist Partial 1 allein:** auf allen drei Tasten liegt sie exakt bei −5 ct (= Fine 45); Partial 2 (Fine 55) fehlt > 30 dB. TVA-Bias scheidet aus — ROM-Tabelle 0x0AB2 = {255,187,137,100,74,54,40,29,21,15,10,5,0}, direkt mit p38 indiziert (0x09CE), p38 = 12 ⇒ 0, wie bei uns. Bleibt der **TVF**: P2 hat Cutoff 51 mit Hüllkurve 90 → 75 → 33 → **Sustain 0** (Tiefe 52), P1 Cutoff 50 mit Sustain 44. Im Plugin ist ein Partial bei Panel-Cutoff ~51 ohne Hüllkurve praktisch stumm, bei uns (Chip 129 ≈ Mitte, munt-Offset +78) bleibt es ein dumpfer, voller Grundton — daher bei uns die Schwebung P1/P2 (luginfs „vibrating") und der um bis zu 6 dB gedrücktere h2/h1. **Hypothese, nicht bewiesen:** die D-50-Cutoff-Komposition sitzt tiefer als die MT-32-Lesung (+78). Firmware-Einstieg: Basis 0x083C `([DE+0DH]+27)/2` in RP3 plus Keyfollow 0x0847–0x08B9 (Tabelle 0x01F2, differentiell WG-KF) und Bias 0x080C–0x0830 (Tabelle 0x08EC); Hüllkurve 0x0938 (`CC80 = Tiefe·velTerm <<2`, Ziel L1·Tiefe); Verbraucher CC80/CCA0 bei 0x0D56/0x0D72; Chip-Schreibung E3xx/E5xx. **Das ist das nächste Arbeitspaket** (TVF-Cutoff byte-exakt), es erklärt Arco Strings, die Helligkeitslücke und vermutlich Michaels „leise".
- **Pulsweite < 50 ist offen:** Firmware schreibt `CD54 = T[PW] + Velocity-Term` (0x07E6–0x0805) **ohne Offset direkt ins Chip-Register** (0x072A → [HL+100H]); munts MT-32-Gate sagt „Register ≤ 128 = 50 % Rechteck". Dagegen: **Owner's Manual S. 35** (PW 0 = 50 %, 50 = deutlich asymmetrisch, 100 = 97 %, stetig), Rolands Plugin (Stereo Polysynth PW 15 → h2 bei −8 dB, bei uns nur ungerade Teiltöne), und die Bank (PW 33 ×7, 37 ×4 auf Bank 1). Entscheidet nur eine Hardware-Aufnahme eines PW-15…40-Rechtecks (Stereo Polysynth C3 trocken). Wenn stetig: Chip-Gesetz `2^((128−reg)/64)`-Form mit Beginn bei 0 statt 128 — die 36 Partials mit PW > 50 sind dann etwas anders, die ~80 mit 1..50 erstmals asymmetrisch.
- **Handbuch S. 30/33/35 bestätigt:** Fine ±50 ct; „Sägezahn = am TVF verarbeitetes Rechteck, am WG ist alles Rechteck"; „bei Sägezahn hebt Pulsweite 50 % (= Wert 0) die Tonhöhe um eine Oktave" — die Sägezahn-Oktave ist damit auch dokumentiert, und sie gilt nur bei symmetrischem Puls.
- **Rolands NEUES D-50-VST (Michael, 02.09., `~/Downloads/Arco_strings/C3|C4|C5_v64|v127.mp3`, trocken, L/R-Korrelation 1,000; Legitimkopie):** ACHTUNG Oktave — die DAW zählt C3 = MIDI 60, Roland C4 = 60; VST-„C3" ≙ unsere Note 60, „C4" ≙ 72, „C5" ≙ 84. Befunde: (1) **beide Sägezähne klingen, ±5 ct verstimmt** (Linienpaar 1,4/3/6,4 Hz bei 262/523/1046 Hz) — Fine-Lesung bestätigt, das stumme P2 des alten Plugins war dessen Eigenheit. (2) **Kein Vibrato** (±3-Hz-Seitenbänder < −37 dB; wir −4…−8 dB aus P-Mod-Tiefe 2 → ±4,7 ct). Die 600-ct-Vollskala von `kPModCurve` ist damit sehr wahrscheinlich zu groß (Tiefe 2 im VST < 0,3 ct ⇒ Vollskala eher ≤ 50 ct); die ROM-Tabelle 0x17F4 selbst ist byte-exakt, nur ihre Einheit ist offen. (3) **Hüllkurve trifft weitgehend**: ab 30 ms decken sich die 50-ms-Trajektorien auf 1–3 dB, inklusive Schwebungs-Einbruch bei 0,95 s; wir starten in den ersten 10–20 ms 7 dB (v127) bzw. 10 dB (v64) tiefer — unser T1 ist bei Vel 64 zu langsam (145 ms gegen ~30 ms). Velocity-Pegelsprung 64→127: VST 4,0 dB, wir 4,1 dB. (4) **Helligkeit ist die Lücke:** VST-Sustain h1..h10 ≈ 0/−8/−12/−15/−17/−19/−20/−22/−23/−25 dB auf allen drei Oktaven nahezu gleich (Filter praktisch offen bzw. voll mitlaufend); wir 0/−10/−14/−18/−23/−27/−33/−39/−45/−57 bei Note 60 und mit steigender Taste noch dumpfer (Note 84: h5 −34, h8 −54). Bei Panel-Cutoff 50/51 + Hüllkurve muss der Chip-Cutoff also weit über unserer „Mitte 128" liegen (munt-Offset +78 gilt für die D-50 offenbar nicht) ⇒ **TVF-Cutoff-Komposition aus IC25 (Einstieg 0x083C) gegen diese sechs Noten kalibrieren** — das ist das Arbeitspaket.
- **Wo das VST als Referenz taugt:** dort, wo die Firmware schweigt — Chip-Gesetze (Cutoff → Spektrum, Pulsweite → Tastverhältnis, LFO-Tiefe → Cent). Sinnvolle nächste VST-Aufnahmen (trocken, Vel 127, Note 60 = „C3" der DAW): Arco Strings mit P2 stumm und TVF-Hüllkurventiefe 0 bei Cutoff 30/50/70/90 (Cutoff-Gesetz); dasselbe Partial als SQU mit PW 0/25/50/75/100 (Pulsweite); ein Patch mit P-Mod-Tiefe 50 und 100 bei LFO-1-Rate 68 (Vibrato-Skala).
- **Vibraphone (1-26) gegen das VST (Michael, 03.09., `vibra_c2_c3.mp3`, DAW-C2/C3 = Note 48/60, trocken, Velocity vermutlich 100):** Linien im Sustain auf ±1 Hz und 1–4 dB deckungsgleich (131/261/394/521/656 Hz), Hüllkurvenform gleich, unsere fällt in den ersten 0,7 s etwas schneller (−13 gegen −5 dB bei 0,5 s auf Note 48). Einziger klarer Unterschied: der **Vibes-PCM-Anschlag** (525/1570 Hz bei Note 48, 1052/3145 bei 60) liegt bei uns **6–10 dB leiser** relativ zum Rechteck-Grundton (VST −1/−2 dB, wir −8/−12). **Velocity war 127** (Michael): mit 127 gerendert schrumpft die Anschlagslücke auf 3–6 dB (Vibes 525/1570 Hz: VST −2/−1, wir −5/−7), und die Rechteck-Obertöne 393/785 Hz liegen im Attack bei uns 5–6 dB tiefer (TVF-Hüllkurve, Tiefe 19). Deutlicher: **unsere TVA-T2 (Byte 63, 100 → 48) läuft ~2× schneller** als im VST (bei 0,5 s wir −15 dB, VST −5; VST erreicht −15 erst bei 0,9 s) — fallendes inneres Segment; Ethnics innerer Abfall war am alten Plugin auf 3,5 % kalibriert, hier widerspricht das neue VST. **Entscheidung Michael (03.09.): bleibt so, bis es jemand anzweifelt** — nicht von selbst wieder aufgreifen. Michaels „unsere klingt unten besser" = weicherer Anschlag plus schnellerer Abfall, Geschmack, kein Fehler in unsere Richtung.
- **Nächster Schritt:** aus #142 **trockene Einzelnoten** (Chorus-/Reverb-Balance 0 am Panel, C3 und C4, Velocity bekannt, 3 s gehalten, keine Akkorde). Harness: Scratchpad `142/arco_note.cpp` (Note, Velocity, dry), `arco_cho.cpp` (Chorus-Isolierung), Analysen inline in der Session vom 02.09.

### TVF-Cutoff-Basis (03.09.2026, aus IC25 0x0809–0x08EB byte-exakt, Nachtrag zu #142)
- **Routine:** 16-bit-Akkumulator RP3 := 0; **Bias** (0x080C–0x083A): Punkt `p16 & 0x3F − 27` relativ C4, Bit 6 = Richtung (0: wirkt unterhalb, 1: oberhalb), Distanz × Magnitude aus **0x08EC = {170,120,85,54,34,21,11,0,11,21,34,54,85,120,170}** (Index p17, unter 7 abgezogen, über 7 addiert); **Cutoff**: `+ (p13 + 27)·128` (0x083C–0x0845); **Keyfollow** (0x0847–0x08B9): `± (kfTVF − kfWG)·(key − 60)`, jeder Keyfollow als High-Byte der u16-Tabelle **0x01F1 = ratio·0x5555** (also `85·ratio`: 0, 10, 21, 32, 42, 53, 64, 74, 85, 106, 128, 170; −1/−½/−¼ negativ), Vorzeichen über R5; dann Clamp 0…0x3FC0, **`SHLW 2` und High-Byte ⇒ alles /64**. Ergebnis → **CD55[B] → Chip-Register [HL+101H]** (0x0734), Paar mit der Pulsweite CD54.
- **Formel:** `Chip-Basis = 2·Cutoff + 54 ± mag·dist/64 ± 85·Δratio·(key−60)/64`. Ein Panel-Schritt = **2 Chip-Einheiten**, Panel 50 = **154** (munt/MT-32: Cutoff + 78 = 128). Hüllkurve (0x0938) und Velocity-Term (0x0908, `109 + vel·sens/64 − sens`) waren schon byte-gleich mit `env_units_`; Bias-Steigung war um 2 zu klein (/128 → /64); Keyfollow lief über die Partial-Note statt die Taste (FE79).
- **Pitch-Deckel (0x08CF–0x08DE):** CDAC[B] = High-Byte des komponierten Pitch-Worts (relativ C4, `NOT1 A.7` ⇒ 128 auf C4, +16/Oktave, 0x0674–0x0680). `Basis ≤ 344 − CDAC` = 216 auf C4, 200 auf C5, 184 auf C6 — munts `pitchDeltaThing` in D-50-Form. Eingebaut als `cap = 216 − (16/12)·(note−60)`.
- **Wirkung gegen Rolands VST (trocken, Arco Strings):** Note 60 v127 h1..h10 vorher 0/−10/−14/−18/−23/−27/−33/−39/−45/**−57**, nachher 0/−10/−13/−16/−19/−22/−25/−27/−28/**−29,5**, VST 0/−8/−12/−15/−17/−19/−20/−22/−23/**−25**. Note 72 auf 1–4 dB, Note 84 bleibt 3–10 dB dumpfer (unser differentieller Keyfollow Δr = −¼ zieht mit der Taste stärker zu als das VST — offen). Bank 1: Median +0,3 dB RMS, Shakuhachi/Oriental Bells/Afterthought/Vibraphone +7…9 dB (tiefe Cutoffs öffnen sich), kein Patch auf Vollaussteuerung; Pipe Solo unverändert (h3/h1 −11,6).
- **Sonde (Sägezahn, kein Env, Taste C4):** Panel 25 → Chip 104 → reiner Sinus (h2 −132 dB); Panel 50 → 154 → h2/h4/h10 = −10,6/−31,5/−57; Panel 75 → 204 → −8,0/−14,6/−23,7 (≈ VST-Arco-Sustain); Panel 100 → 254, gedeckelt auf 216 → −8,0/−14,5/−22,9; auf C6 sind Panel 75 und 100 identisch (beide auf 184 gekappt). Arco-Sustain liegt bei uns auf 154 + 22 = 176; das VST klingt wie ~190–204, die Restlücke ist also ≈ eine Cutoff-Oktave (16 Einheiten) — Kandidaten: Hüllkurven-Skala im Chip oder Bezug des Cutoffs auf Rechteck- statt Sägezahn-Grundwelle; nicht entschieden. Regressionstest `tools/host_tests/d5/tvf_cutoff_host_test.cpp` (6 Fälle).
- **Cutoff-Sweep im VST (Michael, 03.09., `co_30/50/70/90.mp3`, nur Upper P1, Hüllkurventiefe 0, trocken):** Fit des Teiltonprofils gegen einen Chip-Sweep unseres Modells: Panel 30 → Sinus (Chip < 128, wie 2·30+54 = 114), **50 → 156 (Firmware 154), 70 → 200 (194), 90 → 232 (234)**, Restfehler 0,3–1,0 dB. Basisformel UND munts Chip-Gesetz Cutoff → Spektrum sind damit vom VST bestätigt. Aus derselben Fit-Methode auf die sechs Arco-Noten: Sustain-Chipwert 198 (v127) / 184 (v64) ⇒ Hüllkurvenanteil **+44/+30**, unser Zielbyte `L·CC80/256` sagt 22/15 — **exakt Faktor 2**. Munt hat keinen (`TARGET_SHIFTS = 18` = Basis-Skala), also D-50 ≠ MT-32-Lesung oder munt-Lücke; eingebaut als `env_units_ ×2` (VST-kalibriert, Firmware-Zielbyte selbst ist bewiesen). Danach Arco Note 60 auf 2–4 dB, 72 auf 3–6 dB am VST; Note 84 bei v64 noch bis 9 dB dumpfer (unsere Sägezahn-h2 schwankt mit der Taste: −10/−6,7/−11,5 dB, VST konstant −8; offen). Bank 1: Median +0,6 dB.
- **Vibrato-Skala im VST (Michael, 03.09., `pd_50/100.mp3`, nur Upper P1, LFO-1 Rate 68):** Ridge-Tracking der Grundwelle: Tiefe 50 → **±139 ct** (wir ±147 aus `kPModCurve[50]=0,252·600`), Tiefe 100 → **±583 ct** (wir ±585), Dreieckform in beiden. **Die 600-ct-Vollskala und die ROM-Kurve 0x17F4 sind damit bestätigt** — die frühere Vermutung „Vollskala zu groß" ist zurückgezogen. LFO-1-Rate Byte 68 im VST **2,65 Hz** (Spektrum der Cent-Spur), bei uns 3,05 (Firmware-Gesetz) — die Arco-Phrase aus #142 (ebenfalls Roland-Plugin, ältere Version) zeigte 3,1 Hz — zwei Plugin-Versionen widersprechen sich, **keine Hardware-Messung vorhanden**; unser Firmware-Gesetz bleibt, bis ein echtes Gerät misst. Rest-Rätsel: bei Tiefe 2 zeigt das VST < 0,3 ct, die Kurve sagt 4,7 ct (Wert 1/127); vermutlich Totzone am unteren Ende, Wirkung ≤ 5 ct, offen, nur mit Tiefe 5/10/20-Aufnahmen entscheidbar.
- **Was der VST-Vergleich sonst noch sagt:** Fine ±5 ct bestätigt (Linienpaar), Hüllkurve ab 30 ms auf 1–3 dB, Velocity-Sprung 4,0/4,1 dB. **Offen:** (a) ~~P-Mod-Vollskala~~ bestätigt (±583 ct bei 100), nur die Totzone bei Tiefe 2 offen, (b) T1 bei Vel 64 zu langsam (145 ms gegen ~30 ms), (c) ~~Pulsweite < 50~~ gelöst (§3 Pulsweite, VST), (d) Keyfollow-Drift auf hohen Tasten.

### LFO (fertig, aus IC25 + EPROM bewiesen)
- Rate: `2^(k/10)`, firmware-reiner Anker (D-05-Tabellen-Top 27,9847 Hz ⇒ Tick 111,94 Hz ≈ `kTickHz=112`). Byte 74 = **4,62 Hz** (nicht mehr 5,6).
- Delay zweiphasig: Stille `1024·2^((d−100)/10)` Ticks, dann Fade per LUT. **Fade wirkt nur auf die stehende Tiefe** — Hebel/Aftertouch sprechen sofort.
- **Die drei LFOs sind ton-global** (IC25 0x1508–0x160D): Der 112-Hz-Tick schiebt genau 6 LFOs (3 je Ton; Basis UP 0xC499 / LP 0xC559, Block-Stride 4, ein Phase-Wort je LFO) — nicht einen pro Stimme. Ein Akkord vibriert kohärent, eine Legato-Note tritt in das laufende Wobble ein. Engine: `Tone` besitzt `lfo_[3]` und schiebt sie pro Sample auch in Stille (Tick läuft unbedingt); Stimmen lesen nur (`bind_lfos`, `value()/gate()`); Standalone-Tests laufen über lokale Fallback-Kopien (`local_lfo_`).
- **Sync-Rollen** (Note-Übergangs-Handler EPROM 0x28FC–0x2991):
  - **Aus der Stille klingend werdend** (FE70==0 & FE72≠0 …): CALL 164C/1641 → Schleife 0x1655 resettet **jeden** LFO mit Sync-Byte ≠ 0 (Phase + Delay).
  - **Mitten in der Phrase:** KEY-Retrigger **nur für LFO-1** und nur wenn dessen Byte == 2 ist (Gates 0x2929/0x294E/0x2981 lesen ausschließlich C49C/C55C → CALL 1610/162C → 0x1729). Ein Byte 2 auf LFO-2/3 wirkt wie ON.
  - **Sync OFF (0):** freier Lauf, nie ein Reset; Delay nur einmal nach Patch-Load.
- Bank-Scan c[25..36] bestätigt: KEY (2) kommt nur auf c[28] vor — c[32]/c[36] tragen nie 2 (KEY-Nutzer: Nr. 5, 29, 31, 32, 37, 40, 44, 48, 51, 57, 59, 61). Sync ≠ 0 verteilt sich auf c[28] (25×), c[32] (5×), c[36] (16×).
- Vorherige Engine-Fehler behoben: Sync-1/Delay lief bei **jedem** note_on neu (auch Legato), Sync-0 startete sogar sein Delay neu.
- Unit-Test `lfo.cpp` (Scratchpad, 13/13, am Zustand via `lfo_phase/lfo_gate` gemessen — nicht am Audio): Sync 0 kein Reset; Sync 1 Reset aus Stille, Legato joined laufenden LFO, neue Phrase resettet wieder; Sync 2 Legato resettet nur LFO-1; Byte 2 auf LFO-2 = ON-Verhalten.

### Sägezahn-Oktave (13./14.08., endgültig geklärt — die D-50 kompensiert NICHT)
- **Der Wavegen verdoppelt den Sägezahn** (Saw = Square ⊗ Cosinus ⇒ Ring-Kamm trägt nur gerade Harmonische der Basis; munt LA32WaveGenerator, Chip-Eigenschaft). **Der MT-32 kompensiert das in seiner Control-ROM** (munt TVP: Saw-Base 4096 unter Square) — **die D-50-Firmware nicht**: Pitchkonstante = f(coarse, fine, Ton-Fine), kein Wellenform-Read im Pitch-Pfad (siehe Pitch-Gesetz oben).
- **Capture-Beweis:** `WaveSQU.mp3` liegt auf **262 Hz**, `WaveSAW.mp3` auf **524 Hz** bei derselben gespielten Taste — der echte D-50-Saw klingt exakt eine Oktave ÜBER dem Square gleicher Einstellung.
- **Die Bank ist darauf geschrieben:** Squares liegen bei Unisono-Schichten systematisch eine Coarse-Oktave ÜBER dem Saw (Metal Harp 36/48, Slap Brass 48/24, Ethnic Session 0/24), und das Saw-Coarse-Histogramm sitzt bankweit eine Oktave unter dem der Squares (Modus 24/12/0 vs. 36/24/48).
- Konsequenz: die Ring-Mod-Konstruktion OHNE Oktav-Korrektur ist das D-50-Verhalten. Die Halbierung aus `a821e53` (MT-32-Lesart) war für die D-50 **falsch** und ließ jede Saw-Schicht eine Oktave unter dem Original liegen → Michaels „zu tief" an 37/44/45/46. **Reverted in `014da1d`.**
- tune2-Caveat bleibt: das Urteil faltet Oktaven — für Oktav-Fragen nur `peaks`/`winscan` mit Absolutfrequenz.
- Konsequenz für die Bank: jeder Saw-Partial sitzt jetzt auf dem belegten Rank statt eine Oktave drüber — das ist der größte Einzelteil hinter „größtenteils nicht original".
- ~~Bewusst unberührt: TVF-Pfade~~ — **seit 03.09.2026 ist die Cutoff-Basis aus IC25 bewiesen** (§3 TVF-Cutoff-Basis); TVA unverändert.

### YouTube-Demo-Referenz (13.08., Vertrauenswürdigkeit entschieden)
- Das funami-Video (`l7RLZpYrVzE`, Raster 8,5 s + 9,25 s/Preset) spielt **nicht die Werksbank** — Spektral-DNA Pos 22: Vollkamm + Terz-Rank 2,52×f0 (Orgel-Mixtur), aus den Factory-Bytes Pipe Solo nicht erzeugbar (zwei additive +12-Squares); Pos 24 zeigt dieselbe Mixtur-Gestalt. Drei Unabhängige Belege für unsere Byte-Lesart: Roland-MIDI-Chart, `36_PipeSolo.mp3` (odd-harmonic 883), Michaels Erinnerung.
- Zusätzlich: die Video-Held-Phasen sind systematisch **heller, als ein offener LA32-Sägezahn überhaupt klingen kann** (Rich Brass h2 −1,2 dB; Chip-Gesetz-Decke −8 dB) → das Material ist bearbeitet (Mastering-Kompression/EQ?) oder nicht werksseitig. **Als per-Patch-Wahrheit verworfen**; brauchbar bleiben Raster/Reihenfolge und grobe Timings. (Vgl. §5.)
- `bare_wave.cpp` (Scratchpad) rendert das Roh-Teiltonprofil eines einzelnen Synth-Partials — der schnelle Richter für Oszillator-Fragen ohne Filter-/Effekt-Konfund.

### DC-Abbau am Mischpunkt (aus dem Pipe-Solo-Vergleich, 13.08.)
- Asymmetrische Pulse tragen DC in Höhe des Duty-Ungleichgewichts: `dc = 2·pulse_frac − 1` (Kanten mitteln 0; bei `h_frac_=0`-Klemme `2·edge − 1`). Gemessen an Patch 36 (Duty ~5 %): **DC −0,07..−0,10**, Peaks asymmetrisch (−0,163/+0,064) → schob die Saturator-Kurve schief und fraß Headroom; Originalaufnahme zeigt nichts davon (analoge Koppelstufe).
- **Platzierung bewusst NICHT im Oszillator:** der Chip-Ring-Mod multipliziert die rohen Partials inklusive DC (munt-Lesart) → Abzug am Mischpunkt der Voice (`d5_voice.h`): direkte Partials werden DC-befreit, im Ring-Produkt fällt nur der reine `dc_a·dc_b`-Term raus — die Leck-Terme `dc_a·b` bleiben (niveaumodulierte Kopie des anderen Partials, die Koppelung lässt sie durch). Beim Sägezahn kein Abzug: die Form-Mitte reitet auf dem Cosinus-Träger (Mittelwert 0, trägt die Grundwelle).
- Bank-Befund: 122 Synth-Squares, 102 mit PW < 35 % oder > 75 % in **41/64 Patches** → das war Michaels „größtenteils nicht original". (Duty-Zahlen dort galten unter der alten Duty-Prozent-Lesart; unter dem korrigierten Pulsweiten-Gesetz tragen genau die 36 Partials mit PW > 50 DC — der Abzug bleibt richtig, nur Pulse über Byte 50 melden einen `dc_shape_` ≠ 0.)
- Nach dem Fix: DC ±0,000, Peaks symmetrisch; Suite komplett grün.

### Key Shift
Wandert in den **Keyfollow-Multiplikanden** (vor der Multiplikation), Faltung bei ±48 oktavweise — nicht mehr auf `coarse`.

### Pulsweite — Chip-Gesetz aus Rolands D-50-VST (03.09.2026, ersetzt die munt-Lesung darunter)
- **Messung (Michael, `sqr_pw0/25/50/75/100.mp3`, nur Upper P1 als SQU, trocken):** Nullstellen bei h4 (PW 25), h8 (PW 50), h16 (PW 75), PW 100 ≈ PW 75 ⇒ **Duty = 0,5·2^(−PW/25), Boden 1/16**; PW 0 = 50 % (h2 −68 dB). In Registereinheiten (T[k] = 2,55·k, Firmware schreibt sie ohne Offset ins Chip-Register, 0x07E6–0x0805/0x072A): `duty = max(1/16, 0,5·2^(−reg/64))` — munts Exponent (Halbierung je 64), aber **ab Register 0, nicht ab 128**. Munts Tor „≤ 128 symmetrisch" gilt für die D-50 nicht (Handbuch S. 35 zeichnet Wert 50 asymmetrisch). Eingebaut in `d5_synth_voice.h` (`pulse_frac_`), Test `tools/host_tests/d5/pulse_width_host_test.cpp`.
- **Folgen:** die 56 Bank-1-Partials mit PW 1..50 sind erstmals asymmetrisch (PW 33 → 20 %, 37 → 18 %, Stereo Polysynth PW 15 → 33 %); die 77 mit PW 0 (Pipe Solo!) und alles über 50 unverändert bis auf den 1/16-Boden. Der DC-Abbau am Mischpunkt greift jetzt auf allen asymmetrischen Pulsen. **Modellgrenze:** bei tiefem Cutoff klemmt unser Puls an der Flankenbreite (Cutoff 50 ⇒ 16 %), das VST zeigt bei den Aufnahmen (Cutoff 90) keine Klemme — ob der Chip bei tiefem Cutoff auch klemmt, ist offen.

### Pulsweite (ÜBERHOLT durch den Abschnitt darüber; Lesung vom 13.08.)
- **Die ROM-Lesung ist linear:** Scaler 0x02EC bildet das Panel-Byte per `T[k]=round(2,55·k)` auf 0..255 (T[0]=0, T[50]=128, T[100]=255, byte-gedumpt). Die Chip-Lesart (munt LA32FloatWaveGenerator): `pulseLen = 0,5` für werte ≤ 128 (ein **ehrliches Quadrat**), exponentielle Verengung darüber (`2^((64−pw)/64)`, Byte 100 → Duty ≈ 0,126).
- **Die alte Engine-Lesart (Duty = Byte %) war invertiert:** Byte 0 wurde zum 5-%-Nadelpuls — Grundton ~22 dB unter dem eines Squares gleichen Pegels. Das war Michaels „Flötenton liegt weiter hinten" (Pipe Solo trägt PW 0 auf drei Squares); der Flöten-Rank (Odd-Harmonic-Hohlklang) kollabierte unter den Underton.
- **Referenzbelege:** Pipe-Solo-Referenz (Byte 0) hält bei 883 Hz einen **odd-harmonic**-Rank ohne h2, h3 bei −16,4 dB — mit Nadelpuls läge h2 **über** h1 (asymptotisch +6 dB); WaveSQU.mp3 zeigt duty 50 % exakt (h2/h4 abwesend, h3 −12…−16 dB).
- **Bank-Verteilung:** 77 Squares mit PW 0, 56 mit PW 1..50 (alles dieselbe Fläche), **36 mit PW > 50** in 14 Patches — darunter Soundtrack (4× PW 82, pw_velo +7), Rock Organ, Tine Wave, Intruder FX, Future Pad. Die Kontraktionszone ist also real belegt, und der DC-Befund oben lebte aus ihr (alte Lesart: DC +0,64 bei 82 %).
- **PW-Velocity** addiert `(vel−64)·(p9−7)` auf den 0..255-Wert (munt Partial.cpp) — Pizzagogo trägt p9=7 (neutral).

### Portamento (fertig, aus IC25 bewiesen)
- **Slew-Routine** IC25 `0x1866`, gerufen vom 112-Hz-Timer (Vektor 0x2018 → 0x27F0). Pro Partial-Slot (32 Slots, B step 2): Schritt = **4·T[rate]/256 Halbtöne je Tick** (`MOV A,18E3H[A]; SHLW RP0,2; ADDW/SUBW RP3,RP0`), Snap bei Überschwingen.
- **Tabelle 0x18E3 byte-exakt** als `kPortaRate[101]`; Steigung = 1,75·T[time] Halbtöne/s, umgelegt auf den Mod-Block: `T·0,056/64` st/Block. Unit-Test `glide.cpp` bestätigt das Gesetz auf drei Dezimalen (time 1→53 Blöcke, time 100→13716 Blöcke).
- **Glide ist „immer an"**, wenn Switch+Time>0: das Pitch-Word CB20 überlebt Note-off und konvergiert weiter; die nächste Note gleitet aus der letzten Ruheposition — kein reines Legato. Entsprechung in der Engine: `glide_pos_`/`glide_tgt_` überleben `note_on`.
- **Snap-Regeln:** Rate-Byte 0 → Note-On-Pfad (0x05B4–05D1) snappt direkt. Switch FE33 Bit 0 aus → Snap aller Slots je Tick. Engine-Variante: CC65 mitten im Glide snappt aufs Ziel.
- **Per-Tone-Modus:** pb[20] (0=Upper, 1=Lower, 2=beide) aus der MIDI-Chart, Firmware-Spiegel C5C6/C5C8.0; Zeit ist patch-common (FE01/FE09, beide Tones gleich). CC5=Time, CC65=Switch; Patchwechsel beendet den CC-Override (Spec ist wieder Maßstab).
- **Bewusste Abweichung:** eine noch nie benutzte Voice würde in der Firmware aus CB20=0 gleiten; unsere Engine snappt bei kalter Voice (`glide_warm_`) — zur Disposition dokumentiert.
- Bank-Scan: alle 64 Patches haben Switch=0 → kein Regressionsrisiko.

### Aftertouch (fertig, aus dem Bank-Code + IC25 bewiesen)
- **Weg:** Channel Pressure 0xD0 → Dispatcher eprom_hi 0x4CAE → Handler 0x4D02 → Rohbyte D332, Spiegel D313 / FE03 (Upper) / FE0B (Lower); Change-Flags FE4A.0/.2, Two-Phase-Commit. Verdrahtung: Core `channelPressure()`-Virtual → `midi_serial` (case 0xD0) + `midi_input_usb` (CIN 0xD) → `pf_at` → `D5_Midi::onChannelPressure` (accepts-Gate) → `Bridge::setAftertouch` → `Patch/Tone/Voice::set_aftertouch`. AT überlebt den Patchwechsel (Performance-Controller wie das Rad, FE03/FE0B sind Spiegel).
- **P-Mod-AT (c24):** zweiter Hebel neben CC1 — `kPModCurve[c24]·AT` additiv in die Vibrato-Tiefe (Merge 0x1552–0x158E, Clamp 0x0FFF), **umgeht den LFO-Fade** genau wie der Hebel. Gate je Partial = Lever-Gate (A&L-Modus lebt davon: Living Calliope).
- **Per-Partial-AT-Ranges ±7** (p12=PW, p34=TVF, p53=TVA), Chip-Transforms 0x10CE/0x113B/0x11A9 vom 112-Hz-Tick in die Chip-Regs E500..E520. Engine les-t: PW/TVF offsetten ihre Lanes um ±(byte−7)/7·AT·0,65 Vollausschlag; TVA dämpft: s>0 ruht ~3 dB leise und steigt unter Druck, s<0 duckt (2|s| Chip-Einheiten à 0,376 dB ≈ 5,3 dB — **die Engine-Skalen 0,65/3 dB sind PLAUSIBLE, Hörtest ausstehend; Richtungen bewiesen**).
- **AT-Bend (pb27) exakt:** Halbtöne = `(pb27−12)·AT/128` auf jeder klingenden Voice (EPROM 0x5C34–0x5D1C: ±2·AT·|range| Einheiten à 1/256 st, Clamp ±0xC00 = ±12 st). Patch-common, neutral bei Byte 12.
- Unit-Test `press.cpp` (Scratchpad): Bend-Gesetz auf 3 Dezimalen gegen die Formel, TVA-Richtung ±3 dB, AT = Hebel per Differenztest, Gate-Probe.

### Bend-Mode (fertig, aus IC25 + Bank-Code bewiesen)
- **Per-Partial-Gate** p[5] (IC25 `0x0E4D: A&3, BZ` skippt): **0 = OFF** (Rad stumm), **1 = KF** — Skalierung mit dem **vorzeichenbehafteten** Pitch-Keyfollow (Tabelle `0x01F1`, Pfad `0x0E92`; `CMP A,#03` invertiert die Richtung für die negativen Keyfollows idx<3 — ein Partial, das die Tastatur abwärts läuft, biegt beim Rad-hoch auch abwärts), **2 = NORM** — konstant ×0x5555 = Vollausschlag (`0x0E57`). KF ist Fabrik-Default: 39/64 Patches tragen (1,1,1,1); OFF sitzt auf Drum-/Festton-Partialen (Nr. 10/42/56 ganz, 18 teils: (0,1,0,1)).
- **Engine:** `bend_scale[2]` pro Partial (0 / signetes `keyfollow` / 1); Bend wandert auf **Halbton-Basis** (`set_bend_semis`, Kette Voice←Tone←Patch←Bridge). Rad und AT-Bend teilen sich **eine** ±12-st-Klemme pro Voice (EPROM `0x5D1C`, ±0xC00 à 1/256 st) **vor** der per-Partial-Skalierung — KF-2 liest dieselbe gekappte Quelle wie OFF.
- **Bender Range pb[26]** (0–12 st, patch-common): Patch-Lader `0x5D60` kopiert C59A → FE04/FE0C; Merge `0x5CC1` MULU mit der Range; RPN0+CC6-Override (`0x4E72–0x4EA4`, Clamp 12) existiert und ist verdrahtet (CC100/101 + CC6, Patchwechsel beendet den Override — Porta-Muster). Bank-Scan pb[26]: {2:55, 12:7, 7:1, 6:1} → die alte harte 2,0 traf 55 von 64 nur zufällig; Patches mit 12: u.a. Nr. 1, 24, 35, 41, 45, 49.
- **Interessant fürs Ohr:** KF auf kf≠1-Partialen verdoppelt/halbiert das Bend (Nr. 20: (11,15) → P2 bendet doppelt; Nr. 22 LP1 kf=5 → 37,5 %); negative Keyfollow-Patches benden invertiert pro Partial.
- Unit-Test `bend.cpp` (Scratchpad, 11/11): NORM ±2/−12 st, OFF-Gate, KF ×2/×½/invertiert, Index-Verdrahtung auf Partial 2, gemeinsame ±12-Klemme Rad+AT und danach ×2, Neutralpunkt bei KF −1.

### Stereo-Bild & Effekte (13.08. spät, Antwort auf „Parts verschmelzen nicht")

- **Befund:** Die Engine war komplett mono — `Patch::next()` gab einen Float, Bridge schrieb L=R identisch. Michaels Pipe-Solo-Beobachtung („im MP3 verschmelzen die Parts, bei uns bleiben Einzelparts erkennbar") ist genau das: Der D-50 bekommt seine Breite aus dem Effekt-Chip, und ohne die verschmilzt nichts.
- **Chorus — Roland-Stereoschema:** links `dry + wet`, rechts `dry − wet`, **dasselbe** modulierte Wet, phaseninvertiert (Schema der Roland-Outboards der Ära, SDD-320/Dimension-D-Linie). Erste Variante (gegenläufige Sweeps links/rechts, Wet in-phase) ergab bei Werks-Bytes praktisch Mono: `kDepthCurve` macht die Depth winzig (Byte 48 → ±0,13 ms), die Differenz zweier kaum bewegter Reads ist ~nichts. Bei Anti-Phase ist das Seitensignal `wet·balance` in voller Höhe — auch statisches Delay trägt Breite.
- **Reverb — pro Seite ein Netzwerk:** zwei koprime Comb/Allpass-Bänke (`kComb[2][4]`, `kAll[2][2]`), jede vom eigenen Stereo-Eingang gespeist. Lag der eigentliche Breiten-Killer des ersten Entwurfs: die Töne mischten in **einen** Mono-Bus vor dem Reverb — die Chorus-Anti-Phase faltete dort weg, bevor der Raum sie je sah. Jetzt: `reverb_.process(ul·uw + ll·lw, ur·uw + lr·lw, l, r)`.
- **Mono-Fold = L/MONO-Buchse:** alle `next()`/`process(float)` geben die **linke** Seite (dry+wet) — `(l+r)/2` würde das anti-phasige Wet auslöschen. So verhält sich auch das Orginal, wenn nur die L/MONO-Klinke gesteckt ist; Suite bleibt am alten Verhalten (der alte Mono-Chorus == neues L).
- **Status PLAUSIBLE nur:** Chorus/Reverb/EQ sitzen im Effekt-Chip (M8B7126), dessen Koeffizienten im Silizium liegen — die Firmware schweigt dazu, also greift hier die alte Regel „Hörtest ist Richter". Richtung und Schema stehen fest (Roland-Schema, Werks-Bytes als Tiefe), die absoluten Breiten-Gefühle muss Michael beurteilen.
- **Messung** (`render_stereo`, 32 kHz f32): Pipe Solo SS side **−37,5 dB** bei mid −24,6 (corr 0,97), Fantasia corr **0,28**, String Ensemble corr **0,10**, Tails voll dekorreliert (corr ≈ 0). Vor Umbau: corr 1,00 bankweit.
- Suite nach Umbau unverändert grün (tune2 62/64, stress 0 NaN, click2 bekannter Grenzfall, alle Unit-Tests OK), Commit `7ec4fb1`, UF2 Build 13.08. 23:05.

### EPROM-Seite 2 (Datei 0x8000–0xBFFF) — NEU GEFUNDEN 03.09.2026, nie disassembliert
- **Falle:** das Bank-Fenster CPU 0x8000–0xBFFF zeigt je nach P0-Oberbits eine von vier 16-KB-Seiten der EPROM-Datei. Bisher waren nur der feste Teil (Datei 0x2000–0x7FFF) und Seite 3 (0xC000–0xFFFF, UI-Text + PCM-Tabellen) gelesen. **Seite 2 = Effektchip und Mischer**, Seite 0 = UI/Edit-Code. Werkzeug: Hybrid-ROM `roms_pg2/` (Datei 0x8000–0xBFFF nach Image 0x2000 kopiert), Listing `rom/mame/pg2_cpu.asm` (CPU-Adressen = Datei-Offsets, Seite 2 liegt ohne Versatz).
- **Output Mode (Patch-Byte 29, 0 = Modus 1):** Lader 0x66BB kopiert C59D → CD99 und ruft 0xB4DD (Seite 2). Bank 1: Modus 2 auf **Jazz Guitar Duo, Stereo Polysynth, Picked Guitar Duo, Slap Bass n Brass, Pianissimo**; alle 384: 345×1, 37×2, 2×3. **Unsere Engine liest das Byte nicht.** Im VST hat Stereo Polysynth (kein Chorus, Small Hall 23) Seite = Mitte (Korrelation +0,06) — das ist der Output Mode 2, nicht der Hall.
- **Mischer 0xB4DD–0xB6A0:** Tests 0xB48F (Key-Mode Whole?) und 0xB49A (`CD99 == 0`); Pfad 0xB55A (Modus 1, nicht Whole): Slot-Reihenfolge 0xB4B3 `42 C2 3E BE 40 C0`, Zeilen 0xB4B9 `A4 A4 80 80 80 80` mit Tone-Balance-Gewichten aus 0xB5AF; Pfad 0xB4FC (Modus ≠ 1 oder Whole): je Ton drei Slots (Upper 0xC2/0xC0/0xBE, Lower 0x42/0x40/0x3E) mit Zeilen 0xB4A7 `FF 80 80` (Upper) / 0xB4AD `FF 00 FF` (Lower), Gewichte aus der **Chorus-Balance des Tons** (CD7D Upper / CD8D Lower, Routine 0xB5AF = Dry/Wet-Paar mit 50er-Knick). Hall-Sends 0xB627 (Slots 0xFC/0xFE, R6 = 100) und 0xB64C (Slots 0xEA/0x68/0x6A/0xE8, R6 aus Reverb-Balance CD9B: unter 50 Wet = 2·bal, darüber Dry = 100 − 2·(bal−50)) mit **Modus-Zeilen 0xB4C5 + 6·Modus**: M1 `80 80 | FF FF 00 00`, M2 identisch, M3 `00 FF | 00 80 80 00`, M4 `FF 00 | 80 00 00 80`. Gain-Kurven 0xA2E4 (u16, 0x1000 + ~20,5·i) und 0xA642, Slot-Wert = Kurve[(Zeilenbyte·R6)>>8].
- **DSP-Host-Interface:** Slots DD00+2n (und DC00+2n) werden bei 0xAE90 über 0xF800 (Adresse n) / 0xF801–0xF803 (Daten) in den Effektchip geschrieben. Slot n = Koeffizientenadresse: Lower 0x1F/0x20/0x21, Upper 0x5F/0x60/0x61, Hall 0x34/0x35/0x74/0x75/0x7E/0x7F. **Was die Koeffizienten im Chip bedeuten, steht nicht in der Firmware** (DSP-Programm im Masken-ROM) — Zuordnung nur per Konsistenz (M3/M4 sind Spiegelbilder) oder per VST-Messung.
- **Chorus-Typen: 8 Zeilen × 32 Bytes bei 0xA548** (Setup 0xB8D9 Upper / 0xB941 Lower über CD7A/CD8A = c42; Sonderfall Typ 6 (`CMP #5`) = Tremolo). Inhalt vermutlich Koeffizienten + LFO-Parameter (letzte 6 Bytes je Zeile: `00 1B 12 00 0B 03`, `00 06 04 00 05 15`, …) — noch nicht gedeutet. Reverb-Typ CD9A: Leser auf Seite 2 nur über CD9B gefunden; die Typ-Tabelle (188 Koeffizienten je Typ) wahrscheinlich auf Seite 2 oder 0 — suchen.
- **Messung an Michaels Polysynth-Aufnahme (Modus 2, kein Chorus, Hall 23), Partial-Linien einzeln (0,03-Hz-FFT):** Upper P1 (+6 ct) und P2 (−3 ct) liegen **rechts** (L−R −12…−20 dB), Lower P2 (−15 ct) liegt **links** (+15…+19 dB), Lower P1 (−6 ct) überwiegend rechts (−4/−12/−28 dB an h1/h2/h3). Also keine saubere Ton-Aufteilung, eher je Partial — passt zu den Drei-Slot-Zeilen je Ton (Lower `FF 00 FF` = ein Slot aus), aber die Slot-Semantik (was ist L, R, Chorus-Send) ist damit noch nicht eindeutig. **Vor der Implementierung VST-Aufnahmen mit isolierten Tönen je Modus** (siehe Anfrage 03.09.).
- **Output Mode EINGEBAUT (03.09., PR #146 gemerged, Hörtest bestanden):** VST-Messung mit isolierten Tönen (`~/Downloads/poly/op{1..4}_r{0,50}_{upper,lower}.mp3`): Modus 2/3/4 trocken identisch — **Upper nur rechts, Lower nur links** (anderer Kanal digital still); Modus 1 beide mittig. Unterschied nur im Hall (Firmware-Zeilen + VST `op3_r50_upper/lower`): Modus 2 sendet beide Töne, Rücklauf beidseitig (Upper-Hall links −48 / rechts −41 dB); **Modus 3 hallt nur der Upper, Rücklauf nur rechts (links digital still), Lower trocken**; Modus 4 spiegelbildlich (Lower hallt links) — 3 = Upper bewiesen, 4 als Spiegel gefolgert. Engine: `PatchSpec::output_mode`, Routing in `Patch::next_stereo`, Mono-Ausgang in 2–4 = Summe. Die frühere Deutung „je Partial verteilt" war Leckage zweier 0,45 Hz benachbarter Linien (U2/L1) im Fenster. Stereo Polysynth Korrelation 0,98 → 0,08 (VST 0,06).
- **Nächste Arbeitspakete daraus:** (1) ~~Output Mode~~ erledigt, (2) Chorus-Zeilen deuten und gegen VST-Aufnahmen (Balance 100, je Typ) legen, (3) Reverb-Tabelle finden. Michaels Polysynth-Aufnahme (`Polysynth_C4.mp3`) ist die Referenz für Modus 2.

### Chorus — kalibriert am VST (03.09.2026, PR #147, Hörtest bestanden nach der Hub-Korrektur)
- **Aufnahmen (Michael):** `arco_chorus_dry_typ1_typ6.mp3` (Typ 1 und Typ 6, Rate 50/Tiefe 50, Balance 100), `typ1_tiefe_0_100.mp3`, `typ1_tiefe100_rate0_100.mp3`; Arco Upper P1 allein, Cutoff 90, Env 0, Reverb 0; trockene Referenz = `co_90`. **Messmethode, die funktioniert:** Bandpass 200–330 Hz um h1, Hilbert-Momentanfrequenz, Median 5 ms, Rate per Autokorrelation, Hub = (pk-pk/2)/(2π·Rate) — Kreuzkorrelation mit der trockenen Note ist an einer periodischen Note mehrdeutig, Ridge-Tracker springen zwischen den Wet-Stimmen, Spektral-Autokorrelation greift Bessel-Linien.
- **Befunde:** Tiefe 0 ⇒ **L = −R exakt** (Korrelation −1,00, statische Verzögerung, keine Modulation). Rate 50 ⇒ **1,3–1,6 Hz**, Rate 100 ⇒ **7,4 Hz**, Rate 0 ⇒ ~0,5 Hz (wenige Zyklen im Fenster). Hub: Tiefe 50 ⇒ **±1,1–2,1 ms**, Tiefe 100 ⇒ **±2,4 ms**. **KORREKTUR:** die erste Lesung (±4–6 / ±10,5 ms) kam aus Perzentilen der Momentanfrequenz, die die Spitzen an den Auslöschungsmomenten des Sweeps mitzählen — vierfach zu groß, Michaels Bienenschwarm auf Arco Strings. Verlässlich ist der Effektivwert der Spur ohne die leisesten 30 % (am eigenen Render geprüft: 10,25 gemessen für 10,5 gebaut). Mit Tiefe laufen L und R **verschieden moduliert** (FM-Korrelation −0,16 … −0,64, L/R-Korrelation +0,20 … −0,02). **Typ 6 = Tremolo** (Handbuch S. 29: 6 Tremolo, 7 Chorus Tremolo, 8 Dimension — unsere alte Typentabelle hatte die Namen falsch): AM ≈ 15 dB bei Tiefe 50, **2,65 Hz** bei Rate 50 (≈ 2× LFO), gegenphasig L/R, kein Pitch.
- **Alt vs neu:** Rate 0,098–20 Hz → **0,28·26^(k/100)** (0,28/1,43/7,3 Hz); Hub `kDepthCurve·4 ms` (0,125 ms bei 50!) → **linear 2,4 ms·k/100**; ein Wet ±0,7 → **zwei Reads, rechter Sweep 0,3 Umdrehung versetzt, rechte Seite exakt invertiert**; Typ 6/7 mit Tremolo (m = 1,6·Tiefe, 2× LFO); Typentabelle nach Handbuchnamen (1 und 6 gemessen, Rest PLAUSIBLE). **Reverb bekommt einen eigenen Mono-Send** (`process(send, xl, xr, l, r)`, Send = Summe der L/MONO-Signale der Töne mit Balance-Gewichten; in den Output-Modi entsprechend) — die L+R-Faltung entfällt, damit ist die exakte Inversion ohne den 18-Patches-Hall-Ausfall möglich. UI-Brücke und `patch_map` lesen die Chorus-Tiefe jetzt linear.
- **Kontrolle am eigenen Render (gleiche Methode):** Rate 1,45/0,40/7,3 Hz, Hub ±1,22 (Tiefe 50) / ±2,41 ms (Tiefe 100), Tiefe 0 Korrelation −1,00, L/R-Korrelation +0,06 … +0,11, Typ 6 AM 12,8 dB @ 2,5 Hz. Bank: 384 endlich, keiner auf Vollaussteuerung. **Hörbarkeit:** Chorus-Patches werden breiter und stärker moduliert als vorher (String Ensemble 53–58 ⇒ ±1,3 ms statt ±0,15 ms) — Hörtest entscheidet; der 10,5-ms-Zwischenstand war der Bienenschwarm.

### Reverb — kalibriert am VST (03.09.2026, PR #148 gemerged, Hörtest bestanden)
- **Aufnahmen (Michael):** je eine Note durch 14 Reverb-Typen bei Balance 100 (`rev/*.f32` im Scratchpad `142/`: smallhall, mediumhall, largehall, chapel, box, smallmetalroom, smallroom, mediumroom, mediumlargeroom, largeroom, crossdelay (180), shortgate, delay248, crossdelay252) plus `reference.mp3` = die trockene Quelle. **Die Quelle ist kein Klick:** ~1 s gehalten, dann **55 dB/s Release**. Alles, was langsamer fällt, ist Hall; Box, Small Metal Room, Small Room, Medium Room und Short Gate liegen **unter** dem Quellenabfall ⇒ nur Obergrenze ≈ 1 s. Hüllkurven-Lesung (100-ms-Fenster, relativ zum Peak) ist der ehrliche Richter — Schroeder-Fits ab Onset messen die Quelle mit, Kreuzkorrelation an der periodischen Note ist mehrdeutig (Aliasing im 23-ms-Raster).
- **Befunde:** Small Hall 1,5 s · Medium Hall 2,9 · Large Hall 3,3 · Chapel 6,5 · ML Room 2,0 · **Large Room 2,1 mit L = −R (Korrelation −0,95)** · Hallen sonst Korrelation ≈ 0. **Delays:** rechts die Direktkopie, links der Tap (rms-Verhältnis R/L 3,2 / 2,0 / 2,2 für 180 / 248 / 252 ms), **Delay 248 links invertiert**, Cross 252 und 180 gleichphasig; Fahnen 2,7 s (248) und 2,4 s (252), Cross 180 unter der Quelle.
- **Engine:** `set_feedback()` (Kalibrier-Setter) + Kennlinie Feedback → T60 je Boss-Modus (Hall: 0,38→1,35, 0,50→2,87, 0,52→3,47, 0,56→5,8, 0,58→8,5; Room: 0,46→1,72, 0,48→1,99; Plate: 0,50→0,95). **Stabilitätsgrenze fb 0,625** (Comb: `y = filt·y₋₁ − x − fb·y₋N`, Gleichstromverstärkung fb/(1−0,375)). Neue Felder `echo` (Verstärkung + Vorzeichen des linken Taps) und `pol_r` (Polarität der rechten Nass-Seite; bei Boss-Modi bekommt dann R dasselbe Wet wie L, sonst bliebe die Korrelation 0). Delay-`wet` 2,5 → 1,2 (die Direktkopie rechts sitzt damit auf Hallpegel, −3 dB re Send bei Balance 1). Ergebnis über alle 32 Typen (`142/rev_verify.cpp`): 1,41 / 2,87 / 3,30 / 6,92 / 0,91 / 1,98 / 1,99 (corr −1,00) / Delays 2,74 / 2,43, R/L 2,0–2,9.
- **Zwei Defekte dabei gefunden:** (1) `configure()` verglich den **nullbasierten** Typ mit den Panel-Nummern 17/18 — **Bright Hall (Zeile 16) bekam die Höhlendämpfung ×1,25 und klingelte mit fb 0,5312 ewig bei 140 Hz** (−49 dB, Dauerton in der Stille); Large Cave (Zeile 17) hat mit ×1,25 seine Grenze bei fb 0,53 und steht jetzt auf 0,46 = 4,4 s. (2) Ein 0-ms-Tap las `at(0)` = nach `next()` das **älteste** Wort der Leitung (0,5 s) — beide Taps +1.
- **Zählfalle, zweimal getappt:** `ReverbSpec::type` ist **nullbasiert** (pb30 direkt, Display +1; sieben Werkspatches tragen 0 = Small Hall). Sonden mit Panel-Nummern messen die Nachbarzeile — die erste Kennlinie dieser Session lief mit dem Plate als „Room“ und war Unsinn. Stereo Polysynth pb30 = 0 = Small Hall, Arco Strings pb30 = 1 = Medium Hall, Living Calliope 22 = Cross Delay 252, Legato Strings 19 = Delay 248, Griitttarr 12 = Cross Delay 224 (die ältere Notiz „Griitttarr → 12 Cross 180“ zählte einsbasiert).
- **Offen:** Balance-50-Aufnahme (Mischgesetz) fehlt weiterhin; Box/Small Metal/Small Room/Medium Room/Gates nur nach oben begrenzt; Bright Hall, Cave, Steel Pan, Twisted Space, Space, Reverse Gates ohne VST-Messung (Werte PLAUSIBLE). Hörtest-Kandidaten: Cathedral Organ 1-24 / Pizzagogo 1-28 / Staccato Heaven 1-41 (Chapel, doppelt so lang), Fantasia 1-01 / Arco Strings 1-04 (Medium Hall, deutlich kürzer), Legato Strings 1-44 / Living Calliope 1-06 (Echo beginnt rechts), Panel-Typ 17 (kein Dauerton mehr).

### Restpatches: Aftertouch, LFO-Formen, Attack, Velocity-Decke, Pulspegel, Chip-Null (03./04.09.2026, PR #155 gemerged, Hörtest bestanden)
- **Verfahren (`probe_rest.py`):** die 20 Patches > 6 dB nach #154 je Partial isoliert, abweichende Partials per Byte-Gruppen-Bisektion; dominanter Term war die Gruppe 51–53 (TVA-LFO-Select/-Tiefe/**Aftertouch-Bereich**), zweiter die TVA-Hüllkurve perkussiver Patches. Danach Einzelgesetze mit `probe_at.py`/`probe_at2.py` (VST-Parameter `after_touch`, `render_bytes` mit AT-Argument), `probe_lfo3.py`/`probe_trem*.py`, `probe_att*.py`, `probe_seg.py`, `probe_level.py`.
- **TVA-Aftertouch quadratisch:** Dämpfung 0,755 dB·u² (u = Bereich − 7, = 2·u² Chip-Einheiten); positiver Bereich ruht voll gedämpft (10: −6,8 dB, 14: −37 dB!), Druck hebt linear (64 halbiert); negativer ruht neutral, Druck senkt. Unsere „~3 dB“-Lesung der ROM-Transformation 0x11A9 war eine Größenordnung daneben (Taj Mahal, Harmonic E-Piano, Tines). TVF-AT-Skala 0,65 → 0,85 (Bereich 14, Druck 127: Zentroid 583 → 1018 Hz; bei uns 961, die Decke 218 klemmt; Bereich 10 exakt 801). PW-AT stimmte (Tastverhältnis 0,340/0,229/0,198/0,101 auf 0,02).
- **LFO-Formen (Pitch-Route, Rate 40, Sync 1):** Dreieck startet am **Gipfel** und fällt (unseres startete im Tal), Sägezahn fällt, Rechteck ±0,5, Zufall ±0,5 mit Neuziehung je **Halbperiode**. Freilaufende LFOs starten bei uns jetzt bei Phase 0,5 (Tal): das Rate-0-Tremolo der VST steht direkt nach Patch-Load offen — Ham and Organ, Good and Old Days, Slap Bass n Brass laufen auf **LFO 3 mit Rate 0** (Sync 0) als statisches Tremolo, unsere Zufallsphase ließ sie 15 dB zu leise. TVA-Route: Select-Byte 1 ist unsere negative Route; mit einkopiertem Vorzeichen bleibt (1−l)/2. **LFO-Rate der VST ist konsistent ~16 % langsamer als unser Firmware-Gesetz** (Rate 40: 0,77 gegen 0,9 Hz; Rate 68: 2,65 gegen 3,05) — bleibt Firmware (D-05-Anker), notiert.
- **Attack ist eine Log-Rampe** (−20 dB bei ⅔ der Zeit, −6 dB bei 0,9; T1 60: 0,235/0,34/0,38 s), Dauer 0,53× unserer Firmware-Index-Lesung, Zielabhängigkeit halb so stark wie `law[Ziel]` (L1 50 ×1,2, L1 25 ×1,6 statt ×2/×4). Jetzt T1 40/50/60/70 → −1 dB bei 0,070/0,160/0,380/0,905 s (VST 0,070/0,160/0,380/0,885). Damit ist „T1 bei Velocity 64 zu langsam“ (§3 Arco) erledigt: die VST-Attacke klingt kürzer, weil sie unten lange leise bleibt. Velocity 64 = 127 bei Env-Velo 0 auf beiden Seiten.
- **PCM-Partials haben keine TVA-Modulation** (`probe_pcmmod.py`, `probe_pcmat.py`): TVA-LFO Tiefe 100 auf beiden Routen und Aftertouch-Bereich 14 mit und ohne Druck bewegen ein PCM-Partial in der VST um keine 0,1 dB; Pitch-LFO und Bias wirken. Wie beim TVF gehört der Modulationsblock zum Synth-Pfad. Ham and Organ und Good and Old Days (PCM-Orgeln mit Rate-0-Tremolo auf LFO 3) lagen darauf 15 dB unter der VST; die Sonden zu Startphase und Routen-Vorzeichen (`probe_sel.py`: Select 0/1/4/5, Sync 0/1) stimmen jetzt in allen sechs Fällen.
- **Wirkung (`sweep7_dry.csv`):** Streuung je Patch Std 4,2 (vor #154) → 3,2 (#154) → 2,95 (Runde 2) → **2,0 dB** (Runde 3); Patches > 6 dB 44 → 20 → 18 → **8**, > 3 dB 131 → 91 → 83 → **35**. Größte Reste: Tines 4-13 (+11, Ring-Struktur, isoliert nicht messbar), F-1 Grand Prix 6-59 (−9), PCM E-Piano 1-64 (+8), Breeze Pipe 5-36 (−7), Harmonic E-Piano 4-11 (−6), Slap Bass n Brass 1-51 (−6).
- **Dritte Runde (`probe_rest2.txt`, Bisektion der 18 mit neuer Engine; `probe_pwvel.py`, `probe_sawpw.py`, `probe_velo.py`, `probe_vcap.py`, `probe_fall*.py`, `probe_seg2.py`, `probe_ohit.py`):** (1) **Chip-Level deckelt bei 142**: Level 100 und 90 mit Velocity-Sens 100 landen bei Anschlag 127 beide auf +4,2 dB über Level-100-neutral, Level 80 bleibt 3,8 dB darunter; Bias wird vor der Decke abgezogen (Sonde: Decke-nach-Bias 118 Einheiten, VST 115); wir liefen bis 155 (+9 dB) — die konstanten −4,9 dB der Velocity-100-Partials. Velocity-Steigung nach unten stimmt schon auf 1–2 dB (VST: 0,30 dB je Anschlagsstufe bei Sens 100, neutral bei Anschlag 100). (2) **Rechteck behält beim Verengen seinen Pegel**: VST −15,9 → −16,4 dB von Tastverhältnis 0,5 bis zum 1/16-Boden, wir verloren 6,4 dB; Verstärkung (0,25/(d(1−d)))^0,47 auf dem Rechteckpfad mit dem effektiven Tastverhältnis max(Puls, Flanke); der Sägezahn ist beidseitig flach gegen die PW. PW-Velocity-Tastverhältnisse stimmten schon (0,206/0,218, 0,058/0,094). (3) **TVA-Segment auf Ziel 0 rampt zur Chip-Null (−37,6 dB) in seiner Dauer und läuft dann mit derselben Rate bis −90 dB weiter** (`Env5Spec::zero`, `coast_`): VST 48 → 0 bei T4 68 mit 25 dB/s, 100 → 0 mit 52 dB/s, 30 → 0 mit 15,5, alle geradlinig bis unter −80 dB; wir tauchten in derselben Zeit auf −60 und sprangen auf Stille. Orchestra-Hit- und Tines-Abfälle jetzt auf 2 dB über 3 s. **Die „T2-Rampenbegrenzung“ der vorigen Runde war ein Artefakt des linearen Attacks** — mit dem Log-Attack stimmt die ganze Tabelle (T2 0…40 × Ziele 80…10) auf 1–2 dB.
- **Entlastet:** TVA-Level p35, Sustain, Velocity p36 (exakt 0,376 dB/Einheit auf 0,1 dB), Abfälle auf 0 (T2 30/50/70), LFO-Delay, LFO-2/3-Auswahl. **Offen (klein):** Zufalls-Tremolo VST 1,0 dB gegen unsere 2,7; TVF-Aftertouch bei Bereich 14 und vollem Druck durch die Cutoff-Decke 218 auf 961 statt 1018 Hz; LFO-Rate der VST 16 % langsamer.
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
