Michi71/PicoVintageSynthCollection/instruments/PicoFaceCP/doc/PRESETS.md

# Factory presets

## Overview

The firmware provides **8 static factory presets**, which replaced the earlier
mdaEPiano programs (Default, Bright, Mellow, Autopan, Tremolo). Each preset
consists of:

- an **instrument** (Rd I, Rd II, Wr, Clv, Pno, CP),
- **12 engine parameters**, and
- the complete **FX chain setting** (drive -> trem/wah -> cho/pha -> delay ->
  reverb).

Tonal orientation: the _velvetkeys_ preset collection
(github.com/Michi71/velvetkeys). A deliberate deviation from the original Yamaha
reface CP, which has no presets at all.

---

## Selecting a preset

### (a) From the menu

1. **Long-press the selector** to open the menu.
2. Choose the **Presets** entry.
3. The encoder scrolls through P0…P7.
4. The preset is **applied immediately**.

### (b) MIDI program change

A **program change 0-7** selects the corresponding preset P0…P7; values >= 8 are
ignored. When a preset is picked from the menu, the firmware sends the matching
program change on the TX channel.

> **Note:** the original reface CP does not implement program change at all -
> this is the only preset-related MIDI deviation. **CC80 (TYPE) keeps its
> original meaning** and selects the instrument (6 zones) exactly as on the
> Yamaha device; picking an instrument on the VOICE screen still sends CC80.
> Program change is not gated by the MIDI control setting, only by the receive
> channel filter.

---
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
