Michi71/PicoVintageSynthCollection/instruments/PicoFaceDX/include/dx_engine/RDX_Constants.h

// SPDX-License-Identifier: GPL-3.0-or-later
// Ported from the RDX reface DX emulation for the ESP32; copyright is shared with
// its authors. See instruments/PicoFaceDX/README.md.

// RDX_Constants.h
#pragma once
#include <cstdint>
#include <array>
#include <cmath>
#include "ram_hot.h"
#include "misc.h"

constexpr float DIV_SAMPLE_RATE = 1.0f / (float)SAMPLE_RATE;
constexpr float DIV_DMA_BUFFER_LEN = 1.0f / (float)DMA_BUFFER_LEN;
constexpr float MIDI_NORM = 1.0f / 127.0f;

#define ONE_DIV_SQRT2 0.707106781f
#define ONE_DIV_SQRT3 0.577350269f

// ================== CONFIG ==================
#ifndef SINLUT_SIZE
#define SINLUT_SIZE 1024   // must be power of two
#endif
// ============================================


constexpr float AEG_LEVEL[192] = {
0.0000, 14.3579, 19.6135, 23.5395, 26.7929, 29.6230, 32.1559, 34.4656,
36.6001, 38.5923, 40.4662, 42.2395, 43.9262, 45.5372, 47.0814, 48.5661,
49.9972, 51.3800, 52.7187, 54.0171, 55.2784, 56.5055, 57.7009, 58.8667,
60.0050, 61.1174, 62.2057, 63.2712, 64.3151, 65.3388, 66.3432, 67.3294,
68.2982, 69.2506, 70.1871, 71.1087, 72.0159, 72.9093, 73.7895, 74.6571,
75.5125, 76.3563, 77.1888, 78.0105, 78.8217, 79.6228, 80.4143, 81.1963,
81.9692, 82.7333, 83.4889, 84.2362, 84.9755, 85.7070, 86.4309, 87.1476,
87.8571, 88.5596, 89.2554, 89.9447, 90.6275, 91.3041, 91.9747, 92.6393,
93.2982, 93.9514, 94.5991, 95.2414, 95.8785, 96.5104, 97.1373, 97.7593,
98.3766, 98.9891, 99.5970, 100.2004, 100.7995, 101.3941, 101.9846, 102.5709,
103.1532, 103.7314, 104.3058, 104.8763, 105.4430, 106.0060, 106.5654, 107.1213,
107.6736, 108.2225, 108.7680, 109.3102, 109.8491, 110.3848, 110.9174, 111.4468,
111.9732, 112.4966, 113.0170, 113.5345, 114.0491, 114.5610, 115.0700, 115.5763,
116.0799, 116.5809, 117.0792, 117.5749, 118.0681, 118.5588, 119.0471, 119.5329,
120.0163, 120.4973, 120.9760, 121.4524, 121.9265, 122.3984, 122.8680, 123.3355,
123.8008, 124.2640, 124.7251, 125.1842, 125.6411, 126.0961, 126.5490, 127.0000,
127.4490, 127.8961, 128.3413, 128.7847, 129.2261, 129.6658, 130.1036, 130.5396,
130.9738, 131.4063, 131.8371, 132.2661, 132.6935, 133.1192, 133.5432, 133.9656,
134.3864, 134.8055, 135.2231, 135.6391, 136.0535, 136.4664, 136.8778, 137.2877,
137.6961, 138.1030, 138.5085, 138.9125, 139.3151, 139.7162, 140.1160, 140.5144,
140.9114, 141.3070, 141.7013, 142.0942, 142.4859, 142.8762, 143.2652, 143.6529,
144.0394, 144.4246, 144.8085, 145.1912, 145.5727, 145.9529, 146.3320, 146.7098,
147.0865, 147.4620, 147.8363, 148.2095, 148.5815, 148.9524, 149.3221, 149.6908,
150.0583, 150.4248, 150.7901, 151.1544, 151.5176, 151.8797, 152.2408, 152.6009
};

//------------------------- GAIN --------------------------------------------


constexpr inline float mapLevel(float level) {
    // 48 dB range
    return powf(10.0f, -((127 - level) * 48.0f) / (20.0f * 127.0f)) - 0.003981071705533f; 

    // polynomial approximation
    float level2 = level * level;
    return (3.49752e-07f * level2 * level + 2.61634e-06f * level2 + 1.90001e-03f * level);
}

constexpr int LEVEL_LUT_SIZE = 192; // 0..191 inclusive

struct LevelLUT {
    std::array<float, LEVEL_LUT_SIZE> forward{};
    std::array<float, LEVEL_LUT_SIZE> inverse{};
    float maxValue{};
};

constexpr LevelLUT buildLevelLUT() {
    LevelLUT lut{};
    // forward
    for (int i = 0; i < LEVEL_LUT_SIZE; ++i) {
        lut.forward[i] = mapLevel((float)i);
    }
    lut.forward[0] = 0.0f; // not to deal with tiny floats like 1.21352465e-43
    lut.maxValue = lut.forward[LEVEL_LUT_SIZE - 1];

    // inverse
    for (int i = 0; i < LEVEL_LUT_SIZE; ++i) {
        float target = (lut.maxValue * i) / (LEVEL_LUT_SIZE - 1);

        int lo = 0, hi = LEVEL_LUT_SIZE - 1;
        while (hi - lo > 1) {
            int mid = (lo + hi) >> 1;
            if (lut.forward[mid] < target)
                lo = mid;
            else
                hi = mid;
        }
        float frac = (target - lut.forward[lo]) /
                     (lut.forward[hi] - lut.forward[lo] + 1e-12f);
        lut.inverse[i] = lo + frac * (hi - lo);
    }
    return lut;
}

// placed in RAM (.time_critical) — read every sample in audio IRQ, avoids XIP flash-cache jitter
inline const LevelLUT levelLUT __attribute__((section(".time_critical.levelLUT"))) = buildLevelLUT();
constexpr float LEVEL_LUT_MAX = buildLevelLUT().maxValue;

// ---- Accessors ----
inline __attribute__((always_inline)) float RAM_HOT(rdxGain)(float level) {
    int i = (int)level;
    float frac = level - i;
    return levelLUT.forward[i] +
           frac * (levelLUT.forward[i + 1] - levelLUT.forward[i]);
}

inline __attribute__((always_inline)) float RAM_HOT(rdxGainInv)(float value) {
    float scaled = value / LEVEL_LUT_MAX * (LEVEL_LUT_SIZE - 1);
    int i = (int)scaled;
    float frac = scaled - i;
    return levelLUT.inverse[i] +
           frac * (levelLUT.inverse[i + 1] - levelLUT.inverse[i]);
}



/*
constexpr float refaceGainFormula(int L) {
    return std::pow(10.0f, -((127 - L) * 48.0f) / (20.0f * 127.0f)) - 0.003981071705533f;
}

constexpr std::array<float, 192> makeRefaceGainTable() {
    std::array<float, 192> arr{};
    arr[0] = 0.0f;
    for (int i = 1; i < 192; ++i) {
        arr[i] = mapLevel(i);
    }
    return arr;
}

constexpr auto RDX_GAIN = makeRefaceGainTable();

inline __attribute__((always_inline)) constexpr float rdxGain(float L) {
   // return RDX_GAIN[(L >= 0 ? L : 0) & 127];
    int idx    = (int)L ;
    float frac = L - (float)idx;
    float s0   = RDX_GAIN[idx];
    return s0 + frac * (RDX_GAIN[(idx + 1) ] - s0);
}
*/


//----------------------- LFO SPEED ------------------------------

inline constexpr float LFO_SPEED[128] = {
    0.0263f, 0.0421f, 0.0841f, 0.1262f, 0.1682f, 0.2103f, 0.2524f, 0.2944f, 
    0.3364f, 0.3723f, 0.4120f, 0.4560f, 0.5047f, 0.5423f, 0.5827f, 0.6261f, 
    0.6728f, 0.7114f, 0.7523f, 0.7954f, 0.8411f, 0.8803f, 0.9213f, 0.9642f, 
    1.0091f, 1.0488f, 1.0901f, 1.1330f, 1.1776f, 1.2175f, 1.2588f, 1.3014f, 
    1.3455f, 1.3858f, 1.4273f, 1.4700f, 1.5140f, 1.5543f, 1.5956f, 1.6380f, 
    1.6815f, 1.7223f, 1.7640f, 1.8067f, 1.8505f, 1.8910f, 1.9323f, 1.9746f, 
    2.0178f, 2.0587f, 2.1006f, 2.1432f, 2.1867f, 2.2274f, 2.2689f, 2.3111f, 
    2.3540f, 2.3953f, 2.4372f, 2.4799f, 2.5233f, 2.5643f, 2.6060f, 2.6483f, 
    2.6914f, 2.7717f, 2.8545f, 2.9398f, 3.0276f, 3.1080f, 3.1906f, 3.2754f, 
    3.3625f, 3.4441f, 3.5277f, 3.6133f, 3.7010f, 3.8585f, 4.0228f, 4.1940f, 
    4.3725f, 4.5324f, 4.6981f, 4.8699f, 5.0480f, 5.2061f, 5.3693f, 5.5375f, 
    5.7110f, 6.0235f, 6.3530f, 6.7006f, 7.0671f, 7.3811f, 7.7089f, 8.0514f, 
    8.4090f, 8.7273f, 9.0575f, 9.4003f, 9.7561f, 10.2908f, 10.8548f, 11.4498f, 
    12.0773f, 12.7102f, 13.3762f, 14.0771f, 14.8148f, 15.4396f, 16.2486f, 17.1001f, 
    17.4764f, 18.5376f, 19.6633f, 20.8574f, 22.1239f, 23.3385f, 24.6198f, 25.9714f, 
    27.3973f, 28.9017f, 30.3030f, 31.6456f, 33.0033f, 34.3643f, 37.0370f, 39.6825f
};

//----------------------------- AM_DEPTH ------------------------------------
inline constexpr float AM_DEPTH[128] = { // 1/127 is closer )
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
    0.952707895, 0.958395414, 0.963759493, 0.968791661, 0.97348349, 0.977826568, 0.981812457, 0.985432627, 
    0.988678368, 0.991540653, 0.99400993, 0.99607578, 0.997726321, 0.998947018, 0.999717752, 1.0 
};
