Michi71/PicoVintageSynthCollection/instruments/PicoFaceJ6/src/juno/juno_presets.cpp

// SPDX-License-Identifier: GPL-3.0-or-later
// SPDX-FileCopyrightText: 2026 Michi71

/*
  juno_presets.cpp -- factory patch settings

  All 56 factory patches, transcribed from the chart on pages 25 to 28 of the
  Juno-60 owner's manual. That chart prints the complete front panel of every
  patch on the instrument's own 0..10 scale, and it settles what was previously
  imported from junox and believed to be unpublished.

  The transcription was checked against the imported set cell by cell. Of 720
  numeric cells across the 48 patches the two sets share, 590 agree exactly and
  the remaining 130 fall into four groups:

    125  junox truncated the half-steps. Wherever the chart says 6.5 it had 6.
         That is the bulk of what changes here.
      3  junox misread a digit: patch 33 pulse width 8 not 9, and both
         Pizzicato patches resonance 3 not 4. Re-read at high magnification.
      2  deliberate, and kept -- see below.

  Two further columns junox dropped altogether:

    The octave transpose. Every imported patch sat at 8'; the chart puts
    roughly twenty of them at 16' or 4', and it reads like an instrument list
    when it does -- both basses and both clavichords down, xylophone,
    glockenspiel, flute and the reeds up, tuba down.

    Bank 7, eight patches. The owner's manual explains why nobody reproduces
    them: "Bank 7 includes the patches whose sound sources are VCF self-
    oscillation." Their chart rows carry no waveform at all and resonance 10
    throughout, so they sound only if the filter really sings.

  The VCA level column is transcribed now, and it was the last one missing.
  It is printed as a signed value -- E or G for the ENV/GATE selector, then a
  number from -3 to +5 -- which is why earlier readings gave up on it: it is
  not a slider position but an offset from the middle of one. The slider is
  5 + LEVEL, so 0 is 0.5 and +5 is 1.0.

  junox has had it all along, and this note used to say the opposite. Against a
  higher-resolution scan of the chart, 32 of the 32 rows on the two pages that
  could be read match junox cell for cell under that mapping, over a range from
  -3 to +4 -- so junox's column is the chart's, and it is taken here wholesale.
  Hera (jpcima) carries the same column from junox.

  What it does: the bank's loudness spread narrows from 11.1 to 10.5 dB and its
  span from 51 to 48, the organs lose 3.7 dB and Glockenspiel gains 5.3. The
  headroom constant in juno.cpp carries the rest, since the column centres on
  0.5 where the placeholder sat at 0.7.

  Two values depart from the chart, both kept from a hardware listening test:

    Piano 1       DCO LFO 4.5 -> 0
    Clavichord 1  DCO LFO 4.0 -> 0
        The chart really does put vibrato on both. Neither instrument has any,
        and with the trigger mode on manual the LFO runs free rather than
        waiting for the button, so it is heard on every note. At the corrected
        modulation depth -- 3.9 semitones reached as the square of the
        setting -- it is 79 cents on the piano and 62 on the clavichord,
        which is still most of a semitone. Worth a listen before it is
        trusted either way.

  Two values that used to depart and no longer do. Brass was raised from 0.7
  to 1.0 by ear and Organ 3 likewise; the chart gives Brass +2 and all three
  organs 0, which is 0.7 and 0.5. Both are back on the chart's figures. The
  reasoning behind the Brass one still holds -- its level does rank above the
  strings, which sit at -2 -- it simply did not need the extra.

  One value is corrected rather than deviated from: Celesta's chorus is OFF.
  The chorus column sits at the page edge and the first scan could not resolve
  it, so it was taken from the Patch Book's LED graphics and came out as I.
  The better scan reads it directly, and it agrees with junox: off. That was
  the single cell where the two transcriptions disagreed, out of 1344.

  Each entry is a complete front panel, in the order of the enum in
  juno_params.h and grouped by the sections of the instrument. The macros make
  the grouping visible and, more usefully, make a miscounted row a compile
  error rather than a patch with a silently zeroed tail: LFO takes two
  arguments, DCO nine, HPF_ one, VCF six, VCA two, ENV four, CHOR one and SYS
  four, and together they expand to exactly JUNO_PARAM_COUNT values.

  Positions of rotary switches are written as R3(1) and so on -- the middle of
  the slot, so a value surviving a round trip through the per mille IPC or the
  settings record cannot land one position over.
*/

#include "juno/juno_presets.h"

/* Middle of slot i of an n-position switch. */
#define R2(i)  (((float) (i) + 0.5f) /  2.0f)
#define R3(i)  (((float) (i) + 0.5f) /  3.0f)
#define R4(i)  (((float) (i) + 0.5f) /  4.0f)
#define R5(i)  (((float) (i) + 0.5f) /  5.0f)
#define R8(i)  (((float) (i) + 0.5f) /  8.0f)

#define OFF 0.0f
#define ON  1.0f

/* Range switch. Every patch in the source set is at 8'. */
#define F16 R3(0)
#define F8  R3(1)
#define F4  R3(2)

/* Pulse width mode selector */
#define PWM_LFO R3(0)
#define PWM_MAN R3(1)
#define PWM_ENV R3(2)

#define VCA_ENV  R2(0)
#define VCA_GATE R2(1)

#define POL_NEG R2(0)
#define POL_POS R2(1)

#define CH_OFF R4(0)
#define CH_I   R4(1)
#define CH_II  R4(2)
#define CH_III R4(3)

#define TRIG_AUTO R2(0)
#define TRIG_MAN  R2(1)

#define OCT0  R5(2)
#define BEND2 R8(2)

#define LFO(rate, delay)  rate, delay

#define DCO(range, lfo, pwm, pwmMode, saw, pulse, sub, subLevel, noise) \
    range, lfo, pwm, pwmMode, saw, pulse, sub, subLevel, noise

#define HPF_(pos) pos

#define VCF(freq, res, env, pol, lfo, kybd) freq, res, env, pol, lfo, kybd

#define VCA(level, mode) level, mode

#define ENV(a, d, s, r) a, d, s, r

#define CHOR(mode) mode

/* Tune always at the detent: a patch that arrives out of tune is a fault. */
#define SYS(trig, oct) 0.5f, BEND2, trig, oct

const JunoProgram junoPrograms[JUNO_NPROGRAMS] = {

{ "Strings 1", {
    LFO(0.600f, 0.000f),
    DCO(F8 , 0.000f, 0.000f, PWM_LFO,
        ON , OFF, OFF, 0.000f, 0.000f),
    HPF_(R4(0)),
    VCF(0.700f, 0.000f, 0.000f, POL_POS, 0.000f, 1.000f),
    VCA(0.500f, VCA_ENV),
    ENV(0.400f, 0.000f, 1.000f, 0.450f),
    CHOR(CH_I),
    SYS(TRIG_AUTO, OCT0) }},

{ "Strings 2", {
    LFO(0.400f, 0.000f),
    DCO(F8 , 0.000f, 0.600f, PWM_LFO,
        ON , ON , OFF, 0.000f, 0.000f),
    HPF_(R4(0)),
    VCF(0.700f, 0.000f, 0.000f, POL_POS, 0.000f, 1.000f),
    VCA(0.300f, VCA_ENV),
    ENV(0.400f, 0.000f, 1.000f, 0.450f),
    CHOR(CH_II),
    SYS(TRIG_AUTO, OCT0) }},

{ "Strings 3", {
    LFO(0.300f, 0.800f),
    DCO(F8 , 0.000f, 0.700f, PWM_LFO,
        ON , ON , ON , 1.000f, 0.000f),
    HPF_(R4(0)),
    VCF(0.500f, 0.000f, 0.000f, POL_POS, 0.000f, 1.000f),
    VCA(0.300f, VCA_ENV),
    ENV(0.300f, 0.000f, 1.000f, 0.600f),
    CHOR(CH_II),
    SYS(TRIG_MAN , OCT0) }},

{ "Organ 1", {
    LFO(0.200f, 0.800f),
    DCO(F8 , 0.000f, 0.500f, PWM_MAN,
        OFF, ON , ON , 1.000f, 0.000f),
    HPF_(R4(0)),
    VCF(0.400f, 0.600f, 0.450f, POL_POS, 0.000f, 1.000f),
    VCA(0.500f, VCA_GATE),
    ENV(0.000f, 0.000f, 0.000f, 0.000f),
    CHOR(CH_I),
    SYS(TRIG_AUTO, OCT0) }},

{ "Organ 2", {
    LFO(0.500f, 0.400f),
    DCO(F8 , 0.000f, 0.550f, PWM_LFO,
        OFF, ON , ON , 0.800f, 0.000f),
    HPF_(R4(0)),
    VCF(0.350f, 0.550f, 0.400f, POL_POS, 0.000f, 1.000f),
    VCA(0.500f, VCA_GATE),
    ENV(0.000f, 0.100f, 0.000f, 0.100f),
    CHOR(CH_I),
    SYS(TRIG_AUTO, OCT0) }},

{ "Organ 3", {
    LFO(0.500f, 0.400f),
    DCO(F4 , 0.000f, 0.550f, PWM_LFO,
        OFF, ON , ON , 0.800f, 0.000f),
    HPF_(R4(0)),
    VCF(0.350f, 0.550f, 0.350f, POL_POS, 0.000f, 1.000f),
    VCA(0.500f, VCA_GATE),
    ENV(0.000f, 0.100f, 0.000f, 0.100f),
    CHOR(CH_II),
    SYS(TRIG_AUTO, OCT0) }},

{ "Brass", {
    LFO(0.500f, 0.650f),
    DCO(F8 , 0.150f, 0.000f, PWM_MAN,
        ON , OFF, OFF, 0.000f, 0.000f),
    HPF_(R4(0)),
    VCF(0.000f, 0.000f, 0.850f, POL_POS, 0.000f, 0.400f),
    VCA(0.700f, VCA_ENV),
    ENV(0.250f, 0.400f, 0.600f, 0.200f),
    CHOR(CH_I),
    SYS(TRIG_AUTO, OCT0) }},

{ "Phase Brass", {
    LFO(0.600f, 0.000f),
    DCO(F8 , 0.000f, 1.000f, PWM_ENV,
        ON , ON , OFF, 1.000f, 0.000f),
    HPF_(R4(0)),
    VCF(0.300f, 0.100f, 0.550f, POL_POS, 0.000f, 1.000f),
    VCA(0.400f, VCA_GATE),
    ENV(0.200f, 0.400f, 0.400f, 0.300f),
    CHOR(CH_I),
    SYS(TRIG_AUTO, OCT0) }},

{ "Piano 1", {
    LFO(0.600f, 0.300f),
    DCO(F8 , 0.000f, 0.600f, PWM_MAN,
        OFF, ON , OFF, 0.000f, 0.000f),
    HPF_(R4(0)),
    VCF(0.100f, 0.000f, 0.700f, POL_POS, 0.000f, 0.400f),
    VCA(0.700f, VCA_ENV),
    ENV(0.000f, 0.800f, 0.150f, 0.300f),
    CHOR(CH_OFF),
    SYS(TRIG_MAN , OCT0) }},

{ "Piano 2", {
    LFO(0.400f, 0.000f),
    DCO(F4 , 0.000f, 0.400f, PWM_MAN,
        OFF, ON , ON , 0.450f, 0.000f),
    HPF_(R4(0)),
    VCF(0.350f, 0.000f, 0.250f, POL_POS, 0.200f, 0.800f),
    VCA(0.800f, VCA_ENV),
    ENV(0.000f, 0.750f, 0.000f, 0.350f),
    CHOR(CH_OFF),
    SYS(TRIG_AUTO, OCT0) }},

{ "Celesta", {
    LFO(0.350f, 0.600f),
    DCO(F8 , 0.000f, 0.500f, PWM_ENV,
        ON , ON , OFF, 1.000f, 0.000f),
    HPF_(R4(1)),
    VCF(0.350f, 0.800f, 0.000f, POL_POS, 0.000f, 1.000f),
    VCA(0.600f, VCA_ENV),
    ENV(0.000f, 0.650f, 0.200f, 0.550f),
    CHOR(CH_OFF),
    SYS(TRIG_AUTO, OCT0) }},

{ "Mellow Piano", {
    LFO(0.500f, 0.000f),
    DCO(F8 , 0.000f, 0.500f, PWM_MAN,
        OFF, ON , OFF, 1.000f, 0.000f),
    HPF_(R4(0)),
    VCF(0.300f, 0.000f, 0.250f, POL_POS, 0.100f, 0.900f),
    VCA(0.700f, VCA_ENV),
    ENV(0.100f, 0.750f, 0.200f, 0.850f),
    CHOR(CH_I),
    SYS(TRIG_MAN , OCT0) }},

{ "Harpsichord 1", {
    LFO(0.500f, 0.400f),
    DCO(F4 , 0.000f, 0.300f, PWM_MAN,
        OFF, ON , ON , 0.700f, 0.000f),
    HPF_(R4(1)),
    VCF(0.300f, 0.000f, 0.500f, POL_POS, 0.000f, 0.700f),
    VCA(0.400f, VCA_ENV),
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
    LFO(0.600f, 0.200f),
    DCO(F8 , 0.000f, 0.800f, PWM_MAN,
        ON , ON , OFF, 0.000f, 0.000f),
    HPF_(R4(0)),
    VCF(0.600f, 0.200f, 0.300f, POL_POS, 0.000f, 0.200f),
    VCA(0.300f, VCA_ENV),
    ENV(0.000f, 0.700f, 0.200f, 0.200f),
    CHOR(CH_I),
    SYS(TRIG_MAN , OCT0) }},

{ "Reed 1", {
    LFO(0.600f, 0.200f),
    DCO(F8 , 0.400f, 0.000f, PWM_MAN,
        OFF, ON , OFF, 0.000f, 0.000f),
    HPF_(R4(0)),
    VCF(0.100f, 0.600f, 0.700f, POL_POS, 0.000f, 0.500f),
    VCA(0.600f, VCA_GATE),
    ENV(0.000f, 0.850f, 0.500f, 0.100f),
    CHOR(CH_I),
    SYS(TRIG_MAN , OCT0) }},

{ "Popcorn", {
    LFO(0.000f, 0.000f),
    DCO(F4 , 0.000f, 0.000f, PWM_MAN,
        OFF, OFF, ON , 1.000f, 0.000f),
    HPF_(R4(1)),
    VCF(0.250f, 0.200f, 0.550f, POL_POS, 0.000f, 1.000f),
    VCA(0.800f, VCA_ENV),
    ENV(0.000f, 0.300f, 0.200f, 0.000f),
    CHOR(CH_OFF),
    SYS(TRIG_AUTO, OCT0) }},

{ "Reed 2", {
    LFO(0.300f, 0.800f),
    DCO(F4 , 0.000f, 0.000f, PWM_MAN,
        OFF, OFF, ON , 1.000f, 0.000f),
    HPF_(R4(0)),
    VCF(0.200f, 0.000f, 0.600f, POL_POS, 0.000f, 0.800f),
    VCA(0.500f, VCA_ENV),
    ENV(0.000f, 0.550f, 0.300f, 0.600f),
    CHOR(CH_I),
    SYS(TRIG_MAN , OCT0) }},

{ "Reed 3", {
    LFO(0.600f, 0.200f),
    DCO(F4 , 0.200f, 0.500f, PWM_MAN,
        OFF, OFF, ON , 1.000f, 0.000f),
    HPF_(R4(0)),
    VCF(0.300f, 0.200f, 0.300f, POL_POS, 0.000f, 1.000f),
    VCA(0.600f, VCA_ENV),
    ENV(0.250f, 0.000f, 1.000f, 0.200f),
    CHOR(CH_OFF),
    SYS(TRIG_MAN , OCT0) }},

{ "PWM Chorus", {
    LFO(0.300f, 0.000f),
    DCO(F8 , 0.000f, 0.500f, PWM_LFO,
        OFF, ON , ON , 1.000f, 0.000f),
    HPF_(R4(0)),
    VCF(0.800f, 0.000f, 0.000f, POL_POS, 0.000f, 1.000f),
    VCA(0.200f, VCA_ENV),
    ENV(0.300f, 0.000f, 1.000f, 0.400f),
    CHOR(CH_II),
    SYS(TRIG_MAN , OCT0) }},

{ "Synth Organ", {
    LFO(0.450f, 0.600f),
    DCO(F8 , 0.000f, 0.650f, PWM_MAN,
        OFF, ON , ON , 0.750f, 0.000f),
    HPF_(R4(0)),
    VCF(0.250f, 0.000f, 0.500f, POL_POS, 0.200f, 0.700f),
    VCA(0.500f, VCA_GATE),
    ENV(0.000f, 0.200f, 0.500f, 0.250f),
    CHOR(CH_II),
    SYS(TRIG_AUTO, OCT0) }},

{ "Effect Sound 1", {
    LFO(0.450f, 0.600f),
    DCO(F4 , 0.150f, 1.000f, PWM_MAN,
        ON , ON , ON , 0.700f, 0.000f),
    HPF_(R4(0)),
    VCF(0.650f, 0.000f, 0.450f, POL_NEG, 0.000f, 0.700f),
    VCA(0.700f, VCA_ENV),
    ENV(0.000f, 0.500f, 0.000f, 0.550f),
    CHOR(CH_I),
    SYS(TRIG_AUTO, OCT0) }},

{ "Effect Sound 2", {
    LFO(0.550f, 0.900f),
    DCO(F8 , 0.000f, 0.300f, PWM_LFO,
        ON , OFF, ON , 0.650f, 0.000f),
    HPF_(R4(0)),
    VCF(0.650f, 0.300f, 0.400f, POL_NEG, 0.000f, 0.100f),
    VCA(0.400f, VCA_GATE),
    ENV(0.650f, 0.550f, 0.200f, 0.650f),
    CHOR(CH_I),
    SYS(TRIG_AUTO, OCT0) }},

{ "Space Harp", {
    LFO(0.550f, 0.000f),
    DCO(F8 , 0.200f, 0.000f, PWM_ENV,
        ON , OFF, OFF, 0.000f, 0.000f),
    HPF_(R4(0)),
    VCF(0.650f, 0.500f, 0.550f, POL_POS, 0.000f, 1.000f),
    VCA(0.600f, VCA_ENV),
    ENV(0.000f, 0.800f, 0.800f, 0.900f),
    CHOR(CH_I),
    SYS(TRIG_AUTO, OCT0) }},

{ "Funk", {
    LFO(0.300f, 0.250f),
    DCO(F8 , 0.000f, 0.600f, PWM_MAN,
        ON , ON , ON , 1.000f, 0.000f),
    HPF_(R4(0)),
    VCF(0.750f, 0.600f, 0.500f, POL_NEG, 0.000f, 0.450f),
    VCA(0.200f, VCA_GATE),
    ENV(0.600f, 0.500f, 0.000f, 0.000f),
    CHOR(CH_I),
    SYS(TRIG_AUTO, OCT0) }},

{ "Space Sound 1", {
    LFO(0.600f, 0.700f),
    DCO(F8 , 0.200f, 0.450f, PWM_MAN,
        OFF, ON , ON , 1.000f, 0.000f),
    HPF_(R4(0)),
    VCF(0.650f, 0.700f, 0.550f, POL_NEG, 0.000f, 1.000f),
    VCA(0.300f, VCA_GATE),
    ENV(0.000f, 0.800f, 0.000f, 0.300f),
    CHOR(CH_I),
    SYS(TRIG_AUTO, OCT0) }},

{ "Mysterious Inv", {
    LFO(0.600f, 0.800f),
    DCO(F8 , 0.200f, 0.800f, PWM_ENV,
        ON , ON , OFF, 1.000f, 0.000f),
    HPF_(R4(0)),
    VCF(0.800f, 0.700f, 0.600f, POL_NEG, 0.250f, 0.000f),
    VCA(0.500f, VCA_ENV),
    ENV(0.000f, 1.000f, 0.000f, 1.000f),
    CHOR(CH_OFF),
    SYS(TRIG_AUTO, OCT0) }},

{ "Space Sound 2", {
    LFO(0.300f, 0.300f),
    DCO(F8 , 0.000f, 0.600f, PWM_MAN,
        ON , ON , OFF, 0.800f, 0.000f),
    HPF_(R4(0)),
    VCF(0.200f, 0.850f, 0.600f, POL_POS, 0.000f, 1.000f),
    VCA(0.200f, VCA_ENV),
    ENV(1.000f, 1.000f, 1.000f, 1.000f),
    CHOR(CH_I),
    SYS(TRIG_AUTO, OCT0) }},

{ "Percussive Sd1", {
    LFO(0.000f, 0.000f),
    DCO(F4 , 0.000f, 0.000f, PWM_ENV,
        OFF, OFF, OFF, 0.000f, 1.000f),
    HPF_(R4(1)),
    VCF(0.400f, 1.000f, 0.150f, POL_POS, 0.000f, 1.000f),
    VCA(1.000f, VCA_ENV),
    ENV(0.000f, 0.300f, 0.000f, 0.400f),
    CHOR(CH_OFF),
    SYS(TRIG_AUTO, OCT0) }},

{ "Percussive Sd2", {
    LFO(0.000f, 0.000f),
    DCO(F8 , 0.000f, 0.000f, PWM_ENV,
        OFF, OFF, OFF, 0.000f, 0.000f),
    HPF_(R4(1)),
    VCF(0.500f, 1.000f, 0.350f, POL_NEG, 0.000f, 1.000f),
    VCA(1.000f, VCA_ENV),
    ENV(0.000f, 0.300f, 0.000f, 0.400f),
    CHOR(CH_OFF),
    SYS(TRIG_AUTO, OCT0) }},

{ "Whistle", {
    LFO(0.550f, 0.500f),
    DCO(F4 , 0.000f, 0.000f, PWM_MAN,
        OFF, OFF, OFF, 0.000f, 0.200f),
    HPF_(R4(1)),
    VCF(0.350f, 1.000f, 0.150f, POL_POS, 0.200f, 1.000f),
    VCA(0.800f, VCA_ENV),
    ENV(0.300f, 0.000f, 1.000f, 0.100f),
    CHOR(CH_OFF),
    SYS(TRIG_AUTO, OCT0) }},

{ "Effect Sound 3", {
    LFO(0.550f, 0.400f),
    DCO(F8 , 0.000f, 0.000f, PWM_ENV,
        OFF, OFF, OFF, 0.000f, 0.000f),
    HPF_(R4(1)),
    VCF(0.350f, 1.000f, 0.000f, POL_POS, 0.200f, 1.000f),
    VCA(1.000f, VCA_ENV),
    ENV(0.000f, 0.400f, 0.550f, 0.700f),
    CHOR(CH_OFF),
    SYS(TRIG_AUTO, OCT0) }},

{ "UFO", {
    LFO(0.600f, 0.000f),
    DCO(F4 , 0.000f, 0.000f, PWM_MAN,
        OFF, OFF, OFF, 0.000f, 0.200f),
    HPF_(R4(0)),
    VCF(0.000f, 1.000f, 0.700f, POL_POS, 0.400f, 1.000f),
    VCA(0.400f, VCA_ENV),
    ENV(0.000f, 0.600f, 1.000f, 0.800f),
    CHOR(CH_I),
    SYS(TRIG_AUTO, OCT0) }},

{ "Space Sound 3", {
    LFO(0.600f, 0.000f),
    DCO(F4 , 0.000f, 0.000f, PWM_MAN,
        OFF, OFF, OFF, 0.000f, 0.200f),
    HPF_(R4(0)),
    VCF(0.500f, 1.000f, 0.400f, POL_NEG, 0.000f, 1.000f),
    VCA(0.500f, VCA_ENV),
    ENV(0.000f, 1.000f, 0.000f, 0.800f),
    CHOR(CH_I),
    SYS(TRIG_AUTO, OCT0) }},

{ "Surf", {
    LFO(0.000f, 0.000f),
    DCO(F8 , 0.000f, 0.000f, PWM_ENV,
        OFF, OFF, OFF, 1.000f, 1.000f),
    HPF_(R4(0)),
    VCF(0.600f, 0.000f, 0.000f, POL_POS, 0.600f, 1.000f),
    VCA(0.900f, VCA_ENV),
    ENV(0.000f, 0.400f, 1.000f, 0.800f),
    CHOR(CH_OFF),
    SYS(TRIG_AUTO, OCT0) }},

{ "Synth Drum", {
    LFO(0.000f, 0.000f),
    DCO(F8 , 0.000f, 0.000f, PWM_ENV,
        OFF, OFF, OFF, 0.000f, 0.000f),
    HPF_(R4(0)),
    VCF(0.200f, 1.000f, 0.400f, POL_POS, 0.000f, 1.000f),
    VCA(0.600f, VCA_ENV),
    ENV(0.000f, 0.500f, 0.000f, 0.600f),
    CHOR(CH_OFF),
    SYS(TRIG_MAN , OCT0) }},

};

static_assert(sizeof(junoPrograms) / sizeof(junoPrograms[0]) == JUNO_NPROGRAMS,
              "patch table and JUNO_NPROGRAMS have drifted apart");
