Michi71/PicoVintageSynthCollection/instruments/PicoFaceJV/include/jv_engine/jv_engine.h

// PicoFaceJV sound engine -- a native re-implementation of the JV-880 voice
// architecture. It is NOT an emulation of the original hardware: it reads the
// same ROM data (multisample table, sample table, patch parameters) and runs
// its own pitch / TVF / TVA chain, calibrated against the reference emulator.
//
// Layout constants come from jv_tone_map.h, physical units from
// jv_calibration.h -- both in tools/jv_extract/, which also documents how they
// were measured.
//
// The engine never owns ROM data. On the RP2350 the wave ROM lives in flash and
// is read through XIP; on the host it is read into a buffer. Sample decoding is
// strictly sequential per voice (DPCM cannot be addressed at random), which is
// what keeps the flash access pattern cache-friendly.
#ifndef JV_ENGINE_H
#define JV_ENGINE_H

#include <stddef.h>
#include <stdint.h>

#include "jv_calibration.h"   // JV_CHORUS_MAX_DELAY sizes the effect buffers

namespace jv {

// Descrambled 4 MiB wave ROM plus the 256 KiB firmware ROM holding the tables.
struct RomView {
    const uint8_t* wave;   // waverom1 followed by waverom2, descrambled
    size_t         waveLen;
    const uint8_t* rom2;
    size_t         rom2Len;
};

struct Sample {
    uint32_t start, loop, end;   // 24-bit ROM addresses
    uint8_t  rootKey;
    uint16_t tune;               // 0x400 = neutral
    uint8_t  level;
    // Bit 0 of the record's flag byte: the loop ALTERNATES direction rather
    // than jumping back to the start. 85 of the 577 samples set it and they are
    // the long sustained ones -- median loop length 8998 against 152 for the
    // rest. Playing those as forward loops makes the sound repeat exactly once
    // per loop, which is audible as a throb at the loop rate.
    bool     bidir;
    // Bit 2: the chip walks the address DOWN instead of up. Fifteen samples set
    // it, 562..576, and they are exactly the fifteen belonging to the fourteen
    // multisamples named "REV ..." -- REV Crash 1, REV SN 1..4, REV TAMB and the
    // rest. Wave 96 "Crash 1" and wave 128 "REV Crash 1" settle what the bit
    // does between them: they name the SAME ROM region (163489..227837 against
    // 163488..227837) and differ only in this flag. The stored audio decays like
    // any cymbal, from -2 dB at 0.2 s to -19 dB at 1.8 s, so nothing but reading
    // it backwards can produce the swell the machine plays.
    bool     reverse;
};

enum : int {
    kMaxVoices  = 24,   // the original is 28; this is the Pico budget
    kControlDiv = 32,   // filter coefficients update at this rate, like the chip
    kRenderBlock = 64,  // render() chunks to this internally, so the effect
                        // buses can live in fixed-size scratch
};

class Engine {
public:
    bool init(const RomView& rom, uint32_t sampleRate);

    // A patch is 362 bytes in the layout of JvPatch. Either point at one inside
    // rom2 (selectPatch) or supply an edited copy (setPatch, which copies).
    bool selectPatch(int bank, int index);   // bank 0=User, 1=A, 2=B
    void setPatch(const uint8_t* patch362);

    // Modulation-matrix sources. Values are 0..127 and persist across notes.
    void modWheel(uint8_t v)     { srcMod_ = v; }
    void aftertouch(uint8_t v)   { srcAft_ = v; }
    void expression(uint8_t v)   { srcExp_ = v; }

    void noteOn(uint8_t note, uint8_t velocity);
    void noteOff(uint8_t note);
    void allNotesOff();

    // Overwrites the buffers; does not accumulate.
    void render(float* left, float* right, int frames);

    int  activeVoices() const;

    // Runtime polyphony cap, 1..kMaxVoices. Lowering it does not cut sounding
    // voices; the allocator steals the oldest once the cap is reached.
    void setVoiceLimit(int n);
    int  voiceLimit() const { return voiceLimit_; }
    const char* patchName() const { return reinterpret_cast<const char*>(patch_); }

    // Bend range of the selected patch, in semitones. Up is 0..+12 and lives in
    // the low nibble of the patch-common flags; down is a signed byte reaching
    // -48. The two are independent, and 24 of the 192 factory patches bend down
    // further than they bend up -- the guitar and lead patches, mostly.
    int bendUpSemis() const { return patch_ ? (patch_[24] & 15) : 2; }
    int bendDownSemis() const { return patch_ ? (int)(int8_t)patch_[23] : -2; }

    // Pitch trim, applied to every voice. Used by the host A/B harness to
    // calibrate against the reference emulator; 1.0 = no correction.
    void setPitchTrim(float ratio) { pitchTrim_ = ratio; }

    // Channel-wide scaling of the two effect sends, for CC91 and CC93 -- the
    // manual calls them Effect1 and Effect3 depth. 1.0 leaves the patch alone.
    void setSendScale(float rev, float cho) { revScale_ = rev; choScale_ = cho; }
    // CC5 and CC65 override the patch's own portamento time and switch. Pass
    // -1 to hand control back to the patch.
    void setPortaTimeOverride(int t)   { portaTimeOv_ = t; }
    void setPortaSwitchOverride(int s) { portaSwOv_ = s; }
    // MIDI mono / poly mode forces SOLO on or off whatever the patch says;
    // -1 hands the decision back to the patch.
    void setMonoOverride(int m) { monoOv_ = m; }

private:
    // Segment shape is direction-dependent, as measured: rising segments ramp
    // linearly in amplitude, falling ones decay linearly in dB. The time is the
    // segment's DURATION, not a rate -- at T1=80 the attack takes ~3.4 s whether
    // the target is level 64, 96 or 127. Treating it as a rate made every
    // segment whose target equals the current level collapse to nothing, which
    // is what made held pads stutter.
    struct Env {
        float level, target, slope, decay;
        float remaining;    // samples left in the current segment
        int   stage;        // 0..2 attack chain, 3 sustain, 4 release, 5 idle
        bool  rising;
        bool  segmentValid;
        const uint8_t* times;    // 4 bytes: T1 T2 T3 T4
        const uint8_t* levels;   // 3 bytes: L1 L2 L3
        uint32_t sr;
        bool  logLevels;   // TVA maps levels in dB, TVF near-linearly
        // Where the release segment lands. Zero for the TVA -- the manual is
        // explicit that its level after note-off becomes 0 -- but the TVF
        // envelope has a fourth LEVEL as well as a fourth time, and 95 of the
        // 539 factory tones set it non-zero. Releasing those to 0 slammed the
        // filter shut on note-off instead of letting it settle where the patch
        // asks.
        float releaseLevel;
        void  begin(const uint8_t* t, const uint8_t* l, uint32_t sampleRate,
                    bool logLevels, float releaseTo);
        void  release();
        float tick();
        bool  idle() const { return stage >= 5; }
    };

    // The pitch envelope. Separate from Env because it is bipolar (levels run
    // -63..+63 about zero, where the TVA and TVF levels are unsigned), because
    // it ramps linearly in cents in both directions rather than switching to a
    // dB decay when falling, and because it has a fourth level to release to
    // rather than returning to zero. It runs at control rate: nothing reads it
    // per sample.
    struct PEnv {
        float level, target, slope, remaining;
        int   stage;
        bool  segmentValid, used;
        const uint8_t* times;    // 4 bytes: T1 T2 T3 T4
        const int8_t*  levels;   // 4 bytes: L1 L2 L3 L4, signed
        float ctlRate;           // control ticks per second
        void  begin(const uint8_t* t, const int8_t* l, float controlRate);
        void  release();
        float tick();            // -1 .. +1
    };

    // Topology-preserving 2-pole state-variable filter. The obvious Chamberlin
    // form was tried first and is only accurate to about sr/6: at 32 kHz it
    // already erred by a third of an octave at cutoff parameter 56 and stopped
    // filtering altogether by 64, which is squarely inside the range the
    // modulation matrix reaches.
    struct Filter {
        float bp, lp;
        void  reset() { bp = lp = 0.0f; }
        float run(float in, float f, float q, int mode);
    };

    // One LFO. Runs at control rate, not per sample. `out` is UNIPOLAR: 1.0 is
    // the unmodulated value and 0.0 is full modulation, because both measured
    // destinations move one-sided downward from the set value.
    struct Lfo {
        float    phase;       // 0..1
        float    inc;         // phase per control tick
        int      wave;
        uint32_t rng;
        float    held;        // sample-and-hold value
        float    ramp;        // delay/fade envelope, 0..1
        float    delayTicks;  // remaining delay, in control ticks
        float    fadeInc;     // ramp increment per control tick
        bool     fadeOut;     // ramp away from full depth instead of towards it
        float    out;
        void begin(const uint8_t* p, uint32_t sr, int ctlDiv, uint32_t seed, float freePhase);
        void tick();
    };

    struct Voice {
        bool     active;
        uint8_t  note, velocity, tone;
        uint32_t addr;        // current integer ROM address
        uint32_t phase;       // Q16 fractional position
        uint32_t inc;         // Q16 increment, refreshed at control rate
        uint32_t baseInc;     // before pitch modulation
        int32_t  ref;         // DPCM accumulator (20 bit)
        int32_t  refAtLoop;   // accumulator when the loop point was first passed
        bool     loopSeen;    // ... and whether that has happened yet
        int8_t   dir;         // +1 forward, -1 retracing an alternating loop
        int32_t  sm1, s0, s1, s2;  // four consecutive decoded samples; the
                                   // output sits between s0 and s1 and the
                                   // other two are the B-spline's outer taps
        Sample   smp;
        Env      tva, tvf;
        PEnv     penv;
        Filter   filt;
        uint8_t  tvaT[4], tvaL[3], tvfT[4], tvfL[3];
        uint8_t  penvT[4];
        int8_t   penvL[4];
        float    penvDepthSemis;   // bipolar, +-12 semitones at full depth
        float    gainL, gainR;   // level and pan, BEFORE the output section
        float    dryGain;        // output dry level
        float    choGain;        // output chorus send
        float    revGain;        // output reverb send
        float    cutoffBase;  // parameter units, 0..127
        float    envDepth;    // bipolar TVF envelope depth, parameter units
        float    resonance;   // 0..127
        float    resMod;      // matrix contribution to it
        int      filtMode;
        float    coefF, coefQ; // filter coefficients, refreshed at control rate
        int      ctlPhase;
        Lfo      lfo[2];
        // Modulation matrix, flattened: three sources of four slots each, in
        // source order mod / aftertouch / expression.
        int8_t   matSens[12];
        uint8_t  matDest[12];
        float    lfoPitchDepth[2], lfoTvfDepth[2], lfoTvaDepth[2];  // cents / params / dB
        float    lfoGain;      // TVA modulation, linear, refreshed at control rate
        float    cutoffMod;    // TVF modulation, parameter units
        float    fxmK;         // FXM depth as a fraction of the playback rate, 0 = off
        // Portamento: an offset in cents that starts at the interval from the
        // previous note and ramps to zero. The glide is linear in cents, as
        // measured.
        float    portaCents;
        float    portaStep;    // cents per control tick, always toward zero
        int      delayRemaining;  // tone delay, samples still to wait
        bool     resoHard;        // resonance mode from +53 bit 7
        uint32_t age;
    };

    // Patch-common chorus: a stereo modulated delay whose two channels sweep in
    // antiphase. Depth sets how fast the delay slides (a constant pitch offset),
    // rate sets how often it turns around; see jv_calibration.h. 170 of the 192
    // factory patches use it.
    struct Chorus {
        float bufL[JV_CHORUS_MAX_DELAY]{}, bufR[JV_CHORUS_MAX_DELAY]{};
        int   pos = 0;
        float phase = 0.0f;      // 0..1 triangle
        float inc = 0.0f;        // phase per sample
        float excursion = 0.0f;  // samples
        float feedback = 0.0f;
        float level = 0.0f;      // 0 when the chorus is off
        bool  toReverb = false;
        void configure(const uint8_t* patchCommon, uint32_t sr);
        void reset();
        // Reads the send bus and adds its output to left/right.
        void process(const float* inL, const float* inR,
                     float* left, float* right, int n);
    };

    // Patch-common reverb. Two quite different things share the slot: six
    // algorithmic reverbs and two delays.
    //
    // The delays are exact -- time and feedback are both measured laws, and
    // PAN-DLY is the same line tapped at half the interval with the taps
    // alternating channels. The reverbs are not: what is measured is the decay
    // time, that the two channels come out decorrelated, and the level. The
    // network below is a Schroeder comb/allpass bank tuned to hit the measured
    // RT60. It is not the chip's topology and its early reflections will differ.
    struct Reverb {
        static constexpr int kCombs = 4;
        static constexpr int kCombMax = 1408;
        static constexpr int kApMax = 384;
        static constexpr int kDelayMax = 15872;   // 496 ms at 32 kHz

        float comb[2][kCombs][kCombMax]{};
        float ap[2][2][kApMax]{};
        float line[kDelayMax]{};           // for DELAY / PAN-DLY
        int   combPos[2][kCombs]{};
        int   apPos[2][2]{};
        int   linePos = 0;
        float combG[2][kCombs]{};
        int   combLen[2][kCombs]{};
        int   apLen[2][2]{};
        int   type = 0;
        int   delaySamples = 0;
        float feedback = 0.0f;
        float level = 0.0f;
        int   panTap = 0;                  // which side the next PAN-DLY tap hits
        int   panCount = 0;
        void configure(const uint8_t* patch, uint32_t sr);
        void reset();
        void process(const float* inL, const float* inR,
                     float* left, float* right, int n);
    };

    void renderBlock(float* left, float* right, int frames);
    int  allocVoice();
    void startVoice(Voice& v, int toneIndex, uint8_t note, uint8_t vel,
                    int fromNote);
    // Retunes the sounding voices to a new note without retriggering, which is
    // what SOLO legato does. Returns false if nothing was sounding.
    bool retuneVoices(uint8_t note, int fromNote);
    void beginGlide(Voice& v, int fromNote, uint8_t toNote);

    bool soloMode() const {
        if (monoOv_ >= 0) return monoOv_ != 0;
        return patch_ && (patch_[24] & JV_KEY_ASSIGN_SOLO_BIT);
    }
    bool portaOn() const {
        if (portaSwOv_ >= 0) return portaSwOv_ != 0;
        return patch_ && (patch_[24] & JV_PORTA_SWITCH_BIT);
    }
    int  portaTime() const {
        if (portaTimeOv_ >= 0) return portaTimeOv_;
        return patch_ ? (patch_[25] & 0x7F) : 0;
    }
    bool soloLegato() const { return patch_ && (patch_[24] & JV_SOLO_LEGATO_BIT); }
    bool portaLegatoOnly() const {
        return patch_ && (patch_[24] & JV_PORTA_MODE_LEGATO_BIT);
    }
    bool sampleFor(int waveNumber, uint8_t note, Sample& out) const;
    int  velocityIndex(int curve, uint8_t vel) const;
    int32_t decodeStep(Voice& v) const;
    void updateFilterCoeffs(Voice& v);
    void updateModulation(Voice& v, uint32_t clock);

    // Free-running LFO phases, advanced whenever any voice sounds. A voice
    // whose key-sync bit is clear adopts these at note-on instead of zero.
    float    freePhase_[2] = {0.0f, 0.0f};
    float    freeInc_[2] = {0.0f, 0.0f};
    RomView  rom_{};
    uint32_t sr_ = 32000;
    float    pitchTrim_ = 1.0f;
    uint8_t  srcMod_ = 0, srcAft_ = 0, srcExp_ = 0;
    const uint8_t* patch_ = nullptr;
    uint8_t  patchCopy_[362]{};
    Voice    voices_[kMaxVoices]{};
    uint32_t ageCounter_ = 0;
    // Free-running sample counter. FXM's modulator is a fixed 125 Hz square
    // derived from the sample clock, so it is one oscillator for the whole
    // machine, not one per voice -- voices sounding together must stay in step
    // with each other the way a hardware divider makes them.
    uint32_t clock_ = 0;
    // Notes currently held, most recent last. SOLO plays the last of them and
    // falls back to the one before when a key is released, which is what makes
    // a trill under one finger work.
    uint8_t  held_[16]{};
    int      heldN_ = 0;
    int      soloNote_ = -1;   // what the sounding voices are tuned to
    // When the previous note-on happened, for PLAY-MATE tone delay: the gap
    // between the last two note-ons becomes the delay.
    uint32_t lastNoteOn_ = 0;
    bool     haveLastNoteOn_ = false;
    float    revScale_ = 1.0f, choScale_ = 1.0f;
    int      portaTimeOv_ = -1, portaSwOv_ = -1, monoOv_ = -1;
    uint32_t panAlt_ = 0;      // toggles for tones set to alternating pan
    int      voiceLimit_ = kMaxVoices;
    Chorus   chorus_;
    Reverb   reverb_;
    float    choL_[kRenderBlock]{}, choR_[kRenderBlock]{};   // the send buses
    float    revL_[kRenderBlock]{}, revR_[kRenderBlock]{};
};

} // namespace jv

#endif // JV_ENGINE_H
