Michi71/PicoVintageSynthCollection/instruments/PicoFaceOB/include/obxf/Filter.h

/*
 * OB-Xd was originally written by Vadim Filatov, and then a version
 * was released under the GPL3 at https://github.com/reales/OB-Xd.
 * Subsequently, the product was continued by DiscoDSP and the copyright
 * holders as an excellent closed source product.
 *
 * This repository is a successor to OB-Xd version 2.11.
 * Copyright 2013-2025 by the authors as indicated in the original release,
 * and subsequent authors as per GitHub transaction log.
 *
 * OB-Xf is released under the GNU General Public Licence v3 or later
 * (GPL-3.0-or-later). The license is found in the file "LICENSE"
 * in the root of this repository or at:
 * https://www.gnu.org/licenses/gpl-3.0.en.html
 *
 * Source code is available at https://github.com/surge-synthesizer/OB-Xf
 */
/*
 * PORTED FOR PicoFaceOB (RP2350). Changes against the OB-Xf original:
 *   - double temporaries in the per-sample path -> float (2)
 *   - tan() -> ob_tan() (2)
 *   - two redundant divisions in the 4 pole path folded into lpc
 *   - atan() -> ob_atan() (1)
 */

#ifndef OBXF_SRC_ENGINE_FILTER_H
#define OBXF_SRC_ENGINE_FILTER_H

#include "obxf/ObxfPort.h"

#include "Voice.h"
#include <math.h>

class Filter
{
  private:
    // clang-format off
    constexpr static float poleMixFactors[NUM_XPANDER_MODES][5]
    {
        {0,  0,  0,  0,  1}, // LP4
        {0,  0,  0,  1,  0}, // LP3
        {0,  0,  1,  0,  0}, // LP2
        {0,  1,  0,  0,  0}, // LP1
        {1, -3,  3, -1,  0}, // HP3
        {1, -2,  1,  0,  0}, // HP2
        {1, -1,  0,  0,  0}, // HP1
        {0,  0,  2, -4,  2}, // BP4
        {0, -2,  2,  0,  0}, // BP2
        {1, -2,  2,  0,  0}, // N2
        {1, -3,  6, -4,  0}, // PH3
        {0, -1,  2, -1,  0}, // HP2+LP1
        {0, -1,  3, -3,  1}, // HP3+LP1
        {0, -1,  2, -2,  0}, // N2+LP1
        {0, -1,  3, -6,  4}, // PH3+LP1
    };
    // clang-format on

    struct State
    {
        float pole1{0.f};
        float pole2{0.f};
        float pole3{0.f};
        float pole4{0.f};

        float res2Pole{1.f};
        float res4Pole{0.f};

        float resCorrection{1.f};
        float resCorrectionInv{1.f};

        float multimodeXfade{0.f};
        int multimodePole{0};
    } state;

    float sampleRate{1.f};
    float sampleRateInv{1.f};

  public:
    struct Parameters
    {
        bool bpBlend2Pole{false};
        bool push2Pole{false};
        bool xpander4Pole{false};

        float multimode{0.f};
        uint8_t xpanderMode{0};
    } par;

    Filter() {}

    void reset()
    {
        state.pole1 = 0.f;
        state.pole2 = 0.f;
        state.pole3 = 0.f;
        state.pole4 = 0.f;
    }

    void setMultimode(float m)
    {
        par.multimode = m;
        state.multimodePole = (int)(par.multimode * 3);
        state.multimodeXfade = par.multimode * 3 - state.multimodePole;
    }

    inline void setSampleRate(float sr)
    {
        sampleRate = sr;
        sampleRateInv = 1.f / sampleRate;

        float rcRate = sqrt((44000.f / sampleRate));

        state.resCorrection = (970.f / 44000.f) * rcRate;
        state.resCorrectionInv = 1.f / state.resCorrection;
    }

    inline void setResonance(float res)
    {
        state.res2Pole = 1.f - res;
        state.res4Pole = (3.5f * res);
    }

    inline float diodePairResistanceApprox(float x)
    {
        // Taylor approximation of a slightly mismatched diode pair
        return (((((0.0103592f) * x + 0.00920833f) * x + 0.185f) * x + 0.05f) * x + 1.f);
    }

    inline float resolveFeedback2Pole(float sample, float g)
    {
        // calculating feedback non-linear transconducance and compensated for state.res2Pole(-1)
        float tCfb;

        // boosting non-linearity
        float push = -1.f - (par.push2Pole * 0.035f);

        tCfb = diodePairResistanceApprox(state.pole1 * 0.0876f) + push;

        // disable non-linearity (digital filter)
        // tCfb = 0;

        // resolve linear feedback
        float y = ((sample - 2.f * (state.pole1 * (state.res2Pole + tCfb)) - g * state.pole1 -
                    state.pole2) /
                   (1.f + g * (2.f * (state.res2Pole + tCfb) + g)));

        return y;
    }

    inline float apply2Pole(float sample, float g)
    {
        float gpw = ob_tan(g * sampleRateInv * pi);

        g = gpw;

        float v = resolveFeedback2Pole(sample, g);

        float y1 = v * g + state.pole1;
        state.pole1 = v * g + y1;

        float y2 = y1 * g + state.pole2;
        state.pole2 = y1 * g + y2;

        float out;

        if (par.bpBlend2Pole)
        {
            out = 2.f * (par.multimode < 0.5f
                             ? ((0.5f - par.multimode) * y2 + (par.multimode * y1))
                             : ((1.f - par.multimode) * y1 + (par.multimode - 0.5f) * v));
        }
        else
        {
            out = (1.f - par.multimode) * y2 + (par.multimode * v);
        }

        return out;
    }

    inline float resolveFeedback4Pole(float sample, float g, float lpc)
    {
        // ml = 1/(1+g) and lpc = g/(1+g), so ml is 1 - lpc. Saves a divide
        // per sample and voice; on this target a float divide is ~14 cycles.
        (void)g;
        float ml = 1.f - lpc;
        float S =
            (lpc * (lpc * (lpc * state.pole1 + state.pole2) + state.pole3) + state.pole4) * ml;
        float G = lpc * lpc * lpc * lpc;
        float y = (sample - state.res4Pole * S) / (1.f + state.res4Pole * G);

        return y;
    }

    inline float apply4Pole(float sample, float g)
    {
        float g1 = ob_tan(g * sampleRateInv * pi);
        g = g1;

        float lpc = g / (1.f + g);
        float y0 = resolveFeedback4Pole(sample, g, lpc);

        // first lowpass in the cascade
        float v = (y0 - state.pole1) * lpc;
        float res = v + state.pole1;

        state.pole1 = res + v;

        // damping
        state.pole1 = ob_atan(state.pole1 * state.resCorrection) * state.resCorrectionInv;

        // goveroneplusg is g/(1+g), which is exactly lpc computed above.
        const float goveroneplusg = lpc;
        float y1 = res;
        float y2 = tpt_process_scaled_cutoff(state.pole2, y1, goveroneplusg);
        float y3 = tpt_process_scaled_cutoff(state.pole3, y2, goveroneplusg);
        float y4 = tpt_process_scaled_cutoff(state.pole4, y3, goveroneplusg);
        float out;

        if (par.xpander4Pole)
        {
            out = (y0 * poleMixFactors[par.xpanderMode][0]) +
                  (y1 * poleMixFactors[par.xpanderMode][1]) +
                  (y2 * poleMixFactors[par.xpanderMode][2]) +
                  (y3 * poleMixFactors[par.xpanderMode][3]) +
                  (y4 * poleMixFactors[par.xpanderMode][4]);
        }
        else
        {
            switch (state.multimodePole)
            {
            case 0:
                out = ((1.f - state.multimodeXfade) * y4 + (state.multimodeXfade * y3));
                break;
            case 1:
                out = ((1.f - state.multimodeXfade) * y3 + (state.multimodeXfade * y2));
                break;
            case 2:
                out = ((1.f - state.multimodeXfade) * y2 + (state.multimodeXfade * y1));
                break;
            case 3:
                out = y1;
                break;
            default:
                out = 0.f;
                break;
            }
        }

        // half volume compensation
        return out * (1.f + state.res4Pole * 0.45f);
    }
};

#endif // OBXF_SRC_ENGINE_FILTER_H
