Michi71/PicoVintageSynthCollection/instruments/PicoFaceD5/src/D5_Instrument.cpp

// SPDX-License-Identifier: GPL-3.0-or-later
// SPDX-FileCopyrightText: 2026 Michi71

// D5_Instrument.cpp -- adapter binding the D-50 classes to
// picoface::Instrument. Everything runs on core0: the engine renders sixteen
// voices of two partials each without a core1 worker, so the optional hooks
// stay at their defaults except for the underrun governor.

#include <cstdio>
#include <cstring>

#include "picoface/instrument.h"

#include "D5_Bridge.h"
#include "D5_Controller.h"
#include "picoface/ui_kit.h"
#include "D5_Midi.h"
#include "d5_settings.h"
#include "audio_i2s.h"   // g_i2s_underrun_count, for the diagnostics footer

namespace {

class D5Instrument final : public picoface::Instrument {
public:
    D5Instrument() : controller_(bridge_), midi_(bridge_, controller_) {}

    const char* name() const override { return "PicoFaceD5"; }

    void init() override {
        bridge_.init();
        benchPct_ = bridge_.bootBenchPercent();
        D5SettingsV2 defaults{};
        controller_.exportSettings(defaults);
        controller_.importSettings(defaults);   // pushes them into the bridge
    }

    uint32_t sampleRate() const override { return bridge_.sampleRate(); }

    void render(int32_t* out, uint32_t frames) override {
        bridge_.fillBufferI32(out, (int)frames);
    }

    // Shedding voices on an underrun has to be temporary: a version that only
    // ever lowered the cap would ratchet down to the floor after one overload
    // and stay there. Recovery happens in uiTick().
    void onAudioUnderrun() override {
        const int n = bridge_.voiceLimit();
        if (n > kVoiceFloor) bridge_.setVoiceLimit(n - 1);
    }

    // A flash write stalls the CPU for milliseconds, which is audible.
    bool settingsSaveAllowed() const override { return bridge_.activeVoices() == 0; }

    void noteOn(uint8_t ch, uint8_t note, uint8_t vel) override { midi_.onNoteOn(ch, note, vel); }
    void noteOff(uint8_t ch, uint8_t note, uint8_t) override { midi_.onNoteOff(ch, note); }
    void controlChange(uint8_t ch, uint8_t cc, uint8_t v) override {
        // CC0, bank select: ahead of the next program change. The D-50
        // itself answers neither -- its memory ends at 64 -- but with the
        // D-05's six banks aboard this is how a host reaches past the
        // factory bank. Channel-blind, like programChange below.
        if (cc == 0) bankSel_ = v;
        midi_.onControlChange(ch, cc, v);
    }
    void pitchBend(uint8_t ch, int16_t bend) override { midi_.onPitchBend(ch, bend); }
    void channelPressure(uint8_t ch, uint8_t v) override { midi_.onChannelPressure(ch, v); }
    void sysEx(const uint8_t* data, size_t length) override {
        midi_.onSysEx(data, (uint16_t)length);
    }
    void programChange(uint8_t, uint8_t p) override {
        D5SettingsV2 s{};
        controller_.exportSettings(s);
        const int count = bridge_.patchCount();
        const int banks = (count + 63) / 64;
        int idx = (bankSel_ % banks) * 64 + p;
        if (idx >= count) idx = p % count;   // program byte beyond the table
        s.patch = (uint16_t)idx;
        controller_.importSettings(s);
        dirty_ = true;
    }

    // ---------------------------------------------------------------- GUI
    void uiInit(picoface::ui::Display& d) override { draw(d); }

    void uiTick(picoface::ui::Display& d, const picoface::ui::InputState& in) override {
        using picoface::ui::Encoder;
        const int8_t ds = in.delta(Encoder::Sel);
        const int8_t da = in.delta(Encoder::ParamA);
        const int8_t db = in.delta(Encoder::ParamB);

        // Voice governor recovery: one voice back per second of quiet, so a
        // passing overload does not cost polyphony for the rest of the
        // session. Deliberately slower than the cut, to avoid pumping.
        if (g_i2s_underrun_count != lastUnderrun_) {
            lastUnderrun_ = g_i2s_underrun_count;
            lastUnderrunMs_ = in.nowMs;
        } else if (bridge_.voiceLimit() < d5::kMaxVoicesPerTone &&
                   (in.nowMs - lastUnderrunMs_) > 1000u) {
            bridge_.setVoiceLimit(bridge_.voiceLimit() + 1);
            lastUnderrunMs_ = in.nowMs;
            dirty_ = true;
        }

        if (ds) { controller_.onEncoderSel(ds); dirty_ = true; }
        if (da) { controller_.onEncoderA(da); dirty_ = true; }
        if (db) { controller_.onEncoderB(db); dirty_ = true; }
        if ((dirty_ && (in.nowMs - lastDrawMs_) > 50u) || (in.nowMs - lastDrawMs_) > 500u) {
            draw(d, in.nowMs);
            dirty_ = false;
            lastDrawMs_ = in.nowMs;
        } else if (marquee_ && (in.nowMs - lastMarqueeMs_) >= 40u) {
            // The scrolling patch name: one band redrawn, one band flushed,
            // nothing else on the screen moves.
            marquee_ = picoface::ui::kit::marqueeTick(d, in.nowMs);
            lastMarqueeMs_ = in.nowMs;
        }
    }

    // -------------------------------------------------------- Persistence
    uint16_t settingsVersion() const override { return D5_SETTINGS_VERSION; }
    size_t settingsSize() const override { return sizeof(D5SettingsV2); }

    void settingsSave(uint8_t* buffer, size_t size) const override {
        if (size < sizeof(D5SettingsV2)) return;
        D5SettingsV2 s{};
        controller_.exportSettings(s);
        memcpy(buffer, &s, sizeof(s));
    }

    void settingsLoad(const uint8_t* buffer, size_t size) override {
        if (size < sizeof(D5SettingsV2)) return;   // short record: keep defaults
        D5SettingsV2 s{};
        memcpy(&s, buffer, sizeof(s));
        controller_.importSettings(s);
        dirty_ = true;
    }

private:
    void draw(picoface::ui::Display& d, uint32_t nowMs = 0) {
        namespace kit = picoface::ui::kit;
        marquee_ = false;

        // The developer's numbers went from a strip at the bottom of every page
        // to a page of their own (#161: that strip cost the body nine rows on
        // a screen with none to spare). Formatted here because only this
        // instrument knows what its numbers are; 6x12 holds 21 characters.
        if (controller_.isDiagPage()) {
            // The last number is the note counter while the render has room,
            // and the governor's rate -- tails retired per second -- whenever
            // it is working. A rate rather than a running total: the total
            // only ever climbs and cannot say whether the machine is coping.
            const unsigned long shed = (unsigned long)bridge_.shedRate();
            char r0[22], r1[22], r2[22], r3[22];
            snprintf(r0, sizeof r0, "CPU %d%%  bench %d",
                     bridge_.cpuLoadPeakPercent(), benchPct_);
            snprintf(r1, sizeof r1, "Underruns %lu",
                     (unsigned long)(g_i2s_underrun_count > 999 ? 999 : g_i2s_underrun_count));
            snprintf(r2, sizeof r2, "Voices %d/%d", bridge_.activeVoices(), bridge_.noteLimit());
            if (shed) snprintf(r3, sizeof r3, "Notes %lu  shed %lu",
                               (unsigned long)(bridge_.noteOnTotal() % 1000u), shed % 1000u);
            else      snprintf(r3, sizeof r3, "Notes %lu",
                               (unsigned long)(bridge_.noteOnTotal() % 1000u));
            const char* rows[4] = { r0, r1, r2, r3 };
            kit::diagnostics(d, controller_.pageName(), rows, 4);
            d.flush();
            return;
        }


        const D5_Controller::Value a = controller_.valueA();
        const D5_Controller::Value b = controller_.valueB();

        d.clear();
        kit::header(d, controller_.pageName(), controller_.pageIndex(),
                    controller_.pageTotal());
        if (controller_.isPatchPage()) {
            // Number and name apart: the number stays put, the name takes the
            // rest of the width and scrolls when it is longer than that. The
            // structure sits under it.
            char num[12];
            controller_.patchNumber(num, sizeof num);
            marquee_ = kit::panelName(d, num, controller_.patchName(), controller_.patchStructure(),
                                      { b.name, b.text, b.norm }, nowMs);
        } else {
            kit::panelDuo(d, { a.name, a.text, a.norm },
                             { b.name, b.text, b.norm });
        }

        // Arms the incremental push: the main loop streams out the rows whose
        // bit in the flush mask is set, and flush() sets all sixteen.
        d.flush();
    }

    static constexpr int kVoiceFloor = 2;
    int benchPct_ = 0;
    uint8_t bankSel_ = 0;          // CC0, pending on the next program change

    D5_Bridge bridge_;
    D5_Controller controller_;
    D5_Midi midi_;
    bool dirty_ = true;
    uint32_t lastDrawMs_ = 0;
    bool marquee_ = false;           // the patch name is scrolling; keep ticking it
    uint32_t lastMarqueeMs_ = 0;
    uint32_t lastUnderrun_ = 0;
    uint32_t lastUnderrunMs_ = 0;
};

} // namespace

PICOFACE_REGISTER_INSTRUMENT(D5Instrument)
